antmicro/rdimm-ddr5-tester/data-center-rdimm-ddr5-tester.kicad_sch

## KiCad design data-center-rdimm-ddr5-tester.kicad_sch (2026-05-25)

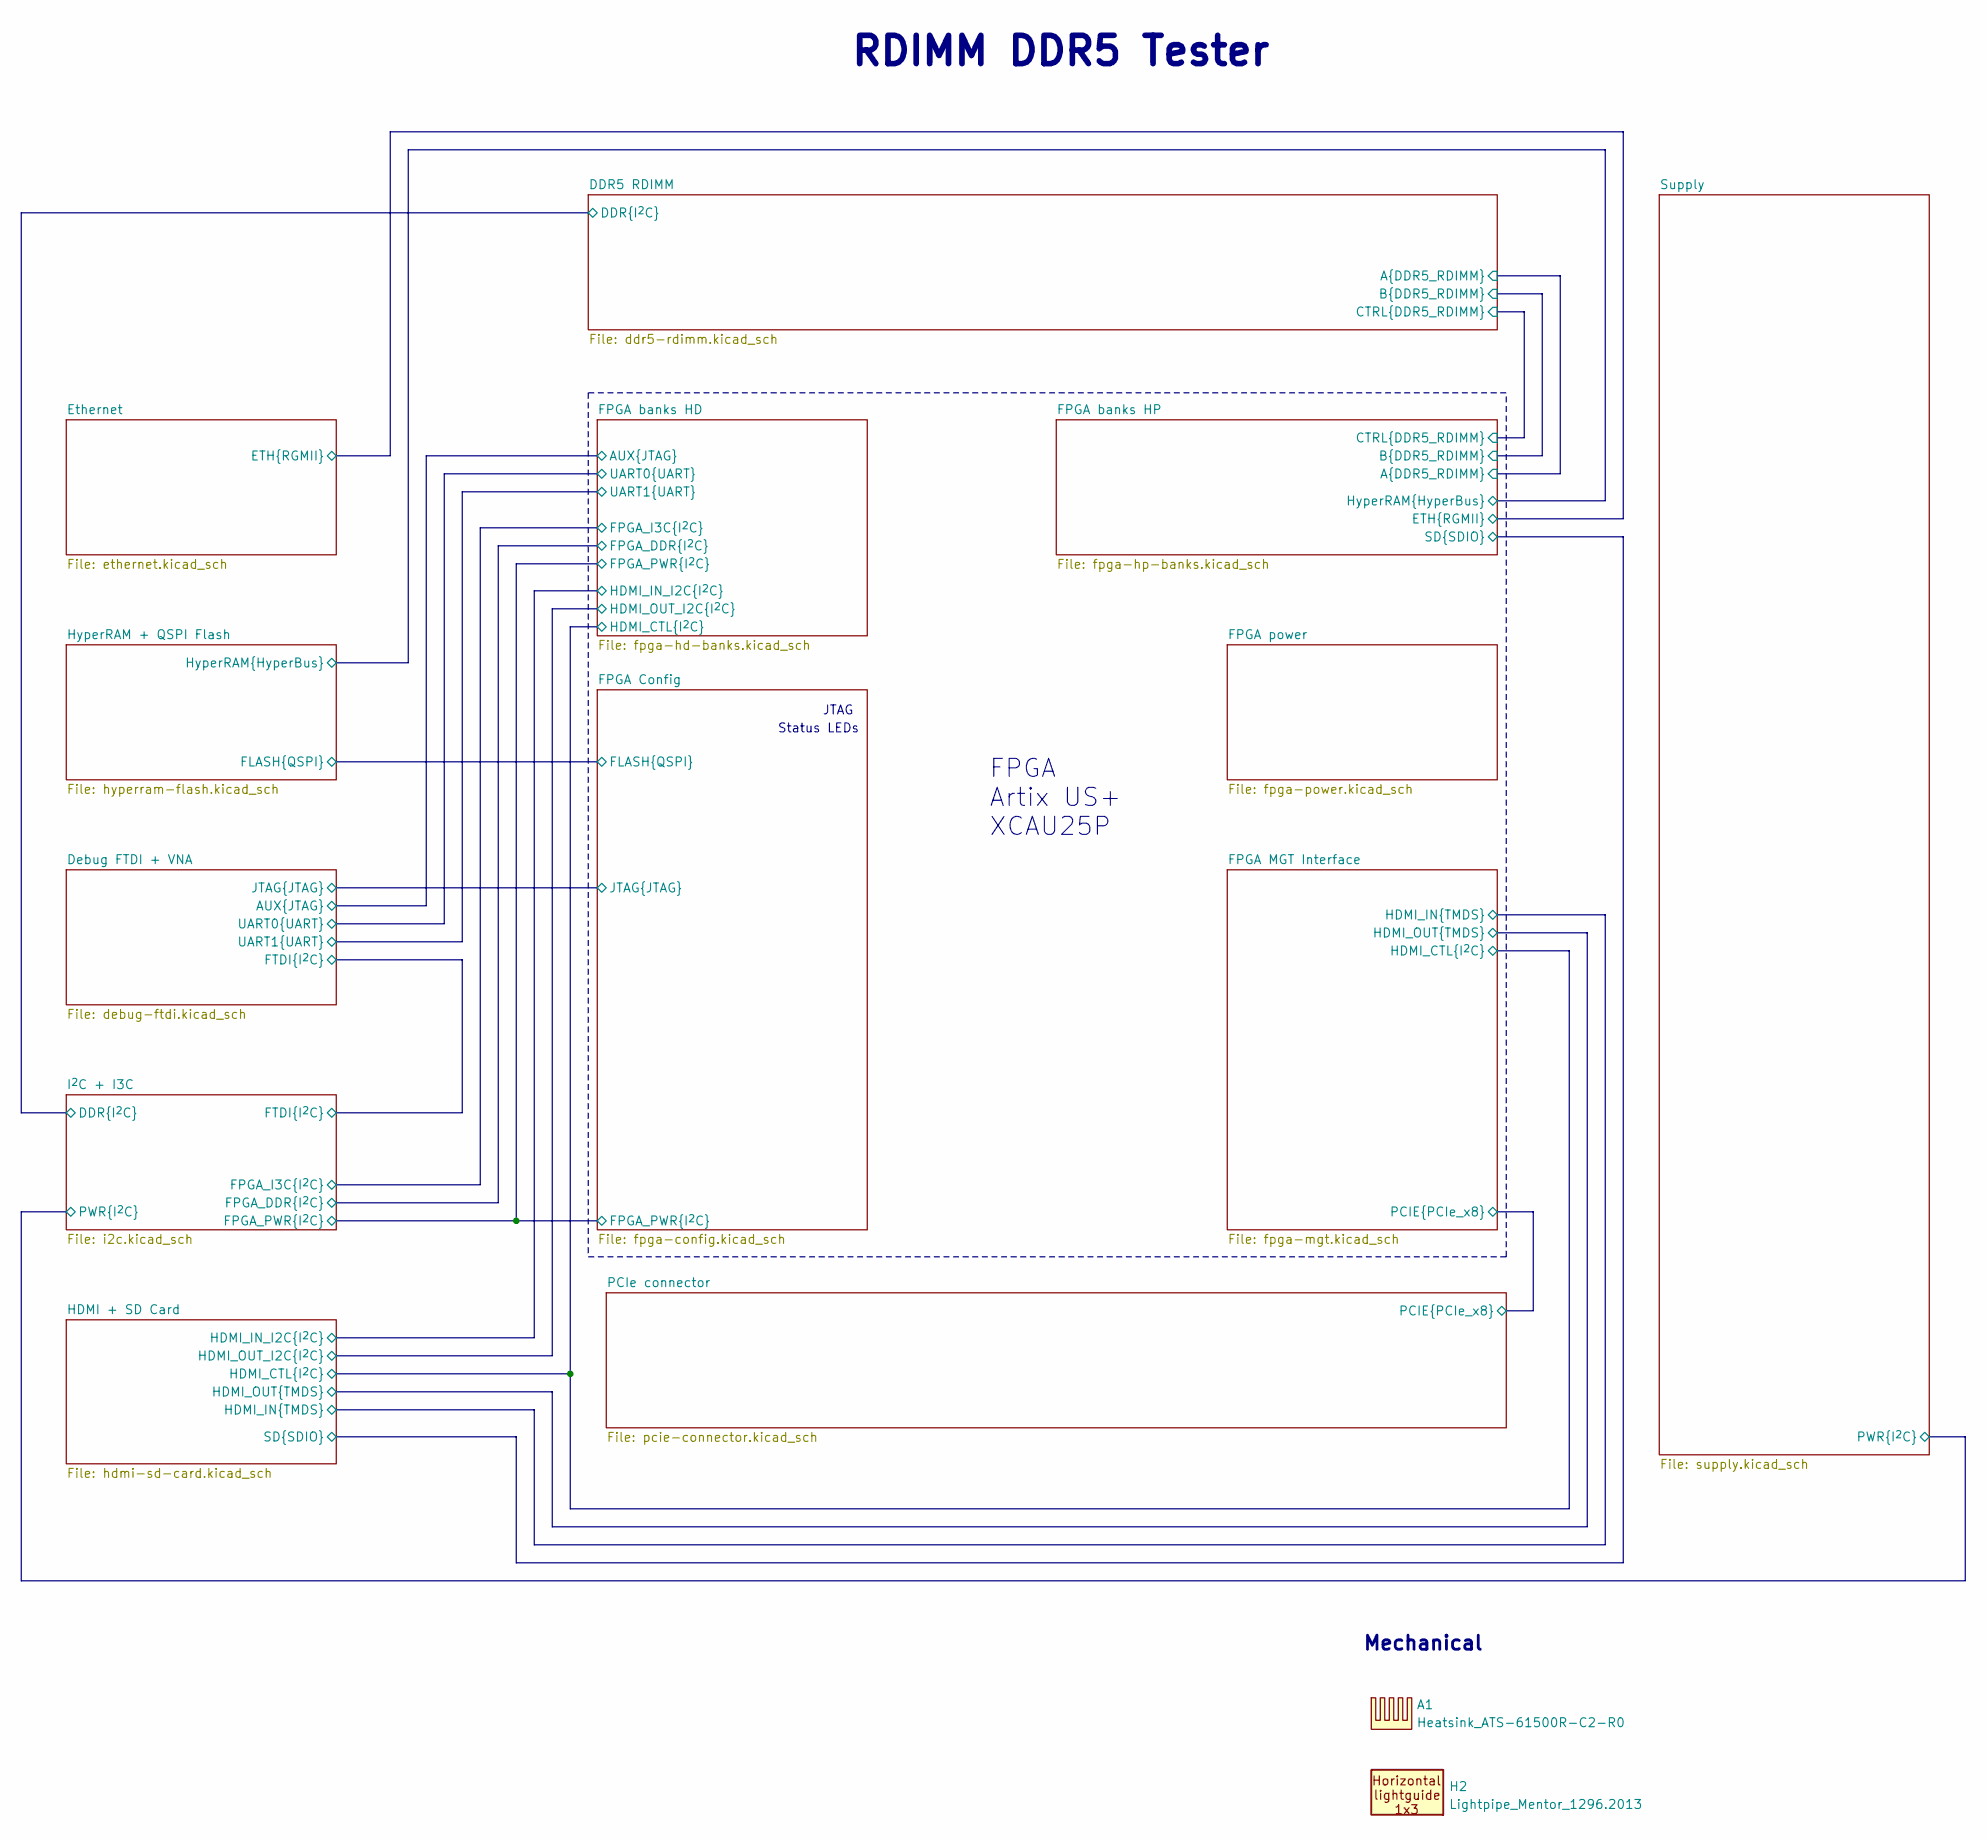
[picture p2: schematic data-center-rdimm-ddr5-tester.kicad_sch]

Parts:
A1: Heatsink_ATS-61500R-C2-R0; MPN ATS-61500R-C2-R0
H2: Lightpipe_Mentor_1296.2013; Mech_Lightpipe_Mentor_1296.2013; MPN 1296.2013

Notes on the sheet:
FPGA Artix US+ XCAU25P
JTAG
Mechanical
Status LEDs
RDIMM DDR5 Tester
