antmicro/rdimm-ddr5-tester/dc-dc-aux-mgt.kicad_sch

## KiCad design dc-dc-aux-mgt.kicad_sch (2026-05-25)

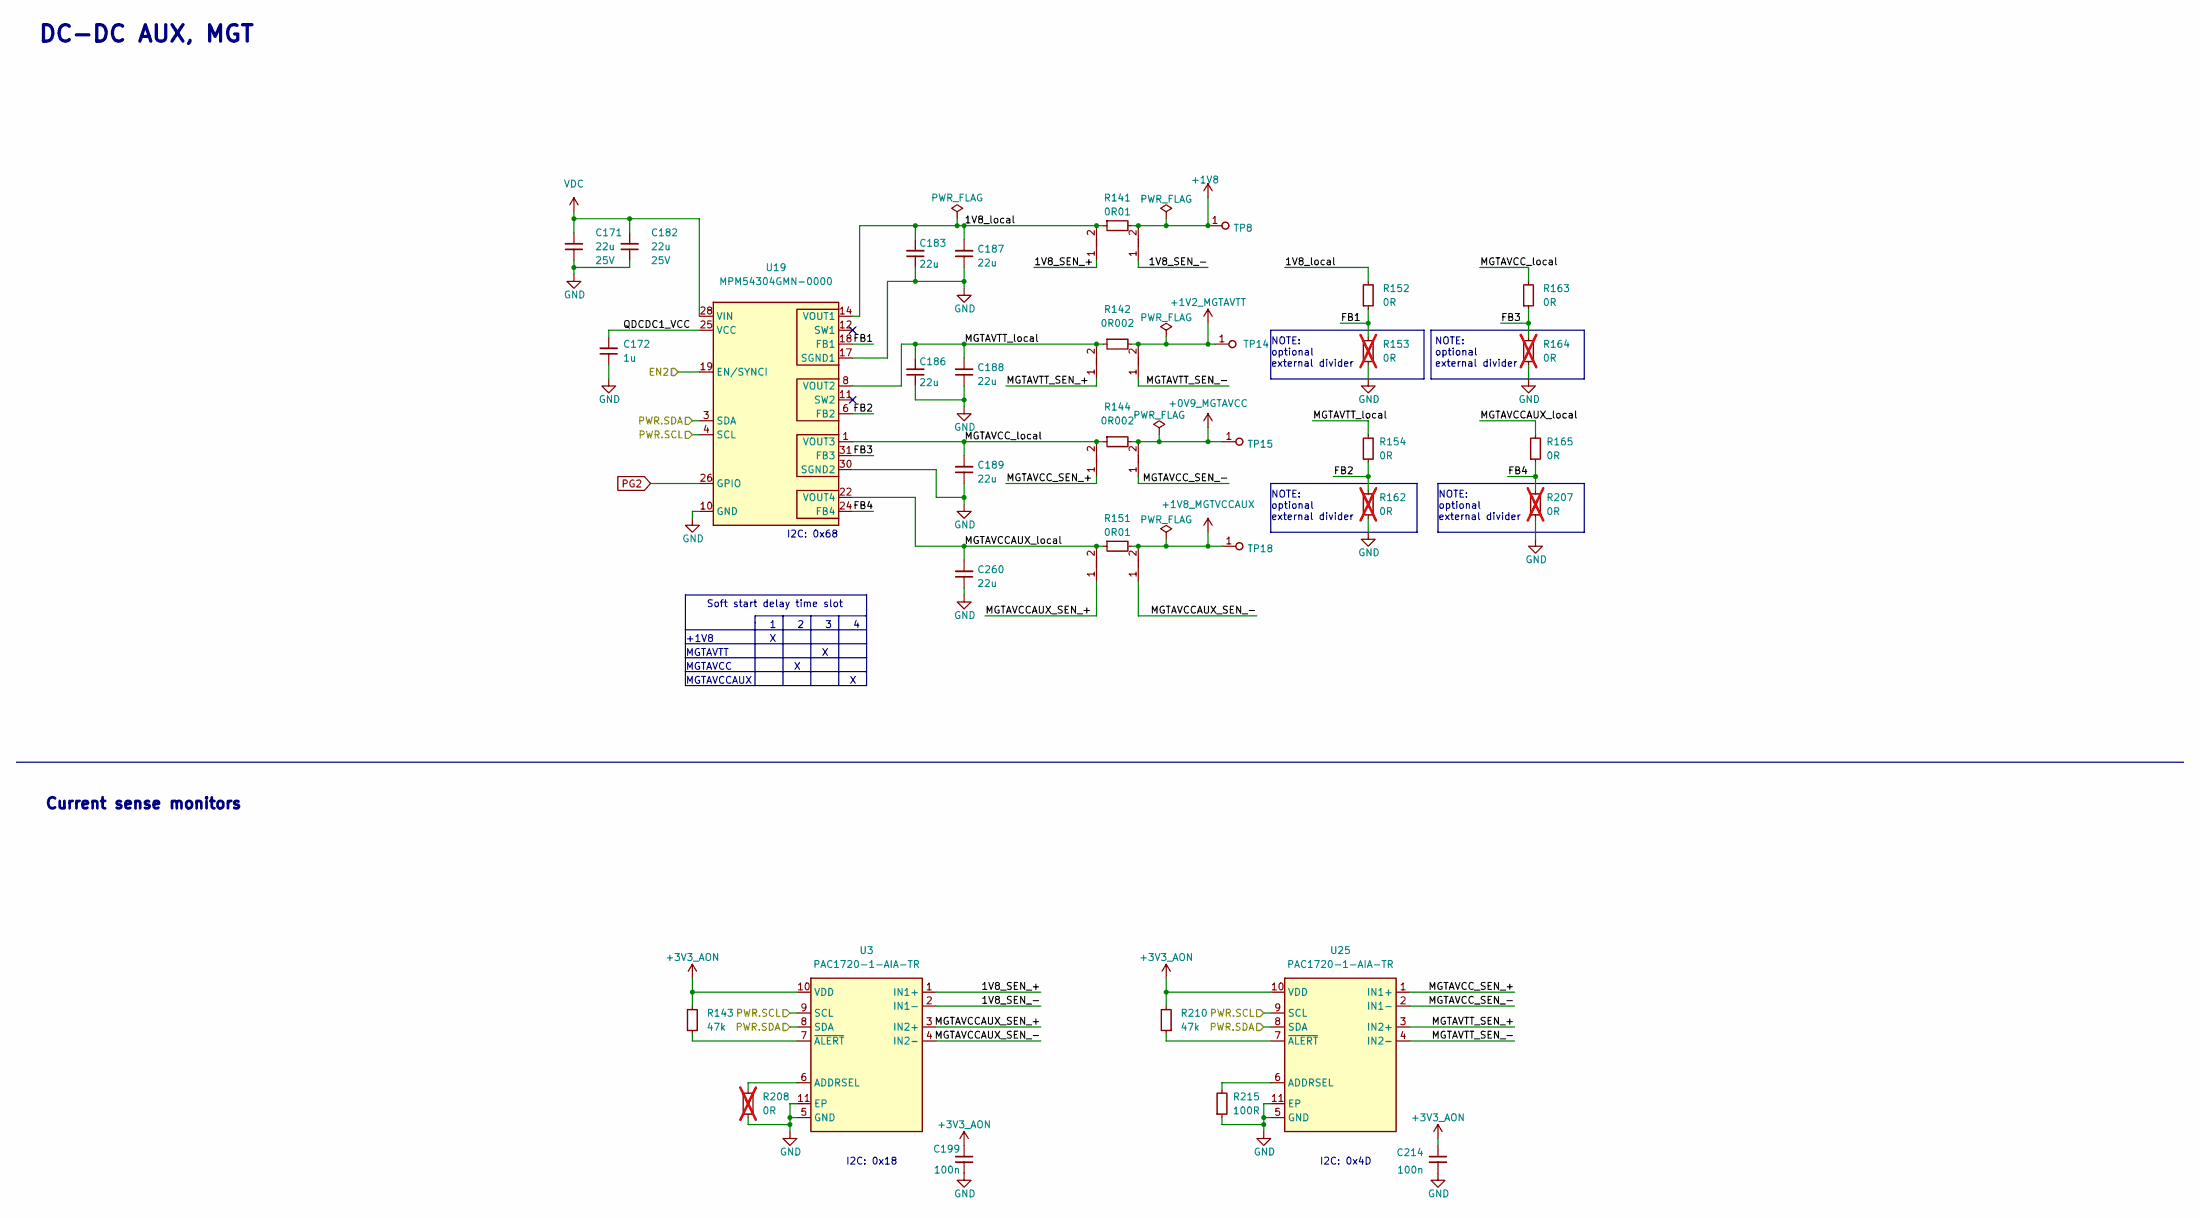
[picture p3: schematic dc-dc-aux-mgt.kicad_sch]

Parts:
C171, C182: C_22u_25V_0805; C_0805_2012Metric; Voltage 25V; MPN CL21A226MAYNNNE
C172: C_1u_0402; C_0402_1005Metric; MPN C1005X6S1A105K050BC
C183, C186, C187, C188, C189, C260: C_22u_0603; C_0603_1608Metric; MPN GRM188R60J226MEA0D
C199, C214: C_100n_0402; C_0402_1005Metric; Voltage 50V; MPN GRM155R61H104KE14D
NT1, NT2, NT3, NT4, NT9, NT10, NT11, NT12: Net-Tie_P0.127mm; NetTie-2_SMD_Pad0.127mm
R141, R151: R_0R01_1206; R_1206_3216Metric; Tolerance 1%; MPN RL1206FR-7W0R01L
R142, R144: R_0R002_0805; R_0805_2012Metric; Tolerance 1%; MPN PA0805FRE470R002L
R143, R210: R_47k_0402; R_0402_1005Metric; Tolerance 1%; MPN CR0402-FX-4702GLF
R152, R154, R163, R165: R_0R_0402; R_0402_1005Metric; MPN ERJ2GE0R00X
R153, R162, R164, R207, R208: R_0R_0402; R_0402_1005Metric; MPN ERJ2GE0R00X; not fitted
R215: R_100R_0402; R_0402_1005Metric; Tolerance 1%; MPN CR0402-FX-1000GLF
TP8, TP14, TP15, TP18: TP_1mm_SMD; TP_SMD_1mm
U3, U25: PAC1720-1; DFN-10-1EP_3x3mm; MPN PAC1720-1-AIA-TR
U19: MPM54304GMN; LGA-33_7x7mm_P0.65mm; MPN MPM54304GMN-0000

Connections:
1V8_SEN_+: NT1.1, U3.1 (IN1+)
1V8_SEN_-: NT9.1, U3.2 (IN1-)
1V8_local: C183.2, C187.2, NT1.2, R141.1, R152.2, U19.14 (VOUT1), U19.15 (VOUT1)
+0V9_MGTAVCC: NT11.2, R144.2, TP15.1
+1V2_MGTAVTT: NT10.2, R142.2, TP14.1
+1V8: NT9.2, R141.2, TP8.1
+1V8_MGTVCCAUX: NT12.2, R151.2, TP18.1
+3V3_AON: C199.1, C214.1, R143.2, R210.2, U3.10 (VDD), U25.10 (VDD)
EN2: U19.19 (EN/SYNCI)
FB1: R152.1, R153.2, U19.18 (FB1)
FB2: R154.1, R162.2, U19.6 (FB2)
FB3: R163.1, R164.2, U19.31 (FB3)
FB4: R165.1, R207.2, U19.24 (FB4)
GND: C171.1, C172.1, C182.1, C183.1, C186.1, C187.1, C188.1, C189.1, C199.2, C214.2, C260.1, R153.1, R162.1, R164.1, R207.1, R208.1, R215.1, U3.5 (GND), U3.11 (EP), U19.2 (GND), U19.5 (GND), U19.7 (GND), U19.10 (GND), U19.13 (GND), U19.16 (GND), U19.17 (SGND1), U19.20 (GND), U19.21 (GND), U19.27 (GND), U19.30 (SGND2), U19.33 (GND), U25.5 (GND), U25.11 (EP)
MGTAVCCAUX_SEN_+: NT4.1, U3.3 (IN2+)
MGTAVCCAUX_SEN_-: NT12.1, U3.4 (IN2-)
MGTAVCCAUX_local: C260.2, NT4.2, R151.1, R165.2, U19.22 (VOUT4), U19.23 (VOUT4)
MGTAVCC_SEN_+: NT3.1, U25.1 (IN1+)
MGTAVCC_SEN_-: NT11.1, U25.2 (IN1-)
MGTAVCC_local: C189.2, NT3.2, R144.1, R163.2, U19.1 (VOUT3), U19.32 (VOUT3)
MGTAVTT_SEN_+: NT2.1, U25.3 (IN2+)
MGTAVTT_SEN_-: NT10.1, U25.4 (IN2-)
MGTAVTT_local: C186.2, C188.2, NT2.2, R142.1, R154.2, U19.8 (VOUT2), U19.9 (VOUT2)
unnamed: R143.1, U3.7 (~ALERT)
unnamed: R208.2, U3.6 (ADDRSEL)
unnamed: R210.1, U25.7 (~ALERT)
unnamed: R215.2, U25.6 (ADDRSEL)
PG2: U19.26 (GPIO)
PWR.SCL: U3.9 (SCL), U19.4 (SCL), U25.9 (SCL)
PWR.SDA: U3.8 (SDA), U19.3 (SDA), U25.8 (SDA)
QDCDC1_VCC: C172.2, U19.25 (VCC)
VDC: C171.2, C182.2, U19.28 (VIN), U19.29 (VIN)

Notes on the sheet:
+1V8
NOTE: optional external divider
MGTAVTT
I2C: 0x4D
I2C: 0x18
Current sense monitors
DC-DC AUX, MGT
1 2 3 4
Soft start delay time slot
MGTAVCCAUX
I2C: 0x68
MGTAVCC
