antmicro/rdimm-ddr5-tester/dc-dc-io.kicad_sch

## KiCad design dc-dc-io.kicad_sch (2026-05-25)

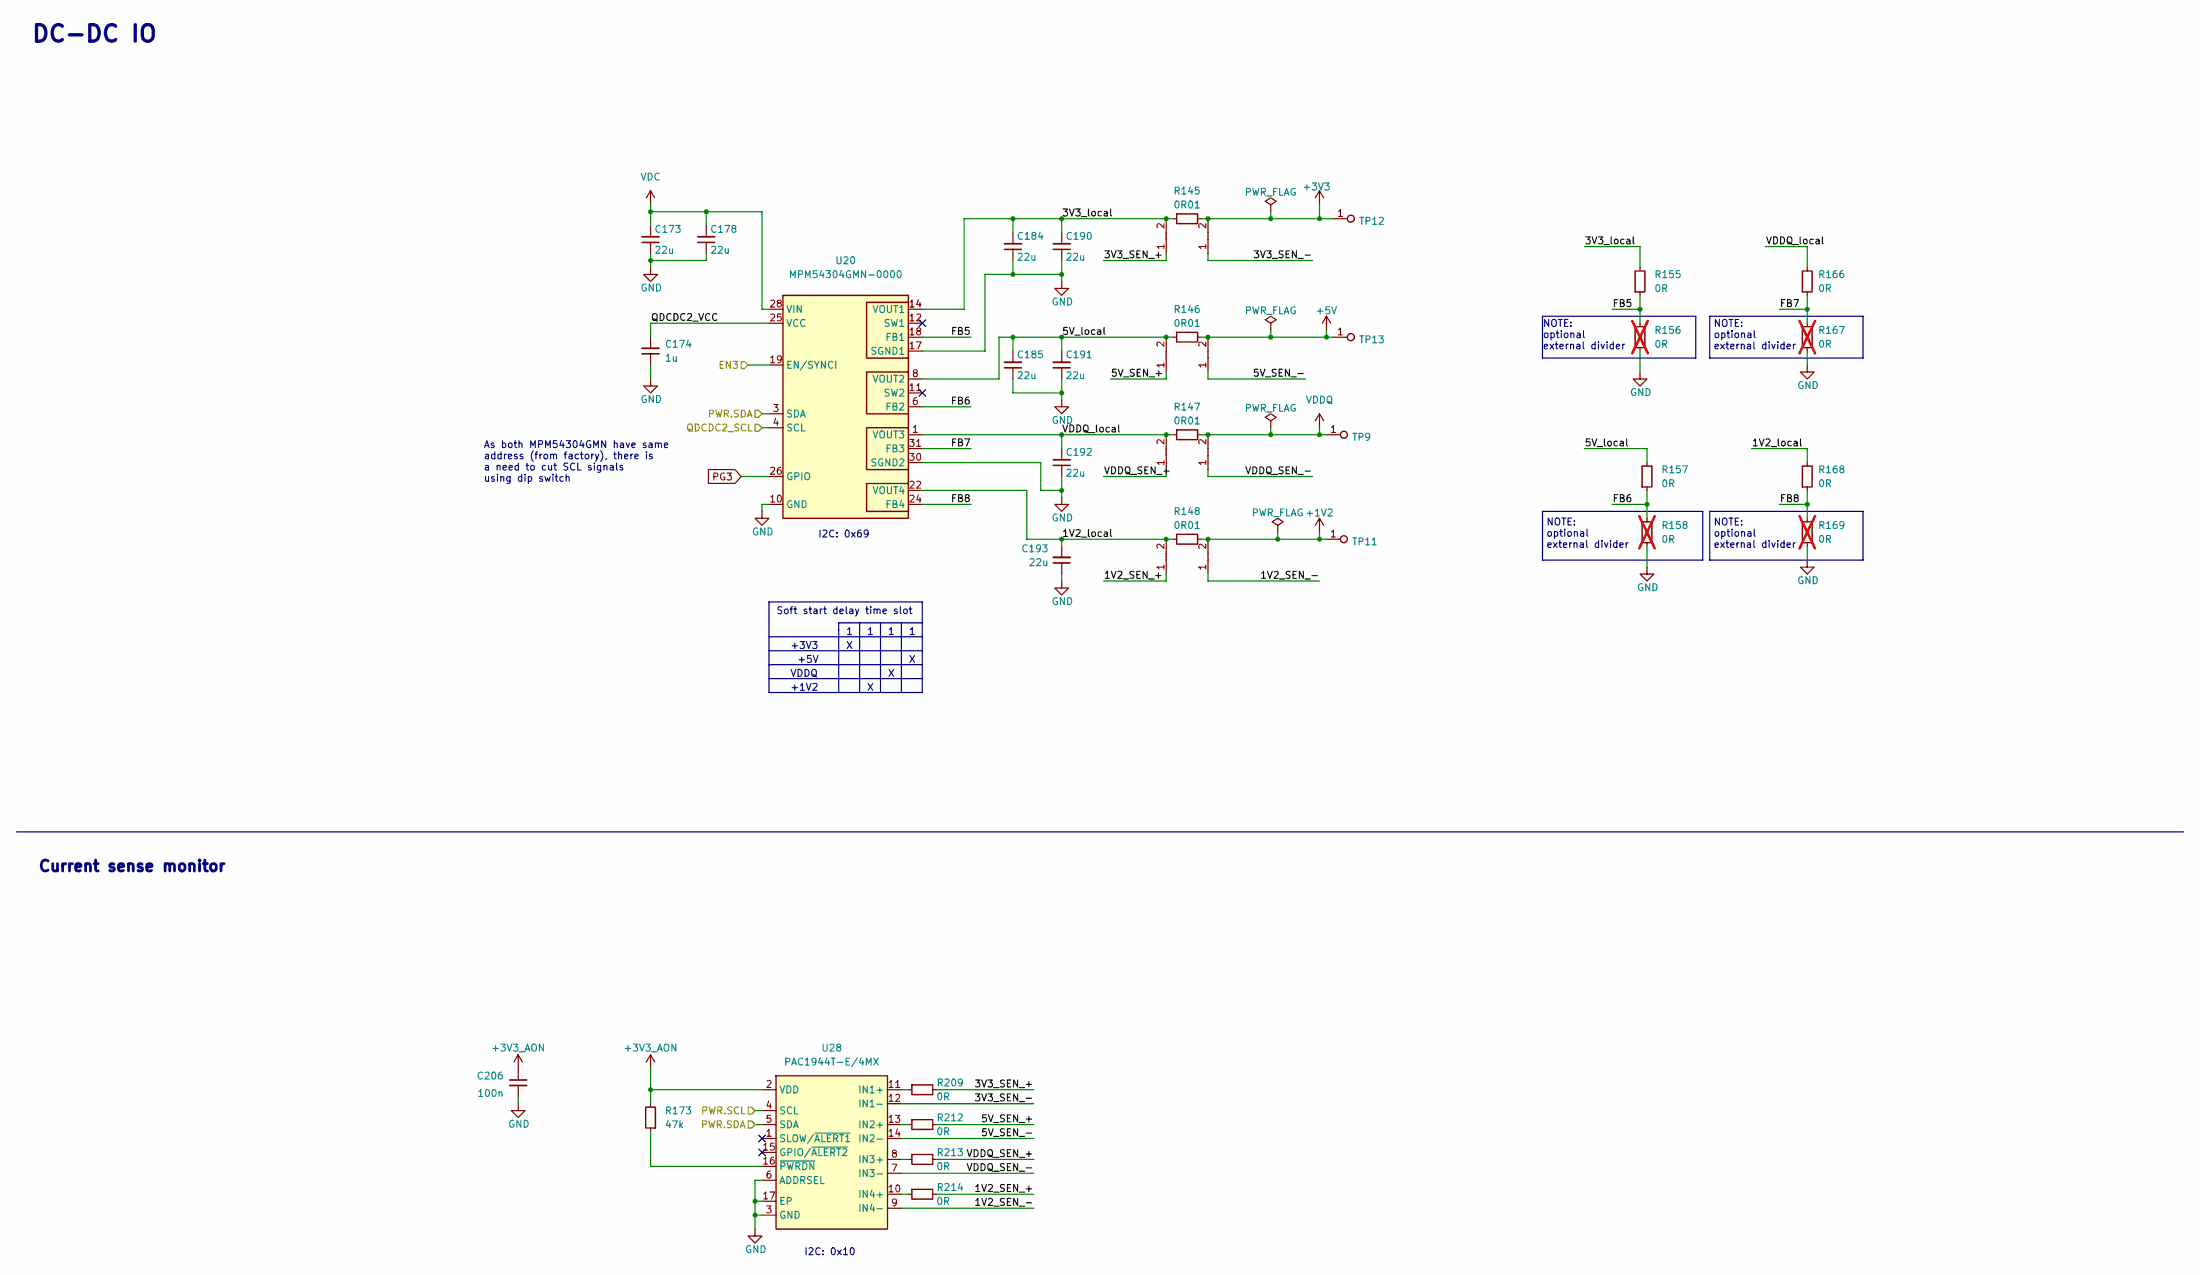
[picture p4: schematic dc-dc-io.kicad_sch]

Parts:
C173, C178: C_22u_25V_0805; C_0805_2012Metric; Voltage 25V; MPN CL21A226MAYNNNE
C174: C_1u_0402; C_0402_1005Metric; MPN C1005X6S1A105K050BC
C184, C185, C190, C191, C192, C193: C_22u_0603; C_0603_1608Metric; MPN GRM188R60J226MEA0D
C206: C_100n_0402; C_0402_1005Metric; Voltage 50V; MPN GRM155R61H104KE14D
NT5, NT6, NT7, NT8, NT13, NT14, NT15, NT16: Net-Tie_P0.127mm; NetTie-2_SMD_Pad0.127mm
R145, R146, R147, R148: R_0R01_1206; R_1206_3216Metric; Tolerance 1%; MPN RL1206FR-7W0R01L
R155, R157, R166, R168, R209, R212, R213, R214: R_0R_0402; R_0402_1005Metric; MPN ERJ2GE0R00X
R156, R158, R167, R169: R_0R_0402; R_0402_1005Metric; MPN ERJ2GE0R00X; not fitted
R173: R_47k_0402; R_0402_1005Metric; Tolerance 1%; MPN CR0402-FX-4702GLF
TP9, TP11, TP12, TP13: TP_1mm_SMD; TP_SMD_1mm
U20: MPM54304GMN; LGA-33_7x7mm_P0.65mm; MPN MPM54304GMN-0000
U28: PAC1944T-E; VQFN-16-1EP_3x3mm_P0.5mm_EP1.1x1.1mm; MPN PAC1944T-E/4MX

Connections:
1V2_SEN_+: NT8.1, R214.2
1V2_SEN_-: NT16.1, U28.9 (IN4-)
1V2_local: C193.2, NT8.2, R148.1, R168.2, U20.22 (VOUT4), U20.23 (VOUT4)
3V3_SEN_+: NT5.1, R209.2
3V3_SEN_-: NT13.1, U28.12 (IN1-)
3V3_local: C184.2, C190.2, NT5.2, R145.1, R155.2, U20.14 (VOUT1), U20.15 (VOUT1)
5V_SEN_+: NT6.1, R212.2
5V_SEN_-: NT14.1, U28.14 (IN2-)
5V_local: C185.2, C191.2, NT6.2, R146.1, R157.2, U20.8 (VOUT2), U20.9 (VOUT2)
+1V2: NT16.2, R148.2, TP11.1
+3V3: NT13.2, R145.2, TP12.1
+3V3_AON: C206.1, R173.2, U28.2 (VDD)
+5V: NT14.2, R146.2, TP13.1
EN3: U20.19 (EN/SYNCI)
FB5: R155.1, R156.2, U20.18 (FB1)
FB6: R157.1, R158.2, U20.6 (FB2)
FB7: R166.1, R167.2, U20.31 (FB3)
FB8: R168.1, R169.2, U20.24 (FB4)
GND: C173.1, C174.1, C178.1, C184.1, C185.1, C190.1, C191.1, C192.1, C193.1, C206.2, R156.1, R158.1, R167.1, R169.1, U20.2 (GND), U20.5 (GND), U20.7 (GND), U20.10 (GND), U20.13 (GND), U20.16 (GND), U20.17 (SGND1), U20.20 (GND), U20.21 (GND), U20.27 (GND), U20.30 (SGND2), U20.33 (GND), U28.3 (GND), U28.6 (ADDRSEL), U28.17 (EP)
unnamed: R173.1, U28.16 (~PWRDN)
unnamed: R209.1, U28.11 (IN1+)
unnamed: R212.1, U28.13 (IN2+)
unnamed: R213.1, U28.8 (IN3+)
unnamed: R214.1, U28.10 (IN4+)
PG3: U20.26 (GPIO)
PWR.SCL: U28.4 (SCL)
PWR.SDA: U20.3 (SDA), U28.5 (SDA)
QDCDC2_SCL: U20.4 (SCL)
QDCDC2_VCC: C174.2, U20.25 (VCC)
VDC: C173.2, C178.2, U20.28 (VIN), U20.29 (VIN)
VDDQ: NT15.2, R147.2, TP9.1
VDDQ_SEN_+: NT7.1, R213.2
VDDQ_SEN_-: NT15.1, U28.7 (IN3-)
VDDQ_local: C192.2, NT7.2, R147.1, R166.2, U20.1 (VOUT3), U20.32 (VOUT3)

Notes on the sheet:
+1V2
+3V3
Current sense monitor
DC-DC IO
VDDQ
As both MPM54304GMN have same address (from factory), there is a need to cut SCL signals using dip switch
NOTE: optional external divider
+5V
I2C: 0x10
I2C: 0x69
Soft start delay time slot
