antmicro/rdimm-ddr5-tester/dc-dc-vccint.kicad_sch

## KiCad design dc-dc-vccint.kicad_sch (2026-05-25)

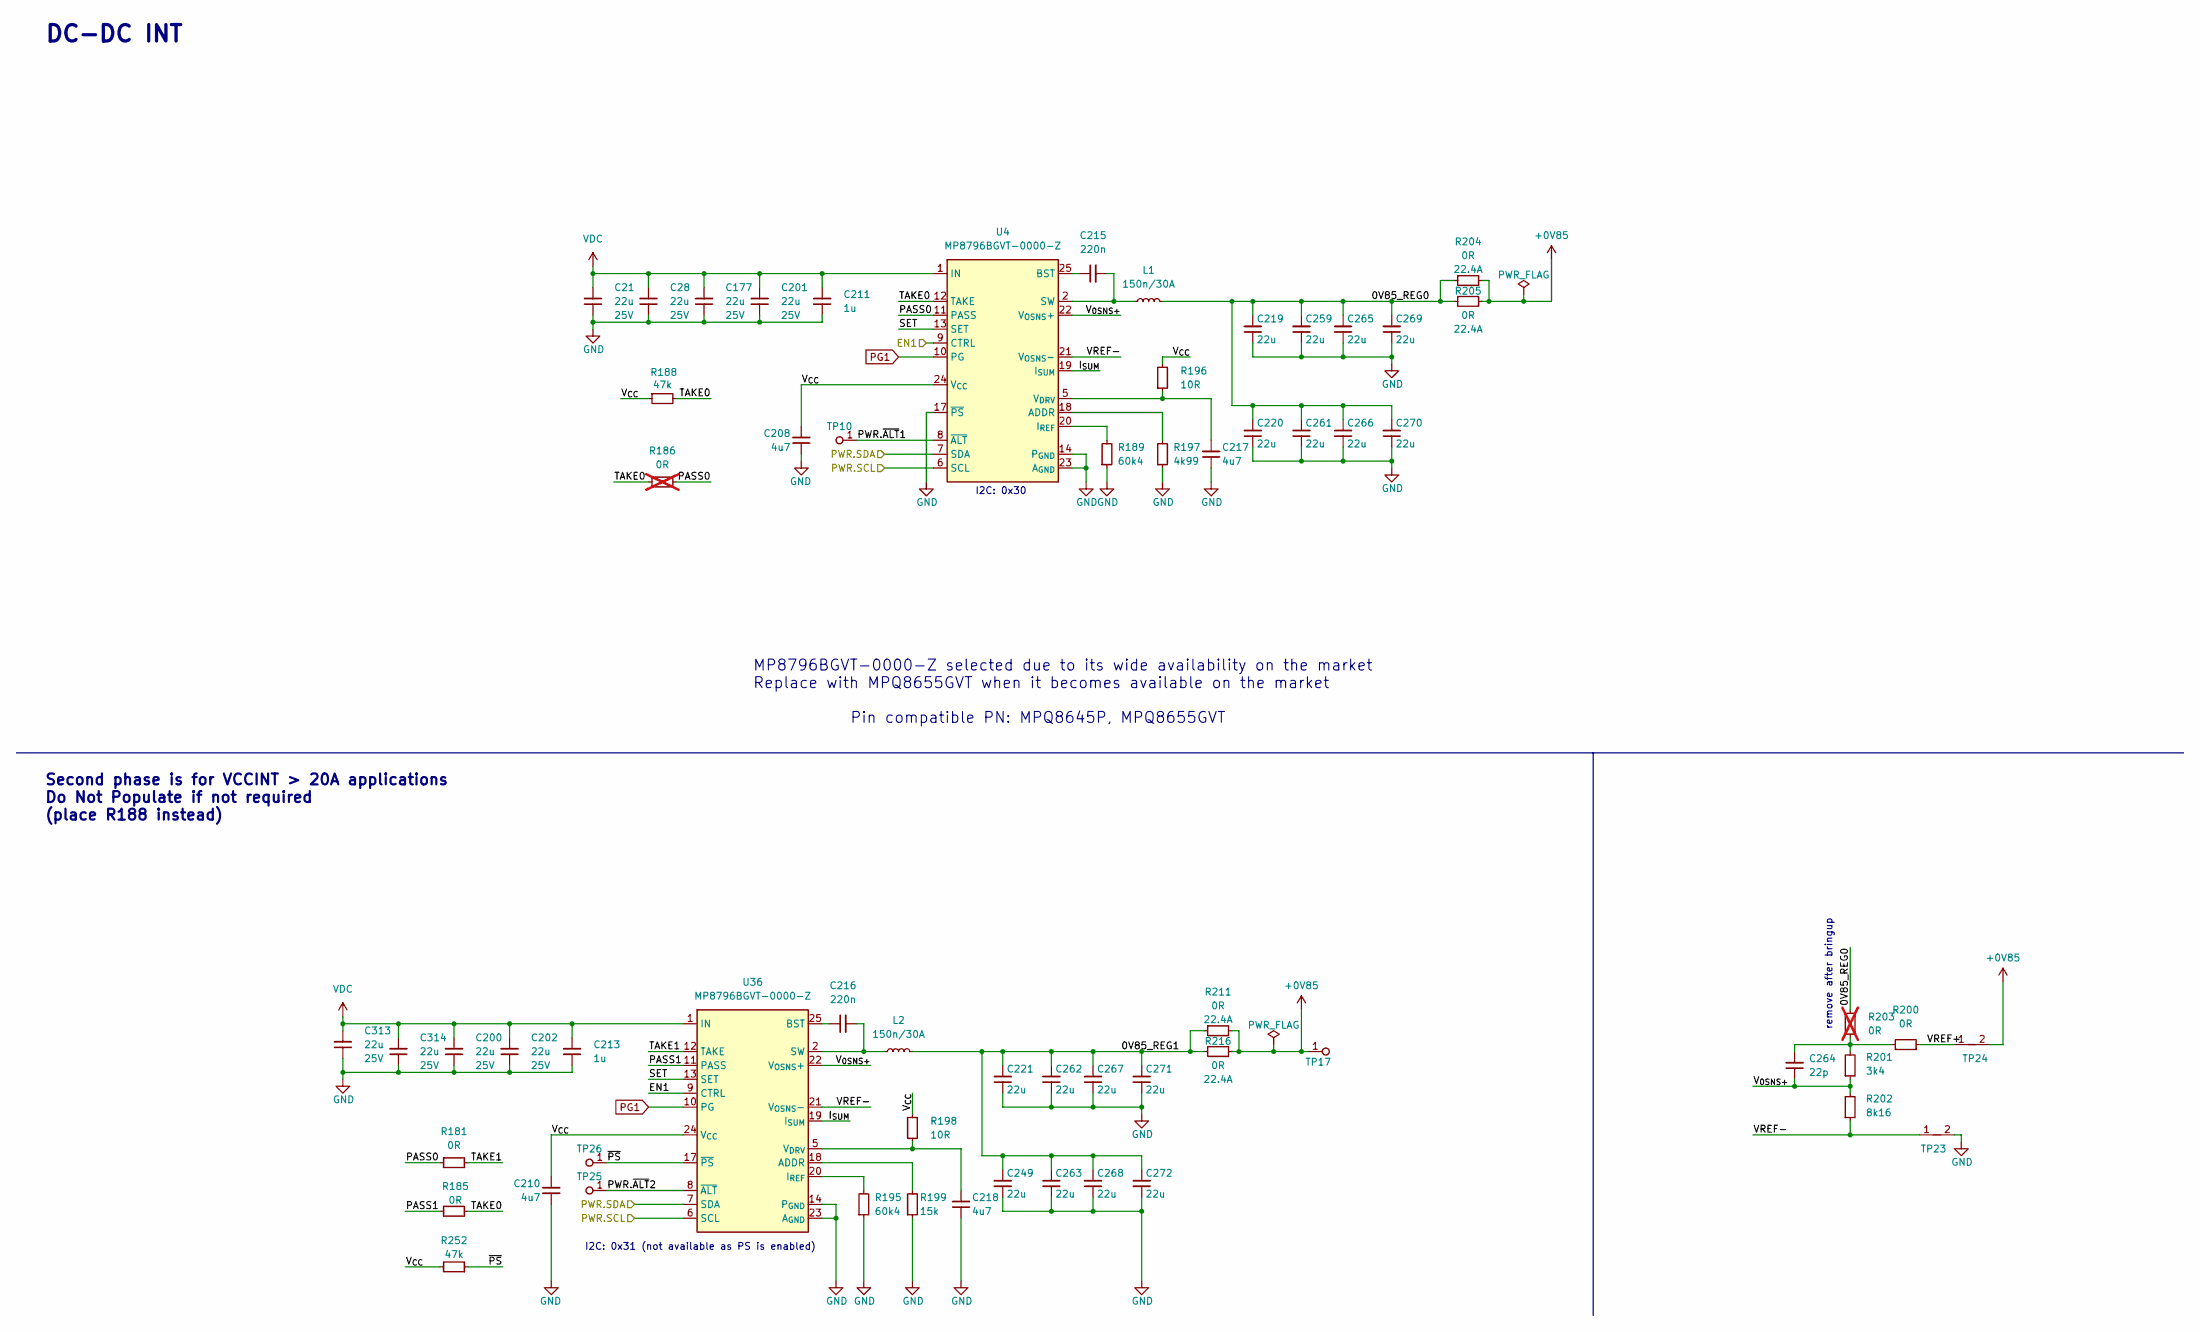
[picture p5: schematic dc-dc-vccint.kicad_sch]

Parts:
C21, C28, C177, C200, C201, C202, C313, C314: C_22u_25V_0805; C_0805_2012Metric; Voltage 25V; MPN CL21A226MAYNNNE
C208, C210, C217, C218: C_4u7_25V_0402; C_0402_1005Metric; Voltage 25V; MPN GRM155C61E475ME15J
C211, C213: C_1u_25V_0402; C_0402_1005Metric; Voltage 25V; MPN GRM155R61E105KE11J
C215, C216: C_220n_16V_0402; C_0402_1005Metric; Voltage 16V; MPN GRM155R71C224KA12D
C219, C220, C221, C249, C259, C261, C262, C263, C265, C266, C267, C268, C269, C270, C271, C272: C_22u_0603; C_0603_1608Metric; MPN GRM188R60J226MEA0D
C264: C_22p_0402; C_0402_1005Metric; MPN CC0402JRNPO9BN220
L1, L2: L_150n_30A_WE-HCM-7050; L_WE-HCM-7050; MPN 744302015
R181, R185, R200: R_0R_0402; R_0402_1005Metric; MPN ERJ2GE0R00X
R186, R203: R_0R_0402; R_0402_1005Metric; MPN ERJ2GE0R00X; not fitted
R188, R252: R_47k_0402; R_0402_1005Metric; Tolerance 1%; MPN CR0402-FX-4702GLF
R189, R195: R_60k4_0402; R_0402_1005Metric; Tolerance 1%; MPN CR0402-FX-6042GLF
R196, R198: R_10R_0402; R_0402_1005Metric; Tolerance 1%; MPN CR0402-FX-10R0GLF
R197: R_4k99_0402; R_0402_1005Metric; Tolerance 1%; MPN CR0402-FX-4991GLF
R199: R_15k_0402; R_0402_1005Metric; Tolerance 1%; MPN CR0402-FX-1502GLF
R201: R_3k4_0402; R_0402_1005Metric; Tolerance 0.1%; MPN RT0402BRD073K4L
R202: R_8k16_0402; R_0402_1005Metric; Tolerance 0.1%; MPN RT0402BRE078K16L
R204, R205, R211, R216: R_0R_22.4A_0603; R_0603_1608Metric; MPN PMR03EZPJ000
TP10, TP17, TP25, TP26: TP_1mm_SMD; TP_SMD_1mm
TP23, TP24: Net-Tie_P0.127mm; NetTie-2_SMD_Pad0.127mm
U4, U36: MP8796B; TQFN-25_4x5mm; MPN MP8796BGVT-0000-Z

Connections:
0V85_REG0: C219.2, C220.2, C259.2, C261.2, C265.2, C266.2, C269.2, C270.2, L1.2, R203.2, R204.1, R205.1
0V85_REG1: C221.2, C249.2, C262.2, C263.2, C267.2, C268.2, C271.2, C272.2, L2.2, R211.1, R216.1
+0V85: R204.2, R205.2, R211.2, R216.2, TP17.1, TP24.2
EN1: U4.9 (CTRL), U36.9 (CTRL)
GND: C21.1, C28.1, C177.1, C200.1, C201.1, C202.1, C208.1, C210.1, C211.1, C213.1, C217.1, C218.1, C219.1, C220.1, C221.1, C249.1, C259.1, C261.1, C262.1, C263.1, C265.1, C266.1, C267.1, C268.1, C269.1, C270.1, C271.1, C272.1, C313.1, C314.1, R189.1, R195.1, R197.1, R199.1, TP23.2, U4.4 (P_{GND}), U4.14 (P_{GND}), U4.15 (P_{GND}), U4.17 (~PS), U4.23 (A_{GND}), U36.4 (P_{GND}), U36.14 (P_{GND}), U36.15 (P_{GND}), U36.23 (A_{GND})
I_{SUM}: U4.19 (I_{SUM}), U36.19 (I_{SUM})
unnamed: C215.1, U4.25 (BST)
unnamed: C215.2, L1.1, U4.2 (SW), U4.3 (SW)
unnamed: C216.1, U36.25 (BST)
unnamed: C216.2, L2.1, U36.2 (SW), U36.3 (SW)
unnamed: C217.2, R196.1, U4.5 (V_{DRV})
unnamed: C218.2, R198.1, U36.5 (V_{DRV})
unnamed: C264.2, R200.2, R201.2, R203.1
unnamed: R189.2, U4.20 (I_{REF})
unnamed: R195.2, U36.20 (I_{REF})
unnamed: R197.2, U4.18 (ADDR)
unnamed: R199.2, U36.18 (ADDR)
PASS0: R181.1, R186.2, U4.11 (PASS)
PASS1: R185.1, U36.11 (PASS)
PG1: U4.10 (PG), U36.10 (PG)
PWR.SCL: U4.6 (SCL), U36.6 (SCL)
PWR.SDA: U4.7 (SDA), U36.7 (SDA)
PWR.~ALT1: TP10.1, U4.8 (~ALT)
PWR.~ALT2: TP25.1, U36.8 (~ALT)
SET: U4.13 (SET), U36.13 (SET)
TAKE0: R185.2, R186.1, R188.2, U4.12 (TAKE)
TAKE1: R181.2, U36.12 (TAKE)
VDC: C21.2, C28.2, C177.2, C200.2, C201.2, C202.2, C211.2, C213.2, C313.2, C314.2, U4.1 (IN), U4.16 (IN), U36.1 (IN), U36.16 (IN)
VREF+: R200.1, TP24.1
VREF-: R202.1, TP23.1, U4.21 (V_{OSNS}-), U36.21 (V_{OSNS}-)
V_{0SNS+}: C264.1, R201.1, R202.2, U4.22 (V_{OSNS}+), U36.22 (V_{OSNS}+)
V_{CC}: C208.2, C210.2, R188.1, R196.2, R198.2, R252.2, U4.24 (V_{CC}), U36.24 (V_{CC})
~PS: R252.1, TP26.1, U36.17 (~PS)

Notes on the sheet:
DC-DC INT
MP8796BGVT-0000-Z selected due to its wide availability on the market Replace with MPQ8655GVT when it becomes available on the market
I2C: 0x31 (not available as PS is enabled)
I2C: 0x30
remove after bringup
Second phase is for VCCINT > 20A applications Do Not Populate if not required (place R188 instead)
Pin compatible PN: MPQ8645P, MPQ8655GVT
