antmicro/rdimm-ddr5-tester/ddr5-rdimm.kicad_sch

## KiCad design ddr5-rdimm.kicad_sch (2026-05-21)

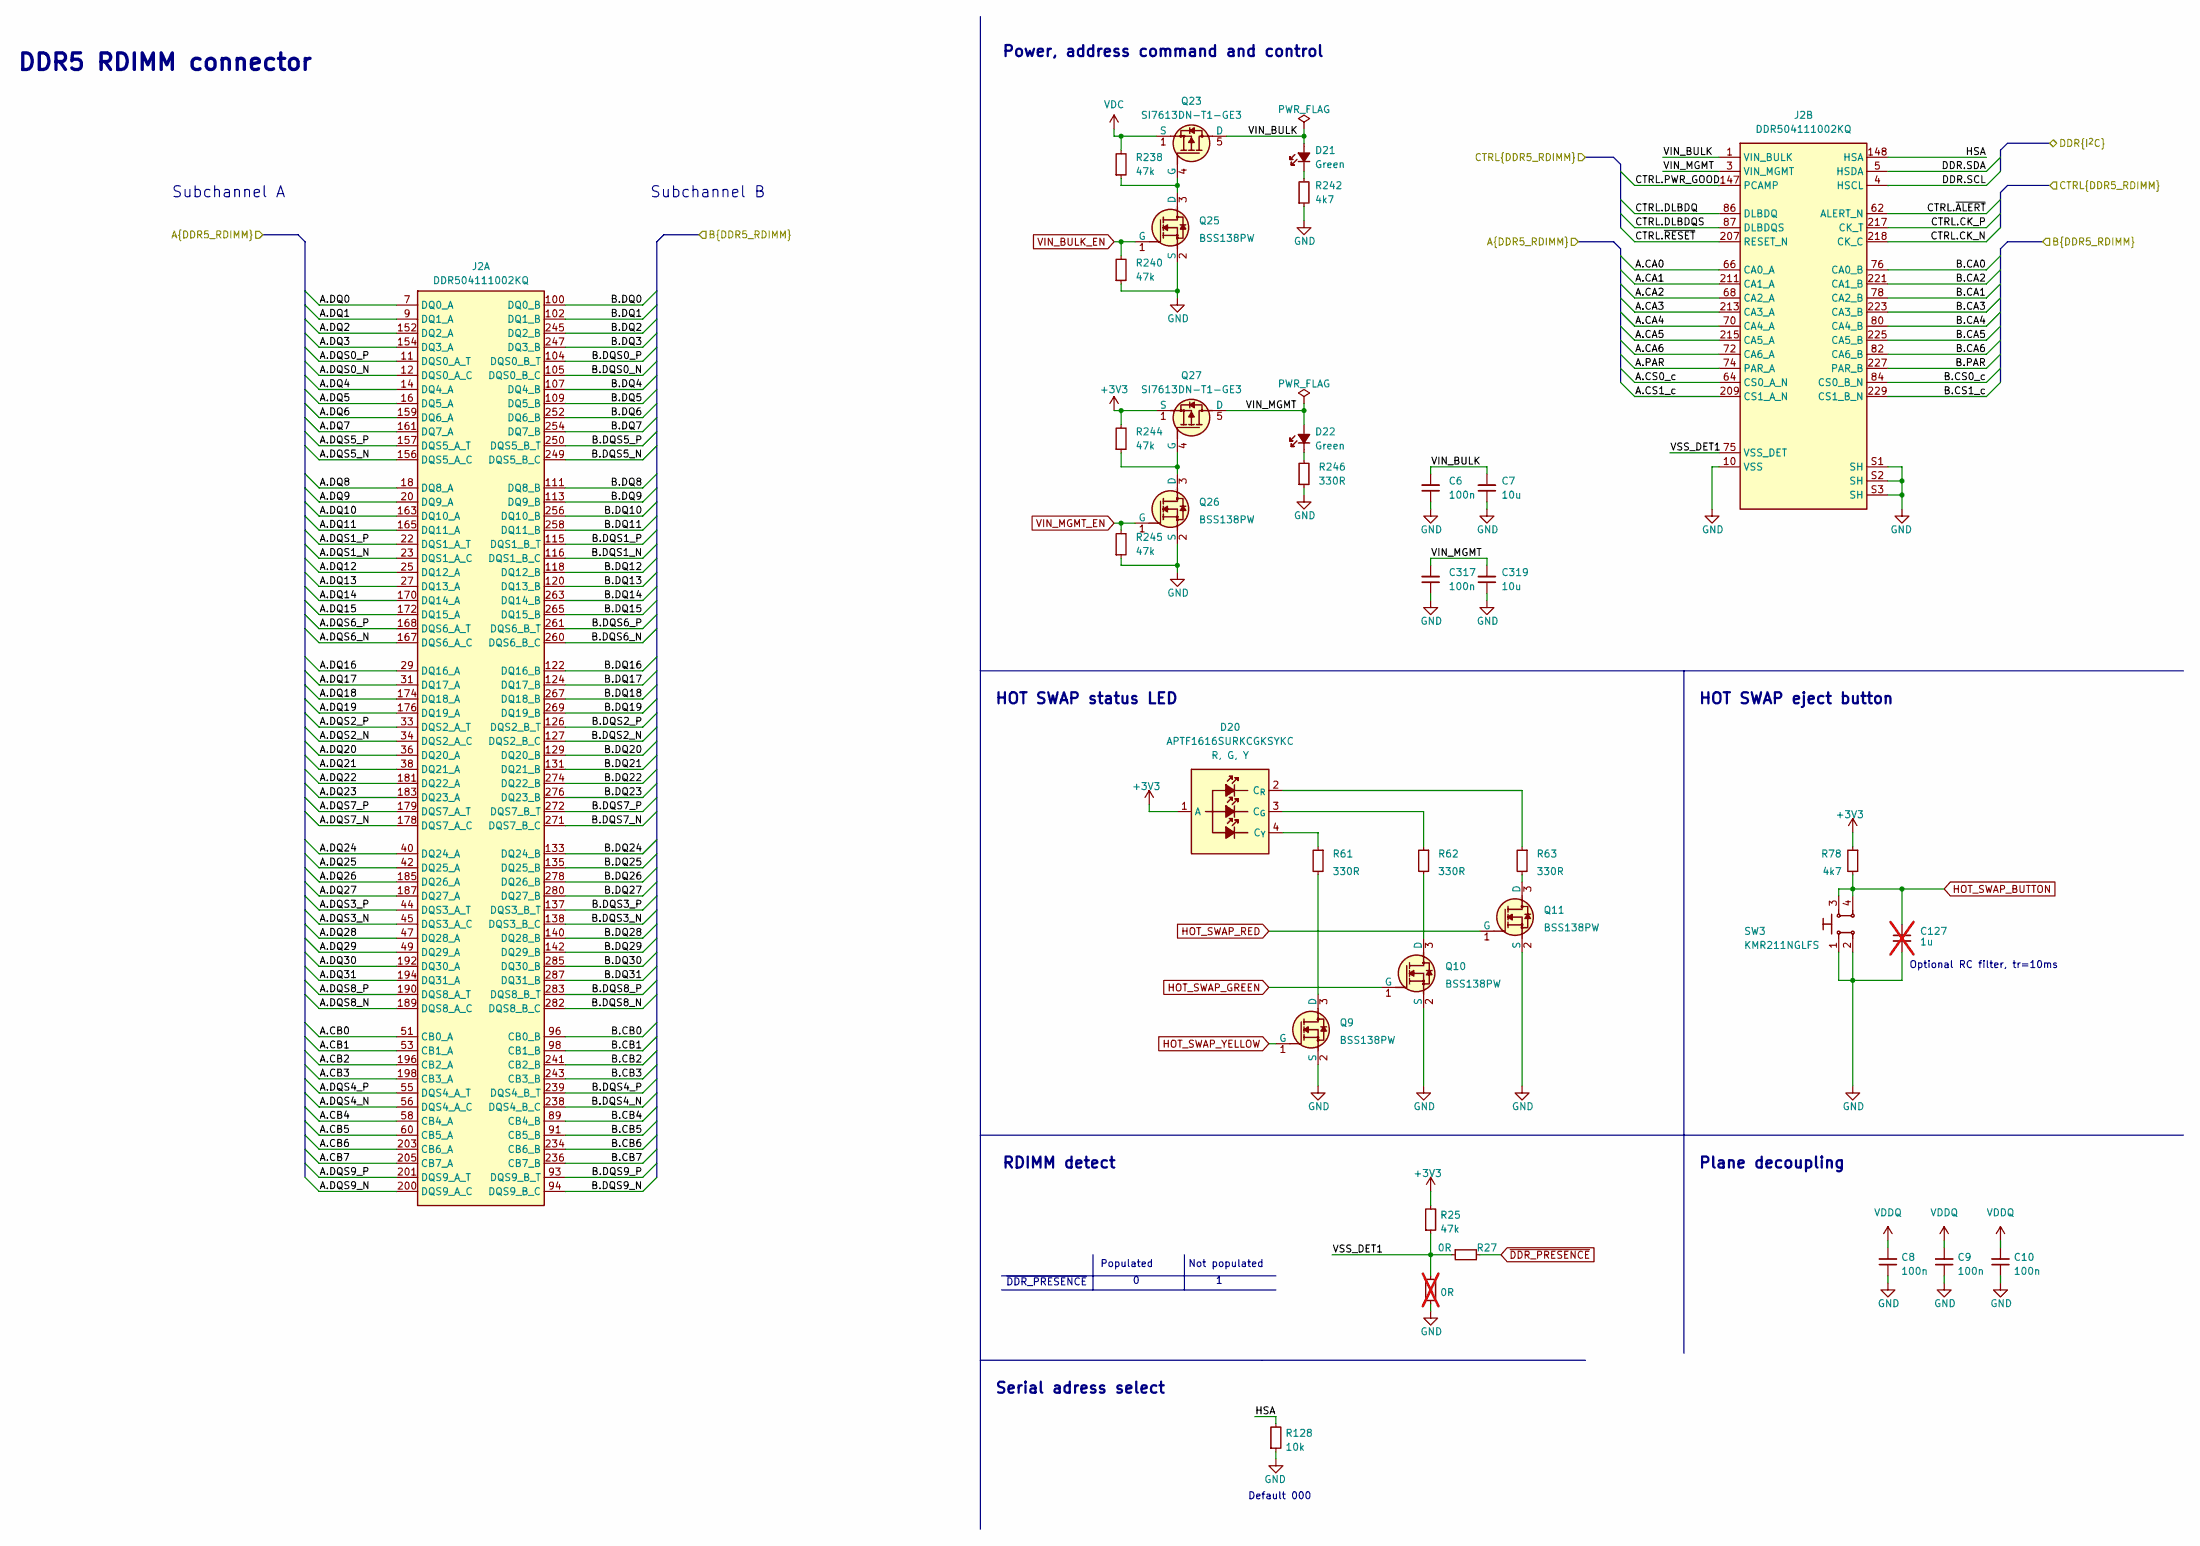
[picture p6: schematic ddr5-rdimm.kicad_sch]

Parts:
C6, C8, C9, C10, C317: C_100n_0402; C_0402_1005Metric; Voltage 50V; MPN GRM155R61H104KE14D
C7, C319: C_10u_25V_0603; C_0603_1608Metric; Voltage 25V; MPN C1608X5R1E106M080AC
C127: C_1u_0402; C_0402_1005Metric; MPN C1005X6S1A105K050BC; not fitted
D20: LED_RGY_0606_APTF1616SURKCGKSYKC; LED_RGY_1.6x1.6mm_APTF1616; MPN APTF1616SURKCGKSYKC
D21, D22: LED_G_0402_VLMTG1500-GS08; LED_0402_1005Metric_G; MPN VLMTG1500-GS08
J2: Bus_DDR5_DDR504111002KQ; Bus_DDR5_Socket_Amphenol_DDR504111002KQ; MPN DDR504111002KQ
Q9, Q10, Q11, Q25, Q26: BSS138PW; SC70-3; MPN BSS138PW
Q23, Q27: SI7613DN-T1-GE3; Vishay_PowerPAK_1212-8_Single; MPN SI7613DN-T1-GE3
R25, R238, R240, R244, R245: R_47k_0402; R_0402_1005Metric; Tolerance 1%; MPN CR0402-FX-4702GLF
R26: R_0R_0402; R_0402_1005Metric; MPN ERJ2GE0R00X; not fitted
R27: R_0R_0402; R_0402_1005Metric; MPN ERJ2GE0R00X
R61, R62, R63, R246: R_330R_0402; R_0402_1005Metric; Tolerance 1%; MPN CR0402-FX-3300GLF
R78, R242: R_4k7_0402; R_0402_1005Metric; Tolerance 1%; MPN CR0402-FX-4701GLF
R128: R_10k_0402; R_0402_1005Metric; Tolerance 1%; MPN CR0402-FX-1002GLF
SW3: SW_KMR211NGLFS_SMD; MPN KMR211NGLFS

Connections:
+3V3: D20.1 (A), Q27.1 (S), Q27.2 (S), Q27.3 (S), R25.2, R78.1, R244.2
A.CA0: J2.66 (CA0_A)
A.CA1: J2.211 (CA1_A)
A.CA2: J2.68 (CA2_A)
A.CA3: J2.213 (CA3_A)
A.CA4: J2.70 (CA4_A)
A.CA5: J2.215 (CA5_A)
A.CA6: J2.72 (CA6_A)
A.CB0: J2.51 (CB0_A)
A.CB1: J2.53 (CB1_A)
A.CB2: J2.196 (CB2_A)
A.CB3: J2.198 (CB3_A)
A.CB4: J2.58 (CB4_A)
A.CB5: J2.60 (CB5_A)
A.CB6: J2.203 (CB6_A)
A.CB7: J2.205 (CB7_A)
A.CS0_c: J2.64 (CS0_A_N)
A.CS1_c: J2.209 (CS1_A_N)
A.DQ0: J2.7 (DQ0_A)
A.DQ1: J2.9 (DQ1_A)
A.DQ2: J2.152 (DQ2_A)
A.DQ3: J2.154 (DQ3_A)
A.DQ4: J2.14 (DQ4_A)
A.DQ5: J2.16 (DQ5_A)
A.DQ6: J2.159 (DQ6_A)
A.DQ7: J2.161 (DQ7_A)
A.DQ8: J2.18 (DQ8_A)
A.DQ9: J2.20 (DQ9_A)
A.DQ10: J2.163 (DQ10_A)
A.DQ11: J2.165 (DQ11_A)
A.DQ12: J2.25 (DQ12_A)
A.DQ13: J2.27 (DQ13_A)
A.DQ14: J2.170 (DQ14_A)
A.DQ15: J2.172 (DQ15_A)
A.DQ16: J2.29 (DQ16_A)
A.DQ17: J2.31 (DQ17_A)
A.DQ18: J2.174 (DQ18_A)
A.DQ19: J2.176 (DQ19_A)
A.DQ20: J2.36 (DQ20_A)
A.DQ21: J2.38 (DQ21_A)
A.DQ22: J2.181 (DQ22_A)
A.DQ23: J2.183 (DQ23_A)
A.DQ24: J2.40 (DQ24_A)
A.DQ25: J2.42 (DQ25_A)
A.DQ26: J2.185 (DQ26_A)
A.DQ27: J2.187 (DQ27_A)
A.DQ28: J2.47 (DQ28_A)
A.DQ29: J2.49 (DQ29_A)
A.DQ30: J2.192 (DQ30_A)
A.DQ31: J2.194 (DQ31_A)
A.DQS0_N: J2.12 (DQS0_A_C)
A.DQS0_P: J2.11 (DQS0_A_T)
A.DQS1_N: J2.23 (DQS1_A_C)
A.DQS1_P: J2.22 (DQS1_A_T)
A.DQS2_N: J2.34 (DQS2_A_C)
A.DQS2_P: J2.33 (DQS2_A_T)
A.DQS3_N: J2.45 (DQS3_A_C)
A.DQS3_P: J2.44 (DQS3_A_T)
A.DQS4_N: J2.56 (DQS4_A_C)
A.DQS4_P: J2.55 (DQS4_A_T)
A.DQS5_N: J2.156 (DQS5_A_C)
A.DQS5_P: J2.157 (DQS5_A_T)
A.DQS6_N: J2.167 (DQS6_A_C)
A.DQS6_P: J2.168 (DQS6_A_T)
A.DQS7_N: J2.178 (DQS7_A_C)
A.DQS7_P: J2.179 (DQS7_A_T)
A.DQS8_N: J2.189 (DQS8_A_C)
A.DQS8_P: J2.190 (DQS8_A_T)
A.DQS9_N: J2.200 (DQS9_A_C)
A.DQS9_P: J2.201 (DQS9_A_T)
A.PAR: J2.74 (PAR_A)
B.CA0: J2.76 (CA0_B)
B.CA1: J2.78 (CA2_B)
B.CA2: J2.221 (CA1_B)
B.CA3: J2.223 (CA3_B)
B.CA4: J2.80 (CA4_B)
B.CA5: J2.225 (CA5_B)
B.CA6: J2.82 (CA6_B)
B.CB0: J2.96 (CB0_B)
B.CB1: J2.98 (CB1_B)
B.CB2: J2.241 (CB2_B)
B.CB3: J2.243 (CB3_B)
B.CB4: J2.89 (CB4_B)
B.CB5: J2.91 (CB5_B)
B.CB6: J2.234 (CB6_B)
B.CB7: J2.236 (CB7_B)
B.CS0_c: J2.84 (CS0_B_N)
B.CS1_c: J2.229 (CS1_B_N)
B.DQ0: J2.100 (DQ0_B)
B.DQ1: J2.102 (DQ1_B)
B.DQ2: J2.245 (DQ2_B)
B.DQ3: J2.247 (DQ3_B)
B.DQ4: J2.107 (DQ4_B)
B.DQ5: J2.109 (DQ5_B)
B.DQ6: J2.252 (DQ6_B)
B.DQ7: J2.254 (DQ7_B)
B.DQ8: J2.111 (DQ8_B)
B.DQ9: J2.113 (DQ9_B)
B.DQ10: J2.256 (DQ10_B)
B.DQ11: J2.258 (DQ11_B)
B.DQ12: J2.118 (DQ12_B)
B.DQ13: J2.120 (DQ13_B)
B.DQ14: J2.263 (DQ14_B)
B.DQ15: J2.265 (DQ15_B)
B.DQ16: J2.122 (DQ16_B)
B.DQ17: J2.124 (DQ17_B)
B.DQ18: J2.267 (DQ18_B)
B.DQ19: J2.269 (DQ19_B)
B.DQ20: J2.129 (DQ20_B)
B.DQ21: J2.131 (DQ21_B)
B.DQ22: J2.274 (DQ22_B)
B.DQ23: J2.276 (DQ23_B)
B.DQ24: J2.133 (DQ24_B)
B.DQ25: J2.135 (DQ25_B)
B.DQ26: J2.278 (DQ26_B)
B.DQ27: J2.280 (DQ27_B)
B.DQ28: J2.140 (DQ28_B)
B.DQ29: J2.142 (DQ29_B)
B.DQ30: J2.285 (DQ30_B)
B.DQ31: J2.287 (DQ31_B)
B.DQS0_N: J2.105 (DQS0_B_C)
B.DQS0_P: J2.104 (DQS0_B_T)
B.DQS1_N: J2.116 (DQS1_B_C)
B.DQS1_P: J2.115 (DQS1_B_T)
B.DQS2_N: J2.127 (DQS2_B_C)
B.DQS2_P: J2.126 (DQS2_B_T)
B.DQS3_N: J2.138 (DQS3_B_C)
B.DQS3_P: J2.137 (DQS3_B_T)
B.DQS4_N: J2.238 (DQS4_B_C)
B.DQS4_P: J2.239 (DQS4_B_T)
B.DQS5_N: J2.249 (DQS5_B_C)
B.DQS5_P: J2.250 (DQS5_B_T)
B.DQS6_N: J2.260 (DQS6_B_C)
B.DQS6_P: J2.261 (DQS6_B_T)
B.DQS7_N: J2.271 (DQS7_B_C)
B.DQS7_P: J2.272 (DQS7_B_T)
B.DQS8_N: J2.282 (DQS8_B_C)
B.DQS8_P: J2.283 (DQS8_B_T)
B.DQS9_N: J2.94 (DQS9_B_C)
B.DQS9_P: J2.93 (DQS9_B_T)
B.PAR: J2.227 (PAR_B)
CTRL.CK_N: J2.218 (CK_C)
CTRL.CK_P: J2.217 (CK_T)
CTRL.DLBDQ: J2.86 (DLBDQ)
CTRL.DLBDQS: J2.87 (DLBDQS)
CTRL.PWR_GOOD: J2.147 (PCAMP)
CTRL.~ALERT: J2.62 (ALERT_N)
CTRL.~RESET: J2.207 (RESET_N)
DDR.SCL: J2.4 (HSCL)
DDR.SDA: J2.5 (HSDA)
GND: C6.1, C7.1, C8.1, C9.1, C10.1, C127.2, C317.1, C319.1, J2.6 (VSS), J2.8 (VSS), J2.10 (VSS), J2.13 (VSS), J2.15 (VSS), J2.17 (VSS), J2.19 (VSS), J2.21 (VSS), J2.24 (VSS), J2.26 (VSS), J2.28 (VSS), J2.30 (VSS), J2.32 (VSS), J2.35 (VSS), J2.37 (VSS), J2.39 (VSS), J2.41 (VSS), J2.43 (VSS), J2.46 (VSS), J2.48 (VSS), J2.50 (VSS), J2.52 (VSS), J2.54 (VSS), J2.57 (VSS), J2.59 (VSS), J2.61 (VSS), J2.63 (VSS), J2.65 (VSS), J2.67 (VSS), J2.69 (VSS), J2.71 (VSS), J2.73 (VSS), J2.77 (VSS), J2.79 (VSS), J2.81 (VSS), J2.83 (VSS), J2.85 (VSS), J2.88 (VSS), J2.90 (VSS), J2.92 (VSS), J2.95 (VSS), J2.97 (VSS), J2.99 (VSS), J2.101 (VSS), J2.103 (VSS), J2.106 (VSS), J2.108 (VSS), J2.110 (VSS), J2.112 (VSS), J2.114 (VSS), J2.117 (VSS), J2.119 (VSS), J2.121 (VSS), J2.123 (VSS), J2.125 (VSS), J2.128 (VSS), J2.130 (VSS), J2.132 (VSS), J2.134 (VSS), J2.136 (VSS), J2.139 (VSS), J2.141 (VSS), J2.143 (VSS), J2.151 (VSS), J2.153 (VSS), J2.155 (VSS), J2.158 (VSS), J2.160 (VSS), J2.162 (VSS), J2.164 (VSS), J2.166 (VSS), J2.169 (VSS), J2.171 (VSS), J2.173 (VSS), J2.175 (VSS), J2.177 (VSS), J2.180 (VSS), J2.182 (VSS), J2.184 (VSS), J2.186 (VSS), J2.188 (VSS), J2.191 (VSS), J2.193 (VSS), J2.195 (VSS), J2.197 (VSS), J2.199 (VSS), J2.202 (VSS), J2.204 (VSS), J2.206 (VSS), J2.208 (VSS), J2.210 (VSS), J2.212 (VSS), J2.214 (VSS), J2.216 (VSS), J2.219 (VSS), J2.222 (VSS), J2.224 (VSS), J2.226 (VSS), J2.228 (VSS), J2.230 (VSS), J2.233 (VSS), J2.235 (VSS), J2.237 (VSS), J2.240 (VSS), J2.242 (VSS), J2.244 (VSS), J2.246 (VSS), J2.248 (VSS), J2.251 (VSS), J2.253 (VSS), J2.255 (VSS), J2.257 (VSS), J2.259 (VSS), J2.262 (VSS), J2.264 (VSS), J2.266 (VSS), J2.268 (VSS), J2.270 (VSS), J2.273 (VSS), J2.275 (VSS), J2.277 (VSS), J2.279 (VSS), J2.281 (VSS), J2.284 (VSS), J2.286 (VSS), J2.288 (VSS), J2.S1 (SH), J2.S2 (SH), J2.S3 (SH), Q9.2 (S), Q10.2 (S), Q11.2 (S), Q25.2 (S), Q26.2 (S), R26.1, R128.1, R240.1, R242.1, R245.1, R246.1, SW3.1, SW3.2
HOT_SWAP_BUTTON: C127.1, R78.2, SW3.3, SW3.4
HOT_SWAP_GREEN: Q10.1 (G)
HOT_SWAP_RED: Q11.1 (G)
HOT_SWAP_YELLOW: Q9.1 (G)
HSA: J2.148 (HSA), R128.2
unnamed: D20.2 (C_{R}), R63.1
unnamed: D20.3 (C_{G}), R62.1
unnamed: D20.4 (C_{Y}), R61.1
unnamed: D21.1 (C), R242.2
unnamed: D22.1 (C), R246.2
unnamed: Q9.3 (D), R61.2
unnamed: Q10.3 (D), R62.2
unnamed: Q11.3 (D), R63.2
unnamed: Q23.4 (G), Q25.3 (D), R238.1
unnamed: Q26.3 (D), Q27.4 (G), R244.1
VDC: Q23.1 (S), Q23.2 (S), Q23.3 (S), R238.2
VDDQ: C8.2, C9.2, C10.2
VIN_BULK: C6.2, C7.2, D21.2 (A), J2.1 (VIN_BULK), J2.145 (VIN_BULK), J2.146 (VIN_BULK), Q23.5 (D)
VIN_BULK_EN: Q25.1 (G), R240.2
VIN_MGMT: C317.2, C319.2, D22.2 (A), J2.3 (VIN_MGMT), Q27.5 (D)
VIN_MGMT_EN: Q26.1 (G), R245.2
VSS_DET1: J2.75 (VSS_DET), R25.1, R26.2, R27.1
~DDR_PRESENCE: R27.2

Notes on the sheet:
Not populated
Subchannel B
DDR5 RDIMM connector
Power, address command and control
HOT SWAP status LED
HOT SWAP eject button
Default 000
Plane decoupling
~{DDR_PRESENCE}
Serial adress select
Optional RC filter, tr=10ms
Subchannel A
Populated
RDIMM detect
