antmicro/rdimm-ddr5-tester/debug-ftdi.kicad_sch

## KiCad design debug-ftdi.kicad_sch (2026-05-25)

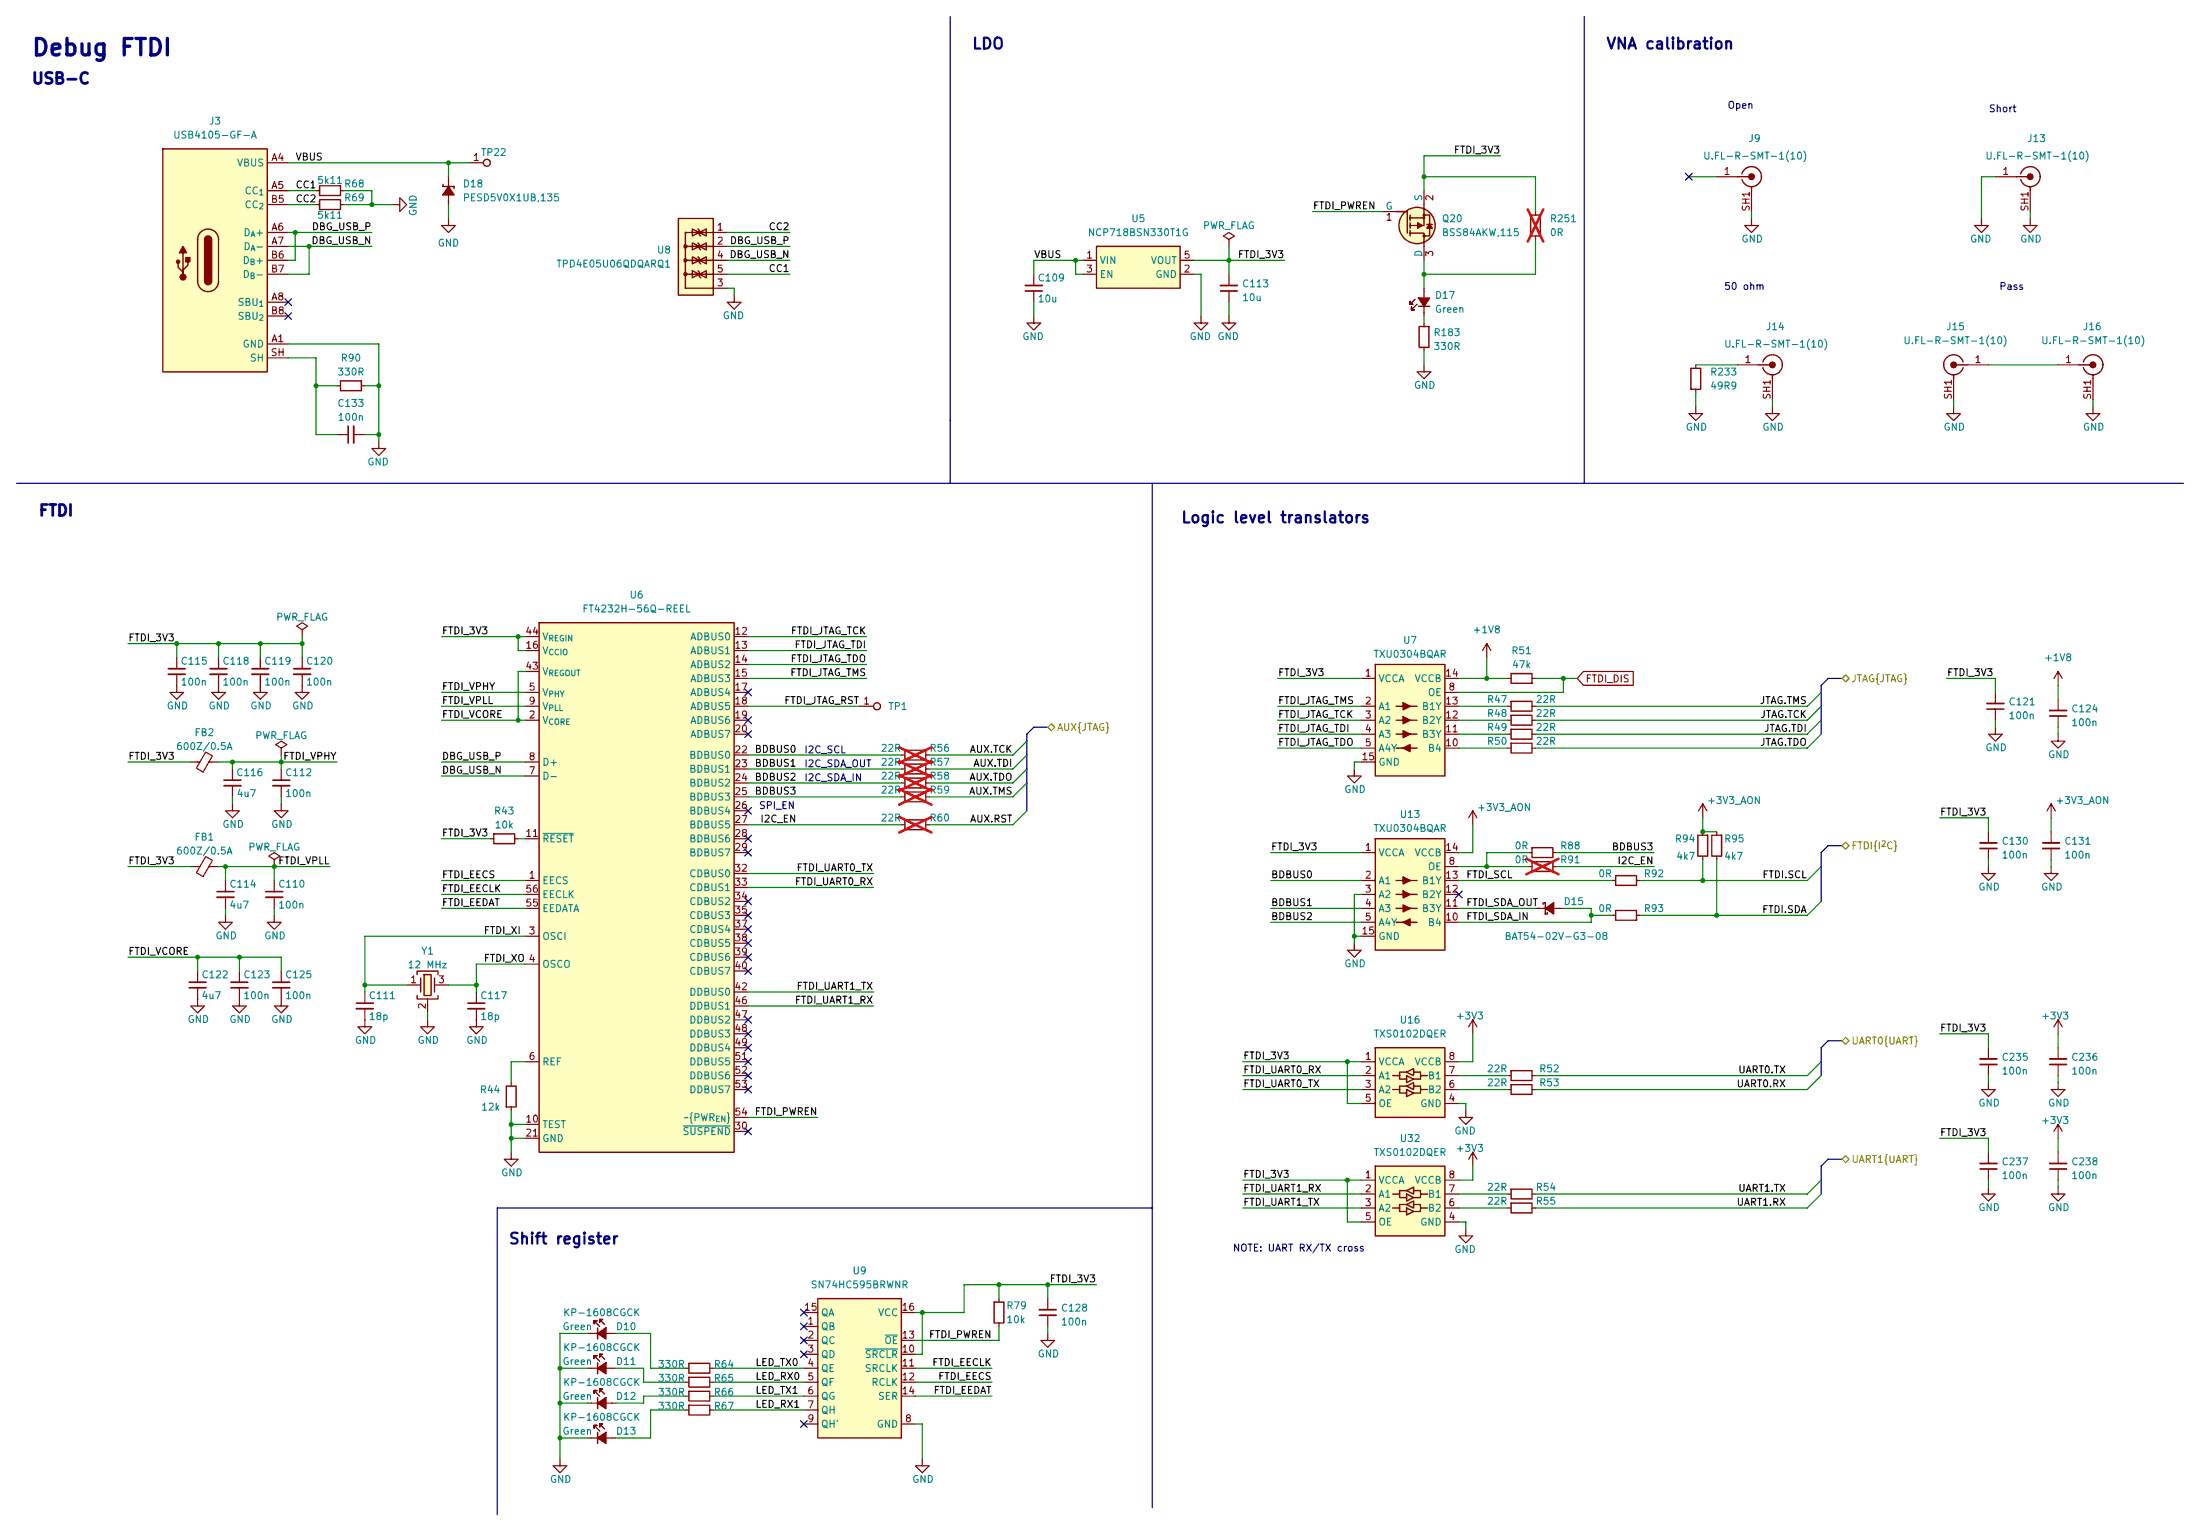
[picture p7: schematic debug-ftdi.kicad_sch]

Parts:
C109: C_10u_25V_0603; C_0603_1608Metric; Voltage 25V; MPN C1608X5R1E106M080AC
C110, C112, C115, C118, C119, C120, C121, C123, C124, C125, C128, C130, C131, C133, C235, C236, C237, C238: C_100n_0402; C_0402_1005Metric; Voltage 50V; MPN GRM155R61H104KE14D
C111, C117: C_18p_0402; C_0402_1005Metric; MPN CL05C180JB51PNC
C113: C_10u_6.3V_0402; C_0402_1005Metric; Voltage 6.3V; MPN GRM155R60J106ME15D
C114, C116, C122: C_4u7_0402; C_0402_1005Metric; MPN GRM155R61A475MEAAD
D10, D11, D12, D13: LED_G_0603_KP-1608CGCK; LED_0603_1608Metric_G; MPN KP-1608CGCK
D15: BAT54-02V-G3-08; SOD-523; MPN BAT54-02V-G3-08
D17: LED_G_0402_VLMTG1500-GS08; LED_0402_1005Metric_G; MPN VLMTG1500-GS08
D18: PESD5V0X1UB; SOD-523; MPN PESD5V0X1UB,135
FB1, FB2: FB_600Z_0.5A_Murata-BLM18AG_0603; FB_0603_1608Metric; MPN BLM18AG601SN1D
J3: USB-C_GCT_USB4105-GF-A; USB-C_Receptacle_GCT_USB4105-GF-A; MPN USB4105-GF-A
J9, J13, J14, J15, J16: U_FL-R-SMT-1; Coax_Conn_U.FL; MPN U.FL-R-SMT-1(10)
Q20: BSS84AKW; SOT-323; MPN BSS84AKW,115
R43, R79: R_10k_0402; R_0402_1005Metric; Tolerance 1%; MPN CR0402-FX-1002GLF
R44: R_12k_0402; R_0402_1005Metric; Tolerance 1%; MPN CR0402-FX-1202GLF
R47, R48, R49, R50, R52, R53, R54, R55: R_22R_0402; R_0402_1005Metric; Tolerance 1%; MPN CR0402-FX-22R0GLF
R51: R_47k_0402; R_0402_1005Metric; Tolerance 1%; MPN CR0402-FX-4702GLF
R56, R57, R58, R59, R60: R_22R_0402; R_0402_1005Metric; Tolerance 1%; MPN CR0402-FX-22R0GLF; not fitted
R64, R65, R66, R67, R90, R183: R_330R_0402; R_0402_1005Metric; Tolerance 1%; MPN CR0402-FX-3300GLF
R68, R69: R_5k11_0402; R_0402_1005Metric; Tolerance 1%; MPN CR0402-FX-5111GLF
R88, R92, R93: R_0R_0402; R_0402_1005Metric; MPN ERJ2GE0R00X
R91, R251: R_0R_0402; R_0402_1005Metric; MPN ERJ2GE0R00X; not fitted
R94, R95: R_4k7_0402; R_0402_1005Metric; Tolerance 1%; MPN CR0402-FX-4701GLF
R233: R_49R9_0402; R_0402_1005Metric; Tolerance 1%; MPN CR0402-FX-49R9GLF
TP1, TP22: TP_1mm_SMD; TP_SMD_1mm
U5: NCP718BSN330T1G; SOT-23-5; MPN NCP718BSN330T1G
U6: FT4232H_VQFN; QFN-56-1EP_8x8mm_P0.5mm; MPN FT4232H-56Q-REEL
U7, U13: TXU0304BQAR; DHVQFN-14-1EP_2.5x3mm; MPN TXU0304BQAR
U8: TPD4E05U06QDQARQ1; USON-10_2.5x1mm_P0.5mm; MPN TPD4E05U06QDQARQ1
U9: SN74HC595B; X1QFN-16-1EP_2.5x2.5mm; MPN SN74HC595BRWNR
U16, U32: TXS0102DQER; X2SON8_1.4x1x0.32mm_P0.35mm; MPN TXS0102DQER
Y1: Resonator_12MHz_ABM8G; Resonator_SMD_Abracon_ABM8G_3.2x2.5mm; MPN ABM8G-12.000MHZ-18-D2Y-T

Connections:
+1V8: C124.2, R51.2, U7.14 (VCCB)
+3V3: C236.2, C238.2, U16.8 (VCCB), U32.8 (VCCB)
+3V3_AON: C131.2, R94.1, R95.1, U13.14 (VCCB)
AUX.RST: R60.2
AUX.TCK: R56.2
AUX.TDI: R57.2
AUX.TDO: R58.2
AUX.TMS: R59.2
BDBUS0: R56.1, U6.22 (BDBUS0), U13.2 (A1)
BDBUS1: R57.1, U6.23 (BDBUS1), U13.4 (A3)
BDBUS2: R58.1, U6.24 (BDBUS2), U13.5 (A4Y)
BDBUS3: R59.1, R88.2, U6.25 (BDBUS3)
CC1: J3.A5 (CC_{1}), R68.2, U8.5, U8.6
CC2: J3.B5 (CC_{2}), R69.1, U8.1, U8.10
DBG_USB_N: J3.A7 (D_{A}-), J3.B7 (D_{B}-), U6.7 (D-), U8.4, U8.7
DBG_USB_P: J3.A6 (D_{A}+), J3.B6 (D_{B}+), U6.8 (D+), U8.2, U8.9
FTDI.SCL: R92.2, R94.2
FTDI.SDA: R93.1, R95.2
FTDI_3V3: C113.2, C115.1, C118.1, C119.1, C120.1, C121.2, C128.2, C130.2, C235.2, C237.2, FB1.1, FB2.1, Q20.2 (S), R43.1, R79.1, R251.2, U5.5 (VOUT), U6.16 (V_{CCIO}), U6.36 (V_{CCIO}), U6.44 (V_{REGIN}), U6.50 (V_{CCIO}), U7.1 (VCCA), U9.10 (~SRCLR), U9.16 (VCC), U13.1 (VCCA), U16.1 (VCCA), U16.5 (OE), U32.1 (VCCA), U32.5 (OE)
FTDI_DIS: R51.1, U7.8 (OE)
FTDI_EECLK: U6.56 (EECLK), U9.11 (SRCLK)
FTDI_EECS: U6.1 (EECS), U9.12 (RCLK)
FTDI_EEDAT: U6.55 (EEDATA), U9.14 (SER)
FTDI_JTAG_RST: TP1.1, U6.18 (ADBUS5)
FTDI_JTAG_TCK: U6.12 (ADBUS0), U7.3 (A2)
FTDI_JTAG_TDI: U6.13 (ADBUS1), U7.4 (A3)
FTDI_JTAG_TDO: U6.14 (ADBUS2), U7.5 (A4Y)
FTDI_JTAG_TMS: U6.15 (ADBUS3), U7.2 (A1)
FTDI_PWREN: Q20.1 (G), R79.2, U6.54 (~PWR_{EN}), U9.13 (~OE)
FTDI_SCL: R92.1, U13.13 (B1Y)
FTDI_SDA_IN: D15.2 (A), R93.2, U13.10 (B4)
FTDI_SDA_OUT: D15.1 (C), U13.11 (B3Y)
FTDI_UART0_RX: U6.33 (CDBUS1), U16.2 (A1)
FTDI_UART0_TX: U6.32 (CDBUS0), U16.3 (A2)
FTDI_UART1_RX: U6.46 (DDBUS1), U32.2 (A1)
FTDI_UART1_TX: U6.42 (DDBUS0), U32.3 (A2)
FTDI_VCORE: C122.1, C123.1, C125.1, U6.2 (V_{CORE}), U6.31 (V_{CORE}), U6.43 (V_{REGOUT})
FTDI_VPHY: C112.1, C116.1, FB2.2, U6.5 (V_{PHY})
FTDI_VPLL: C110.1, C114.1, FB1.2, U6.9 (V_{PLL})
FTDI_XI: C111.1, U6.3 (OSCI), Y1.1
FTDI_XO: C117.1, U6.4 (OSCO), Y1.3
GND: C109.1, C110.2, C111.2, C112.2, C113.1, C114.2, C115.2, C116.2, C117.2, C118.2, C119.2, C120.2, C121.1, C122.2, C123.2, C124.1, C125.2, C128.1, C130.1, C131.1, C133.2, C235.1, C236.1, C237.1, C238.1, D10.1 (C), D11.1 (C), D12.1 (C), D13.1 (C), D18.2 (A), J3.A1 (GND), J3.A12 (GND), J3.B1 (GND), J3.B12 (GND), J9.SH1, J9.SH2, J13.1, J13.SH1, J13.SH2, J14.SH1, J14.SH2, J15.SH1, J15.SH2, J16.SH1, J16.SH2, R44.1, R68.1, R69.2, R90.1, R183.2, R233.1, U5.2 (GND), U6.10 (TEST), U6.21 (GND), U6.41 (GND), U6.45 (GND), U6.57 (GND), U7.7 (GND), U7.15 (GND), U8.3, U8.8, U9.8 (GND), U13.3 (A2), U13.7 (GND), U13.15 (GND), U16.4 (GND), U32.4 (GND), Y1.2 (SH), Y1.4 (SH)
I2C_EN: R60.1, R91.1, U6.27 (BDBUS5)
JTAG.TCK: R48.2
JTAG.TDI: R49.2
JTAG.TDO: R50.2
JTAG.TMS: R47.2
LED_RX0: R65.2, U9.5 (QF)
LED_RX1: R67.2, U9.7 (QH)
LED_TX0: R64.2, U9.4 (QE)
LED_TX1: R66.2, U9.6 (QG)
unnamed: C133.1, J3.SH, R90.2
unnamed: D10.2 (A), R64.1
unnamed: D11.2 (A), R65.1
unnamed: D12.2 (A), R66.1
unnamed: D13.2 (A), R67.1
unnamed: D17.1 (C), R183.1
unnamed: D17.2 (A), Q20.3 (D), R251.1
unnamed: J14.1, R233.2
unnamed: J15.1, J16.1
unnamed: R43.2, U6.11 (~RESET)
unnamed: R44.2, U6.6 (REF)
unnamed: R47.1, U7.13 (B1Y)
unnamed: R48.1, U7.12 (B2Y)
unnamed: R49.1, U7.11 (B3Y)
unnamed: R50.1, U7.10 (B4)
unnamed: R52.1, U16.7 (B1)
unnamed: R53.1, U16.6 (B2)
unnamed: R54.1, U32.7 (B1)
unnamed: R55.1, U32.6 (B2)
unnamed: R88.1, R91.2, U13.8 (OE)
UART0.RX: R53.2
UART0.TX: R52.2
UART1.RX: R55.2
UART1.TX: R54.2
VBUS: C109.2, D18.1 (C), J3.A4 (VBUS), J3.A9 (VBUS), J3.B4 (VBUS), J3.B9 (VBUS), TP22.1, U5.1 (VIN), U5.3 (EN)

Notes on the sheet:
NOTE: UART RX/TX cross
I2C_SCL
Debug FTDI
FTDI
50 ohm
Pass
Open
Short
I2C_SDA_IN
Shift register
VNA calibration
LDO
USB-C
Logic level translators
SPI_EN
I2C_SDA_OUT
