antmicro/rdimm-ddr5-tester/ethernet.kicad_sch

## KiCad design ethernet.kicad_sch (2026-05-21)

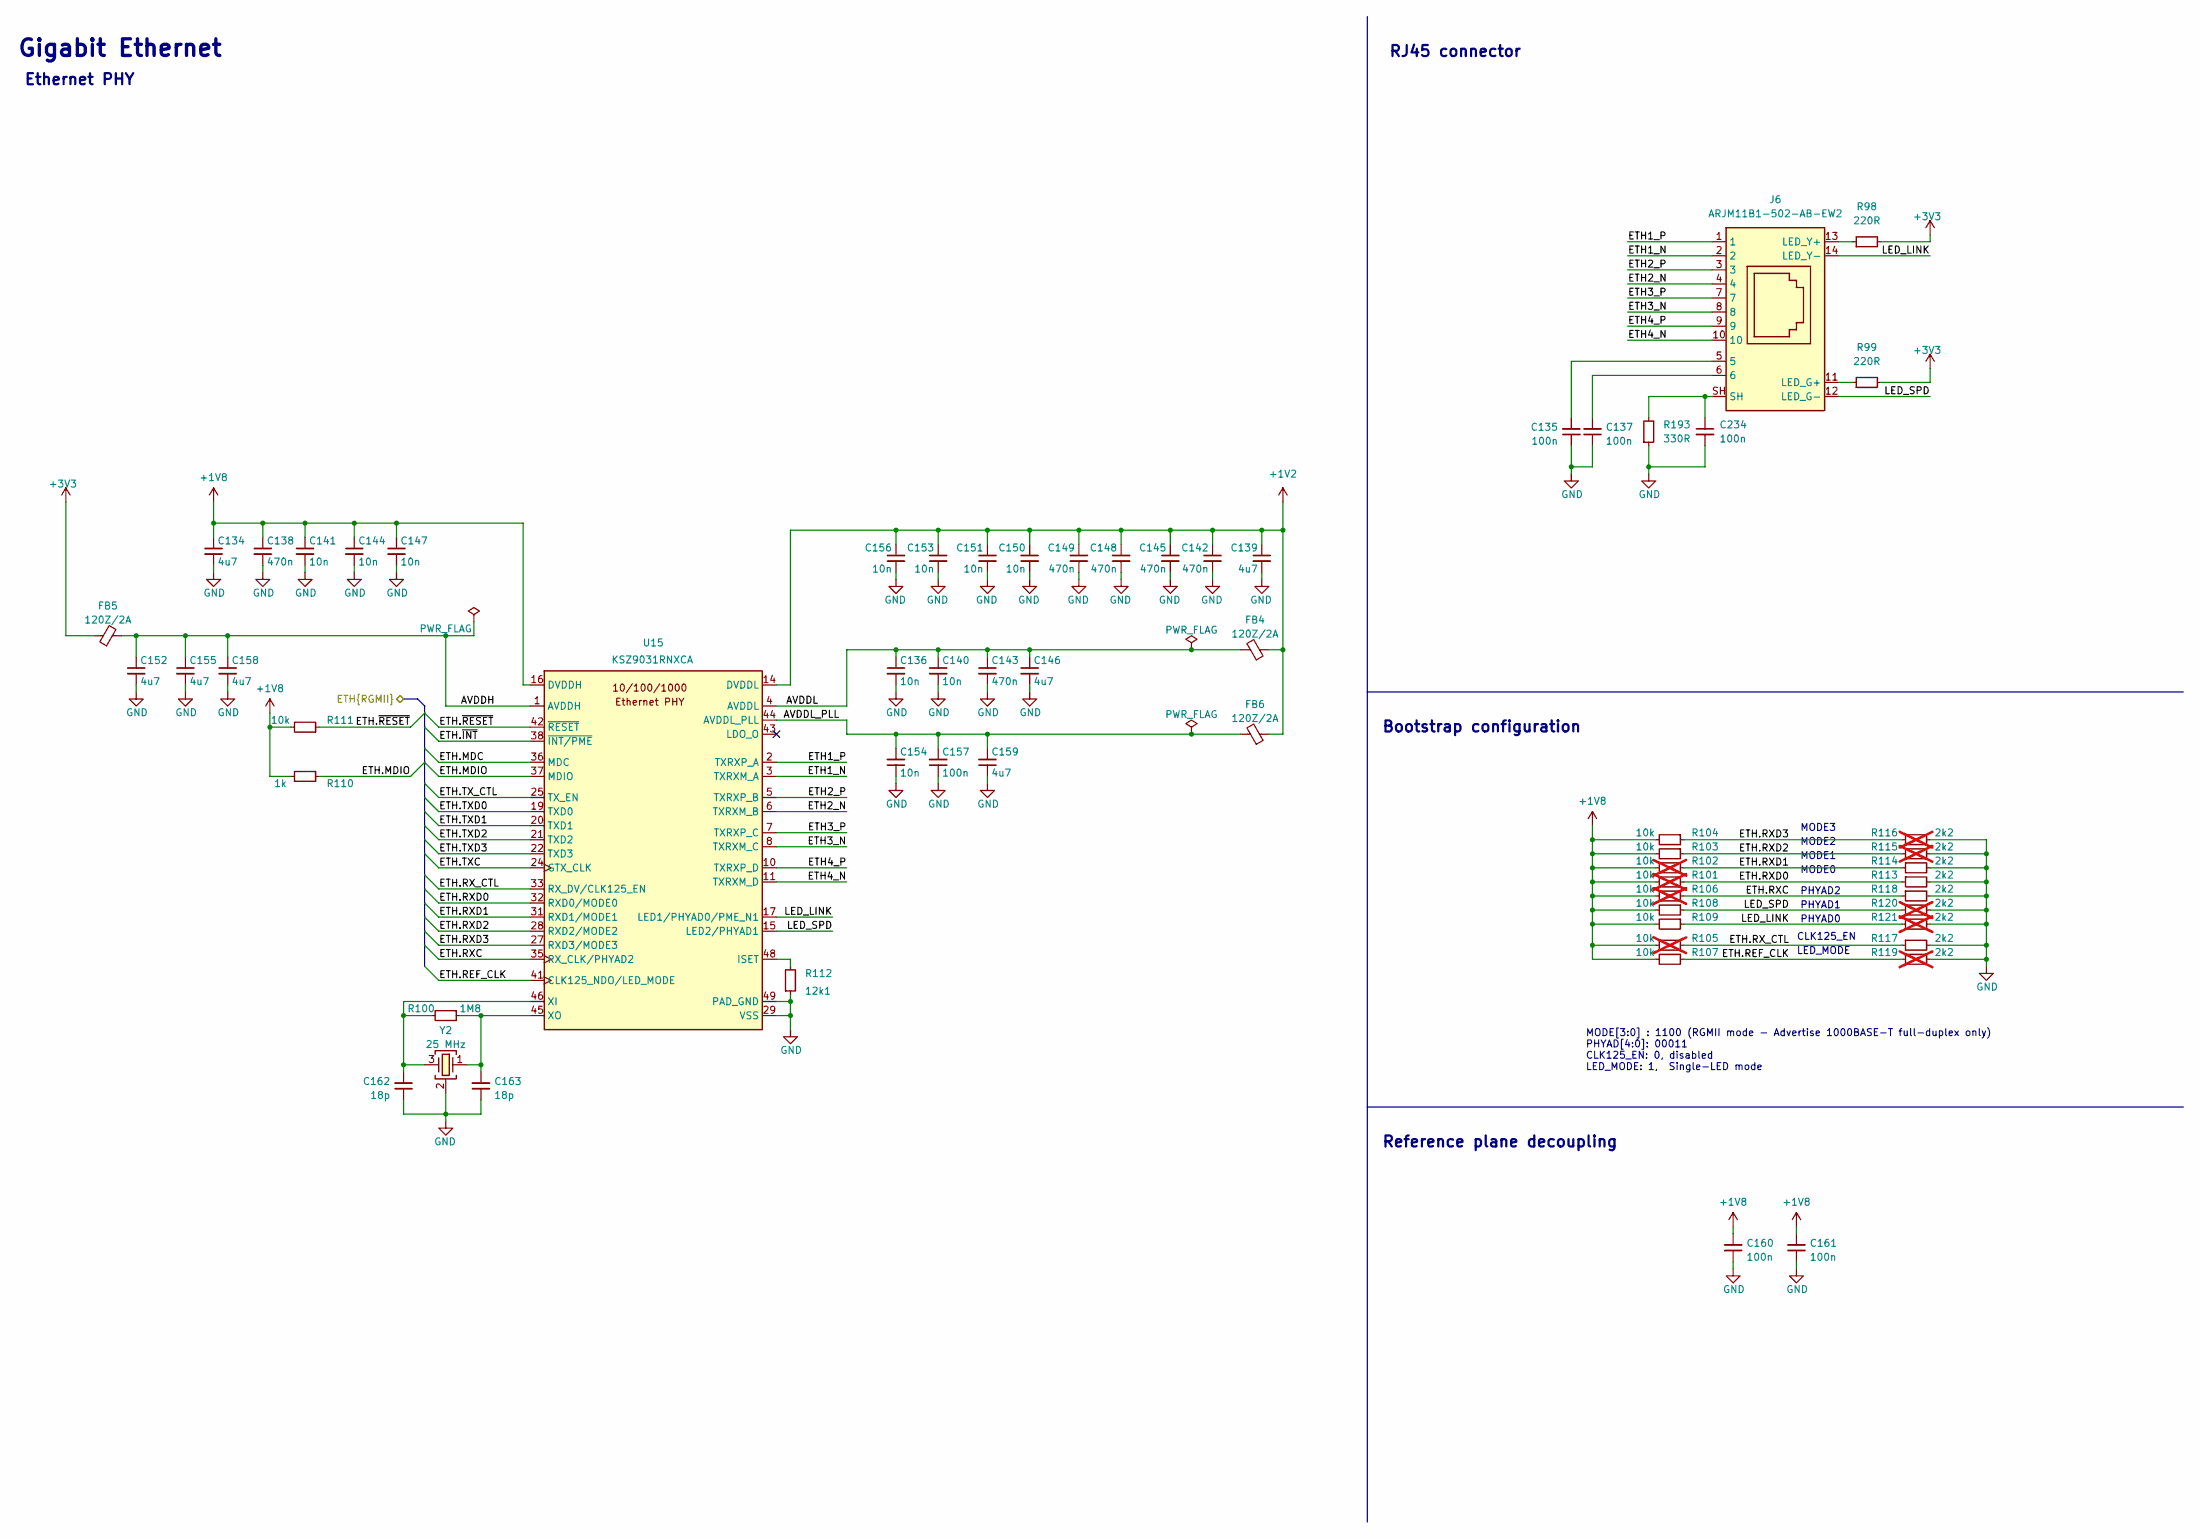
[picture p8: schematic ethernet.kicad_sch]

Parts:
C134, C139, C146, C152, C155, C158, C159: C_4u7_0402; C_0402_1005Metric; MPN GRM155R61A475MEAAD
C135, C137, C157, C160, C161, C234: C_100n_0402; C_0402_1005Metric; Voltage 50V; MPN GRM155R61H104KE14D
C136, C140, C141, C144, C147, C150, C151, C153, C154, C156: C_10n_0402; C_0402_1005Metric; Voltage 50V; MPN GRM155R71H103KA88D
C138, C142, C143, C145, C148, C149: C_470n_0402; C_0402_1005Metric; MPN C1005X5R1E474M050BB
C162, C163: C_18p_0402; C_0402_1005Metric; MPN CL05C180JB51PNC
FB4, FB5, FB6: FB_120Z_2A_Murata-BLM18PG_0603; FB_0603_1608Metric; MPN BLM18PG121SN1D
J6: RJ45_Abracon_ARJM11B1-502-AB-EW2; RJ45_ARJM11B1-502-AB-EW2_Horizontal; MPN ARJM11B1-502-AB-EW2
R98, R99: R_220R_0402; R_0402_1005Metric; Tolerance 1%; MPN CR0402-FX-2200GLF
R100: R_1M8_0402; R_0402_1005Metric; Tolerance 1%; MPN CR0402-FX-1804GLF
R101, R102, R105, R106: R_10k_0402; R_0402_1005Metric; Tolerance 1%; MPN CR0402-FX-1002GLF; not fitted
R103, R104, R107, R108, R109, R111: R_10k_0402; R_0402_1005Metric; Tolerance 1%; MPN CR0402-FX-1002GLF
R110: R_1k_0402; R_0402_1005Metric; Tolerance 1%; MPN CR0402-FX-1001GLF
R112: R_12k1_0402; R_0402_1005Metric; Tolerance 1%; MPN CR0402-FX-1212GLF
R113, R114, R117, R118: R_2k2_0402; R_0402_1005Metric; Tolerance 1%; MPN CR0402-FX-2201GLF
R115, R116, R119, R120, R121: R_2k2_0402; R_0402_1005Metric; Tolerance 1%; MPN CR0402-FX-2201GLF; not fitted
R193: R_330R_0402; R_0402_1005Metric; Tolerance 1%; MPN CR0402-FX-3300GLF
U15: KSZ9031RNXCA; QFN-48-1EP_7x7x0.9mm_P0.5mm_EP3.5x3.5mm; MPN KSZ9031RNXCA
Y2: Resonator_25MHz_ABM8G; Resonator_SMD_Abracon_ABM8G_3.2x2.5mm; MPN ABM8G-25.000MHZ-18-D2Y-T3

Connections:
+1V2: C139.1, C142.1, C145.1, C148.1, C149.1, C150.1, C151.1, C153.1, C156.1, FB4.1, FB6.1, U15.14 (DVDDL), U15.18 (DVDDL), U15.23 (DVDDL), U15.26 (DVDDL), U15.30 (DVDDL), U15.39 (DVDDL)
+1V8: C134.1, C138.1, C141.1, C144.1, C147.1, C160.2, C161.2, R101.2, R102.2, R103.2, R104.2, R105.2, R106.2, R107.2, R108.2, R109.2, R110.2, R111.2, U15.16 (DVDDH), U15.34 (DVDDH), U15.40 (DVDDH)
+3V3: FB5.1, R98.2, R99.2
AVDDH: C152.1, C155.1, C158.1, FB5.2, U15.1 (AVDDH), U15.12 (AVDDH)
AVDDL: C136.1, C140.1, C143.1, C146.1, FB4.2, U15.4 (AVDDL), U15.9 (AVDDL)
AVDDL_PLL: C154.2, C157.2, C159.2, FB6.2, U15.44 (AVDDL_PLL)
ETH1_N: J6.2, U15.3 (TXRXM_A)
ETH1_P: J6.1, U15.2 (TXRXP_A)
ETH2_N: J6.4, U15.6 (TXRXM_B)
ETH2_P: J6.3, U15.5 (TXRXP_B)
ETH3_N: J6.8, U15.8 (TXRXM_C)
ETH3_P: J6.7, U15.7 (TXRXP_C)
ETH4_N: J6.10, U15.11 (TXRXM_D)
ETH4_P: J6.9, U15.10 (TXRXP_D)
ETH.MDC: U15.36 (MDC)
ETH.MDIO: R110.1, U15.37 (MDIO)
ETH.REF_CLK: R107.1, R119.1, U15.41 (CLK125_NDO/LED_MODE)
ETH.RXC: R106.1, R118.1, U15.35 (RX_CLK/PHYAD2)
ETH.RXD0: R101.1, R113.1, U15.32 (RXD0/MODE0)
ETH.RXD1: R102.1, R114.1, U15.31 (RXD1/MODE1)
ETH.RXD2: R103.1, R115.1, U15.28 (RXD2/MODE2)
ETH.RXD3: R104.1, R116.1, U15.27 (RXD3/MODE3)
ETH.RX_CTL: R105.1, R117.1, U15.33 (RX_DV/CLK125_EN)
ETH.TXC: U15.24 (GTX_CLK)
ETH.TXD0: U15.19 (TXD0)
ETH.TXD1: U15.20 (TXD1)
ETH.TXD2: U15.21 (TXD2)
ETH.TXD3: U15.22 (TXD3)
ETH.TX_CTL: U15.25 (TX_EN)
ETH.~INT: U15.38 (~INT/PME)
ETH.~RESET: R111.1, U15.42 (~RESET)
GND: C134.2, C135.1, C136.2, C137.1, C138.2, C139.2, C140.2, C141.2, C142.2, C143.2, C144.2, C145.2, C146.2, C147.2, C148.2, C149.2, C150.2, C151.2, C152.2, C153.2, C154.1, C155.2, C156.2, C157.1, C158.2, C159.1, C160.1, C161.1, C162.1, C163.1, C234.2, R112.1, R113.2, R114.2, R115.2, R116.2, R117.2, R118.2, R119.2, R120.2, R121.2, R193.1, U15.29 (VSS), U15.49 (PAD_GND), Y2.2 (SH), Y2.4 (SH)
LED_LINK: J6.14 (LED_Y-), R109.1, R121.1, U15.17 (LED1/PHYAD0/PME_N1)
LED_SPD: J6.12 (LED_G-), R108.1, R120.1, U15.15 (LED2/PHYAD1)
unnamed: C135.2, J6.5
unnamed: C137.2, J6.6
unnamed: C162.2, R100.2, U15.46 (XI), Y2.3
unnamed: C163.2, R100.1, U15.45 (XO), Y2.1
unnamed: C234.1, J6.SH, R193.2
unnamed: J6.11 (LED_G+), R99.1
unnamed: J6.13 (LED_Y+), R98.1
unnamed: R112.2, U15.48 (ISET)

Notes on the sheet:
Bootstrap configuration
PHYAD2
CLK125_EN
MODE2
Ethernet PHY
Reference plane decoupling
PHYAD1
MODE[3:0] : 1100 (RGMII mode - Advertise 1000BASE-T full-duplex only) PHYAD[4:0]: 00011 CLK125_EN: 0, disabled LED_MODE: 1, Single-LED mode
RJ45 connector
Gigabit Ethernet
MODE3
MODE1
MODE0
LED_MODE
PHYAD0
