antmicro/rdimm-ddr5-tester/fpga-config.kicad_sch

## KiCad design fpga-config.kicad_sch (2026-05-21)

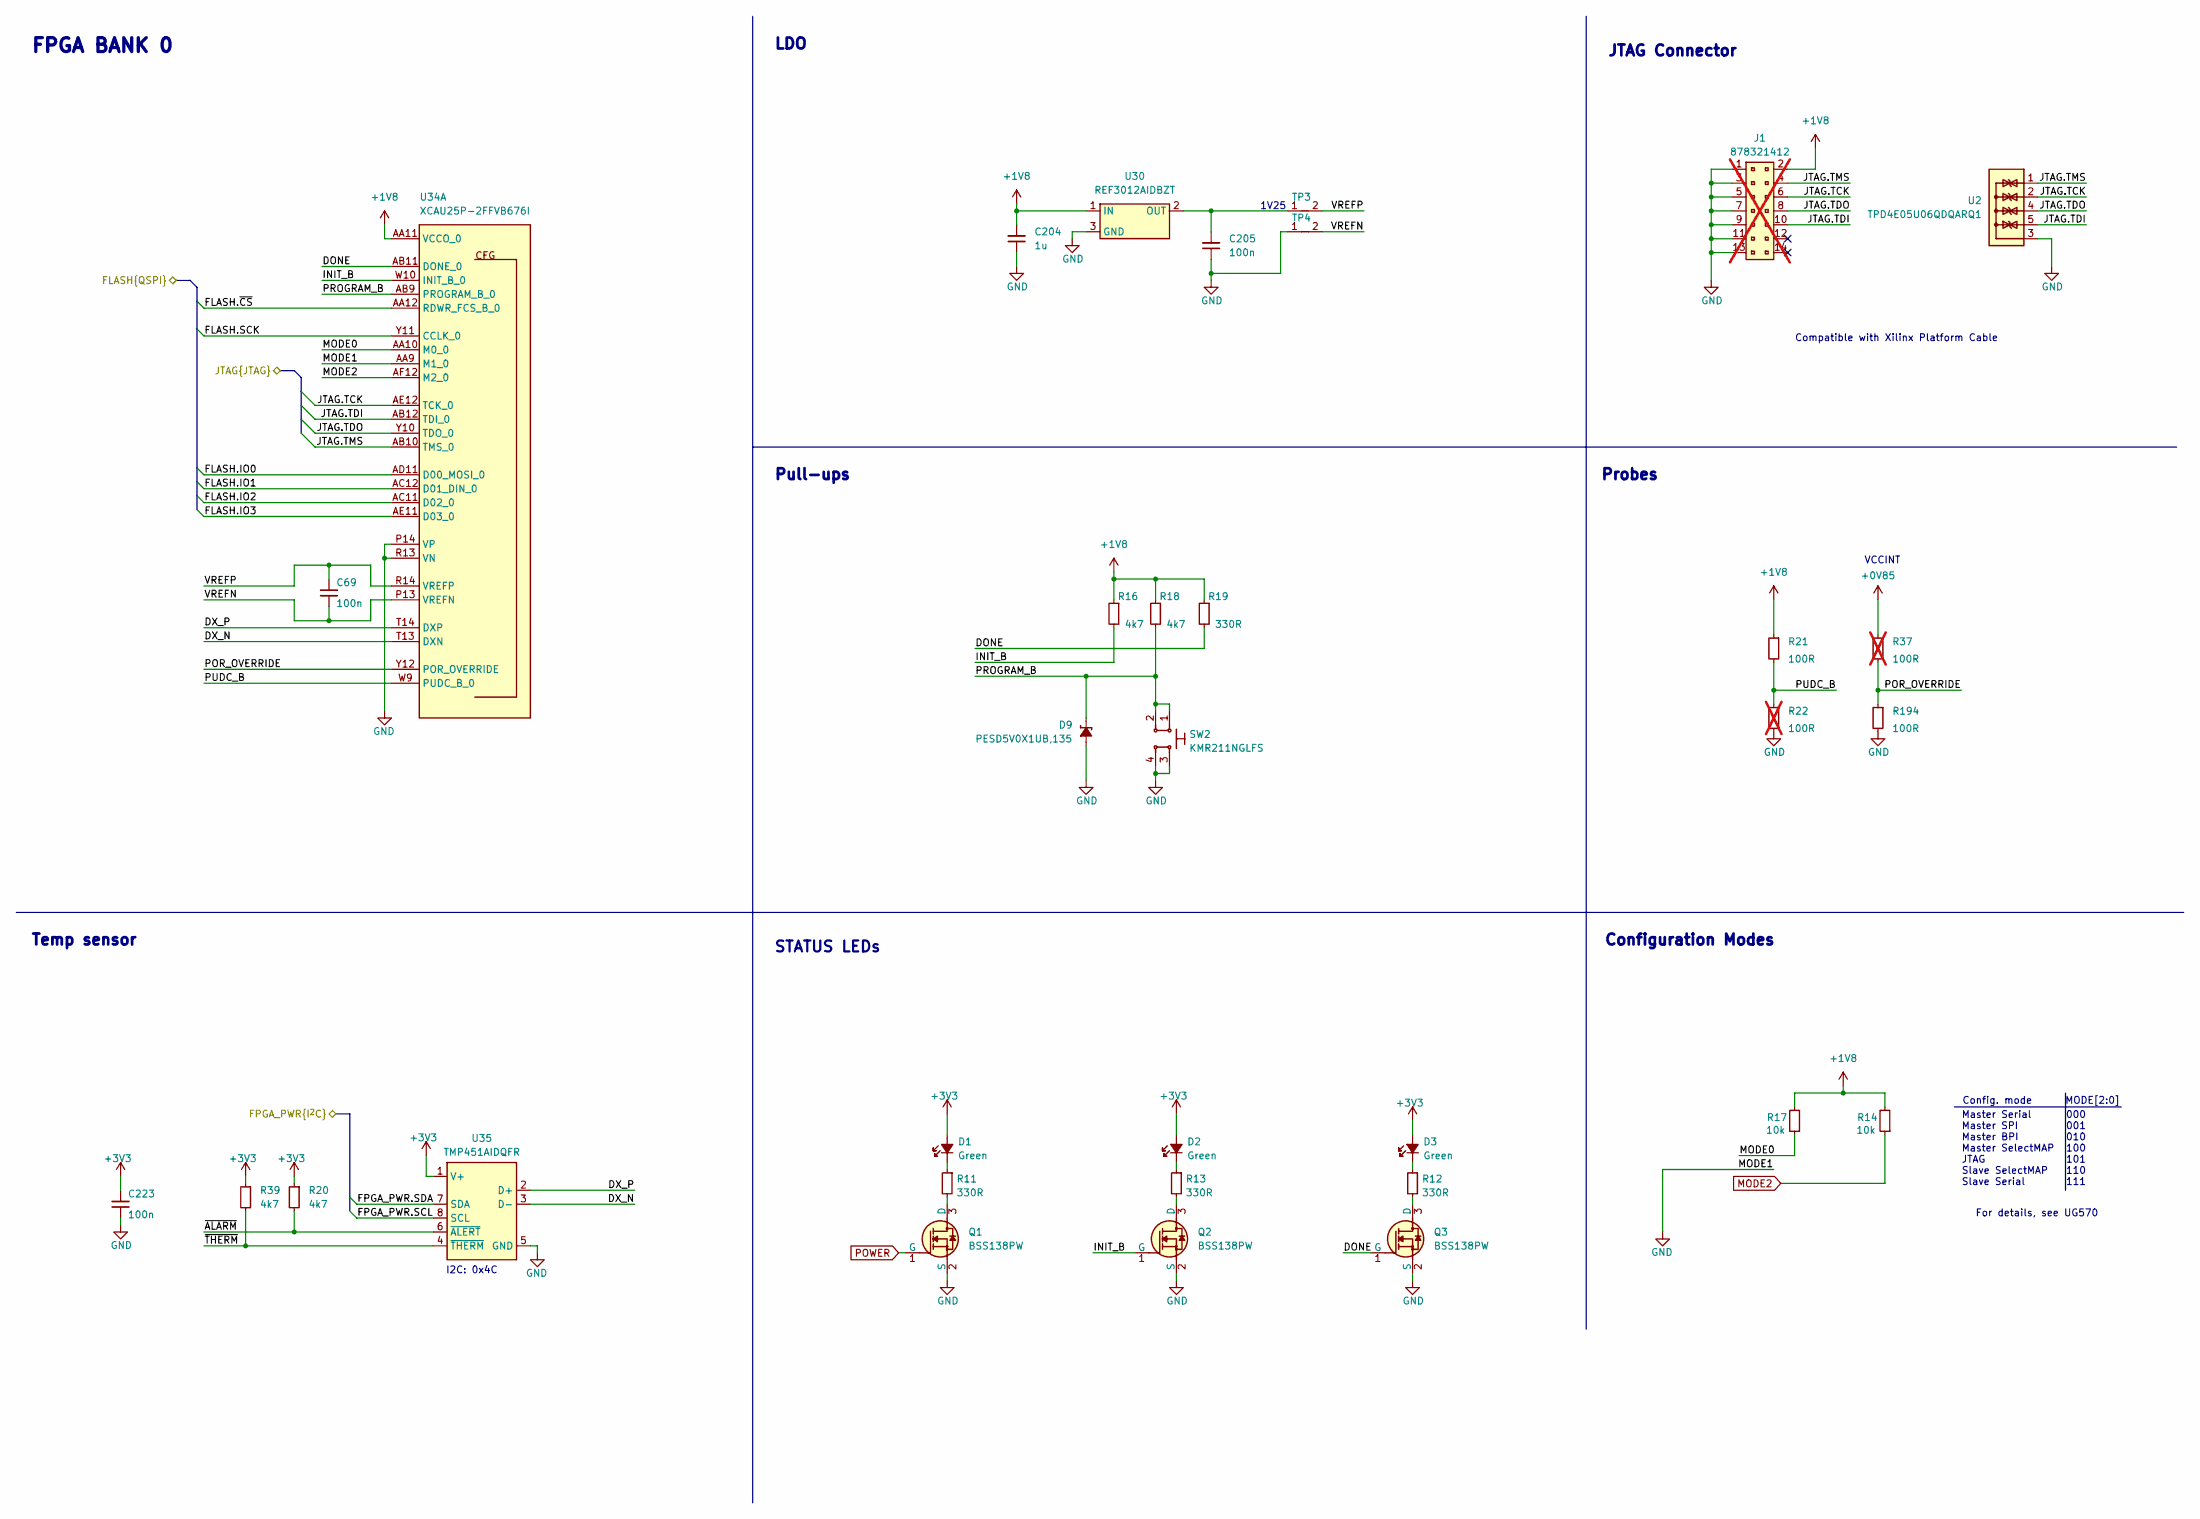
[picture p9: schematic fpga-config.kicad_sch]

Parts:
C69: C_100n_0402; C_0402_1005Metric_EIA; Voltage 50V; MPN GRM155R61H104KE14D
C204: C_1u_0402; C_0402_1005Metric; MPN C1005X6S1A105K050BC
C205, C223: C_100n_0402; C_0402_1005Metric; Voltage 50V; MPN GRM155R61H104KE14D
D1, D2, D3: LED_G_0402_VLMTG1500-GS08; LED_0402_1005Metric_G; MPN VLMTG1500-GS08
D9: PESD5V0X1UB; SOD-523; MPN PESD5V0X1UB,135
J1: PinHeader_2x7_P2mm_SMD_Shrouded_no-locator; MPN 878321412; not fitted
Q1, Q2, Q3: BSS138PW; SC70-3; MPN BSS138PW
R11, R12, R13, R19: R_330R_0402; R_0402_1005Metric; Tolerance 1%; MPN CR0402-FX-3300GLF
R14, R17: R_10k_0402; R_0402_1005Metric_EIA; Tolerance 1%; MPN CR0402-FX-1002GLF
R16, R20, R39: R_4k7_0402; R_0402_1005Metric; Tolerance 1%; MPN CR0402-FX-4701GLF
R18: R_4k7_0402; R_0402_1005Metric_EIA; Tolerance 1%; MPN CR0402-FX-4701GLF
R21, R194: R_100R_0402; R_0402_1005Metric_EIA; Tolerance 1%; MPN CR0402-FX-1000GLF
R22, R37: R_100R_0402; R_0402_1005Metric_EIA; Tolerance 1%; MPN CR0402-FX-1000GLF; not fitted
SW2: SW_KMR211NGLFS_SMD; MPN KMR211NGLFS
TP3, TP4: Net-Tie_P0.127mm; NetTie-2_SMD_Pad0.127mm
U2: TPD4E05U06QDQARQ1; USON-10_2.5x1mm_P0.5mm; MPN TPD4E05U06QDQARQ1
U30: REF3012AIDBZT; SOT-23-3; MPN REF3012AIDBZT
U34: XCAU25P-2FFVB676I; BGA-676_27x27mm_Layout26x26_P1x1mm_FFVB676; MPN XCAU25P-2FFVB676I
U35: TMP451AIDQFR; WSON-8_2x2mm; MPN TMP451AIDQFR

Connections:
+0V85: R37.1
+1V8: C204.2, J1.2, R14.2, R16.1, R17.2, R18.1, R19.1, R21.1, U30.1 (IN), U34.AA11 (VCCO_0), U34.AD12 (VCCO_0)
+3V3: C223.2, D1.2 (A), D2.2 (A), D3.2 (A), R20.1, R39.1, U35.1 (V+)
DONE: Q3.1 (G), R19.2, U34.AB11 (DONE_0)
DX_N: U34.T13 (DXN), U35.3 (D-)
DX_P: U34.T14 (DXP), U35.2 (D+)
FLASH.IO0: U34.AD11 (D00_MOSI_0)
FLASH.IO1: U34.AC12 (D01_DIN_0)
FLASH.IO2: U34.AC11 (D02_0)
FLASH.IO3: U34.AE11 (D03_0)
FLASH.SCK: U34.Y11 (CCLK_0)
FLASH.~CS: U34.AA12 (RDWR_FCS_B_0)
FPGA_PWR.SCL: U35.8 (SCL)
FPGA_PWR.SDA: U35.7 (SDA)
GND: C204.1, C205.1, C223.1, D9.2 (A), J1.1, J1.3, J1.5, J1.7, J1.9, J1.11, J1.13, Q1.2 (S), Q2.2 (S), Q3.2 (S), R22.2, R194.2, SW2.3, SW2.4, TP4.1, U2.3, U2.8, U30.3 (GND), U34.AA9 (M1_0), U34.P14 (VP), U34.R13 (VN), U35.5 (GND)
INIT_B: Q2.1 (G), R16.2, U34.W10 (INIT_B_0)
JTAG.TCK: J1.6, U2.2, U2.9, U34.AE12 (TCK_0)
JTAG.TDI: J1.10, U2.5, U2.6, U34.AB12 (TDI_0)
JTAG.TDO: J1.8, U2.4, U2.7, U34.Y10 (TDO_0)
JTAG.TMS: J1.4, U2.1, U2.10, U34.AB10 (TMS_0)
MODE0: R17.1, U34.AA10 (M0_0)
MODE2: R14.1, U34.AF12 (M2_0)
unnamed: C205.2, TP3.1, U30.2 (OUT)
unnamed: D1.1 (C), R11.1
unnamed: D2.1 (C), R13.1
unnamed: D3.1 (C), R12.1
unnamed: Q1.3 (D), R11.2
unnamed: Q2.3 (D), R13.2
unnamed: Q3.3 (D), R12.2
POR_OVERRIDE: R37.2, R194.1, U34.Y12 (POR_OVERRIDE)
POWER: Q1.1 (G)
PROGRAM_B: D9.1 (C), R18.2, SW2.1, SW2.2, U34.AB9 (PROGRAM_B_0)
PUDC_B: R21.2, R22.1, U34.W9 (PUDC_B_0)
VREFN: C69.1, TP4.2, U34.P13 (VREFN)
VREFP: C69.2, TP3.2, U34.R14 (VREFP)
~ALARM: R20.2, U35.6 (~ALERT)
~THERM: R39.2, U35.4 (~THERM)

Notes on the sheet:
Configuration Modes
LDO
1V25
Pull-ups
JTAG Connector
000 001 010 100 101 110 111
Probes
FPGA BANK 0
MODE[2:0]
I2C: 0x4C
Temp sensor
Config. mode
Compatible with Xilinx Platform Cable
Master Serial Master SPI Master BPI Master SelectMAP JTAG Slave SelectMAP Slave Serial
For details, see UG570
VCCINT
STATUS LEDs
