antmicro/rdimm-ddr5-tester/fpga-hd-banks.kicad_sch

## KiCad design fpga-hd-banks.kicad_sch (2026-05-21)

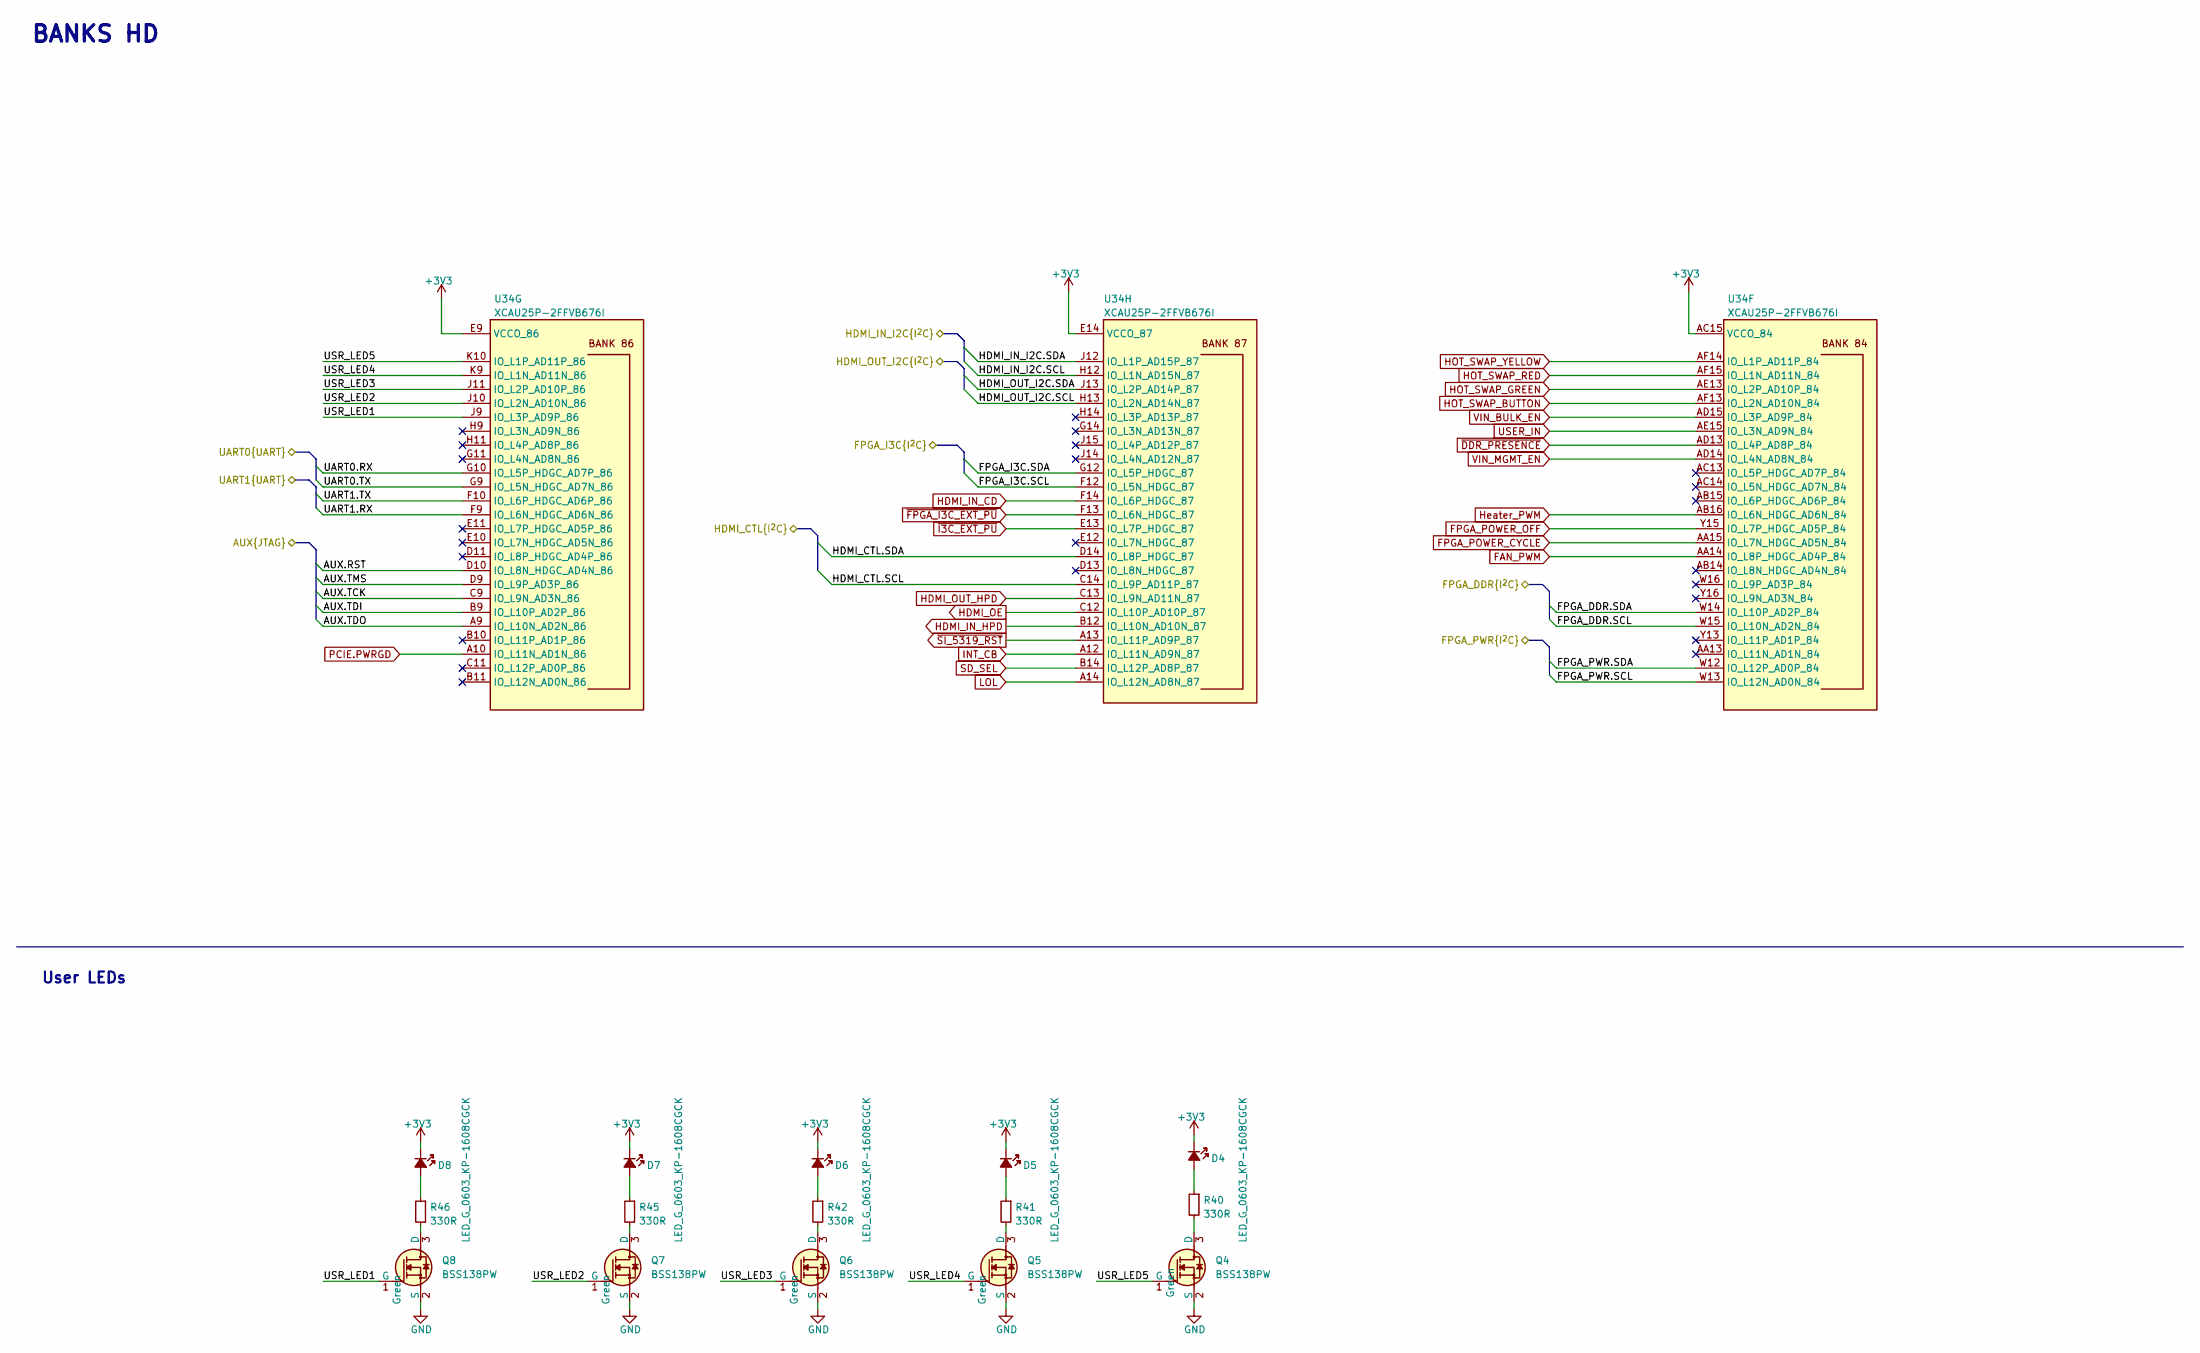
[picture p10: schematic fpga-hd-banks.kicad_sch]

Parts:
D4, D5, D6, D7, D8: LED_G_0603_KP-1608CGCK; LED_0603_1608Metric_G; MPN KP-1608CGCK
Q4, Q5, Q6, Q7, Q8: BSS138PW; SC70-3; MPN BSS138PW
R40, R41, R42, R45, R46: R_330R_0402; R_0402_1005Metric; Tolerance 1%; MPN CR0402-FX-3300GLF
U34: XCAU25P-2FFVB676I; BGA-676_27x27mm_Layout26x26_P1x1mm_FFVB676; MPN XCAU25P-2FFVB676I

Connections:
+3V3: D4.1 (C), D5.1 (C), D6.1 (C), D7.1 (C), D8.1 (C), U34.AC15 (VCCO_84), U34.E9 (VCCO_86), U34.E14 (VCCO_87), U34.H10 (VCCO_86), U34.H15 (VCCO_87), U34.Y14 (VCCO_84)
AUX.RST: U34.D10 (IO_L8N_HDGC_AD4N_86)
AUX.TCK: U34.C9 (IO_L9N_AD3N_86)
AUX.TDI: U34.B9 (IO_L10P_AD2P_86)
AUX.TDO: U34.A9 (IO_L10N_AD2N_86)
AUX.TMS: U34.D9 (IO_L9P_AD3P_86)
FAN_PWM: U34.AA14 (IO_L8P_HDGC_AD4P_84)
FPGA_DDR.SCL: U34.W15 (IO_L10N_AD2N_84)
FPGA_DDR.SDA: U34.W14 (IO_L10P_AD2P_84)
FPGA_I3C.SCL: U34.F12 (IO_L5N_HDGC_87)
FPGA_I3C.SDA: U34.G12 (IO_L5P_HDGC_87)
FPGA_POWER_CYCLE: U34.AA15 (IO_L7N_HDGC_AD5N_84)
FPGA_POWER_OFF: U34.Y15 (IO_L7P_HDGC_AD5P_84)
FPGA_PWR.SCL: U34.W13 (IO_L12N_AD0N_84)
FPGA_PWR.SDA: U34.W12 (IO_L12P_AD0P_84)
GND: Q4.2 (S), Q5.2 (S), Q6.2 (S), Q7.2 (S), Q8.2 (S)
HDMI_CTL.SCL: U34.C14 (IO_L9P_AD11P_87)
HDMI_CTL.SDA: U34.D14 (IO_L8P_HDGC_87)
HDMI_IN_CD: U34.F14 (IO_L6P_HDGC_87)
HDMI_IN_HPD: U34.B12 (IO_L10N_AD10N_87)
HDMI_IN_I2C.SCL: U34.H12 (IO_L1N_AD15N_87)
HDMI_IN_I2C.SDA: U34.J12 (IO_L1P_AD15P_87)
HDMI_OE: U34.C12 (IO_L10P_AD10P_87)
HDMI_OUT_HPD: U34.C13 (IO_L9N_AD11N_87)
HDMI_OUT_I2C.SCL: U34.H13 (IO_L2N_AD14N_87)
HDMI_OUT_I2C.SDA: U34.J13 (IO_L2P_AD14P_87)
HOT_SWAP_BUTTON: U34.AF13 (IO_L2N_AD10N_84)
HOT_SWAP_GREEN: U34.AE13 (IO_L2P_AD10P_84)
HOT_SWAP_RED: U34.AF15 (IO_L1N_AD11N_84)
HOT_SWAP_YELLOW: U34.AF14 (IO_L1P_AD11P_84)
Heater_PWM: U34.AB16 (IO_L6N_HDGC_AD6N_84)
INT_CB: U34.A12 (IO_L11N_AD9N_87)
LOL: U34.A14 (IO_L12N_AD8N_87)
unnamed: D4.2 (A), R40.1
unnamed: D5.2 (A), R41.1
unnamed: D6.2 (A), R42.1
unnamed: D7.2 (A), R45.1
unnamed: D8.2 (A), R46.1
unnamed: Q4.3 (D), R40.2
unnamed: Q5.3 (D), R41.2
unnamed: Q6.3 (D), R42.2
unnamed: Q7.3 (D), R45.2
unnamed: Q8.3 (D), R46.2
PCIE.PWRGD: U34.A10 (IO_L11N_AD1N_86)
SD_SEL: U34.B14 (IO_L12P_AD8P_87)
UART0.RX: U34.G10 (IO_L5P_HDGC_AD7P_86)
UART0.TX: U34.G9 (IO_L5N_HDGC_AD7N_86)
UART1.RX: U34.F9 (IO_L6N_HDGC_AD6N_86)
UART1.TX: U34.F10 (IO_L6P_HDGC_AD6P_86)
USER_IN: U34.AE15 (IO_L3N_AD9N_84)
USR_LED1: Q8.1 (G), U34.J9 (IO_L3P_AD9P_86)
USR_LED2: Q7.1 (G), U34.J10 (IO_L2N_AD10N_86)
USR_LED3: Q6.1 (G), U34.J11 (IO_L2P_AD10P_86)
USR_LED4: Q5.1 (G), U34.K9 (IO_L1N_AD11N_86)
USR_LED5: Q4.1 (G), U34.K10 (IO_L1P_AD11P_86)
VIN_BULK_EN: U34.AD15 (IO_L3P_AD9P_84)
VIN_MGMT_EN: U34.AD14 (IO_L4N_AD8N_84)
~DDR_PRESENCE: U34.AD13 (IO_L4P_AD8P_84)
~FPGA_I3C_EXT_PU: U34.F13 (IO_L6N_HDGC_87)
~I3C_EXT_PU: U34.E13 (IO_L7P_HDGC_87)
~SI_5319_RST: U34.A13 (IO_L11P_AD9P_87)

Notes on the sheet:
User LEDs
BANKS HD
