antmicro/rdimm-ddr5-tester/fpga-hp-banks.kicad_sch

## KiCad design fpga-hp-banks.kicad_sch (2026-05-25)

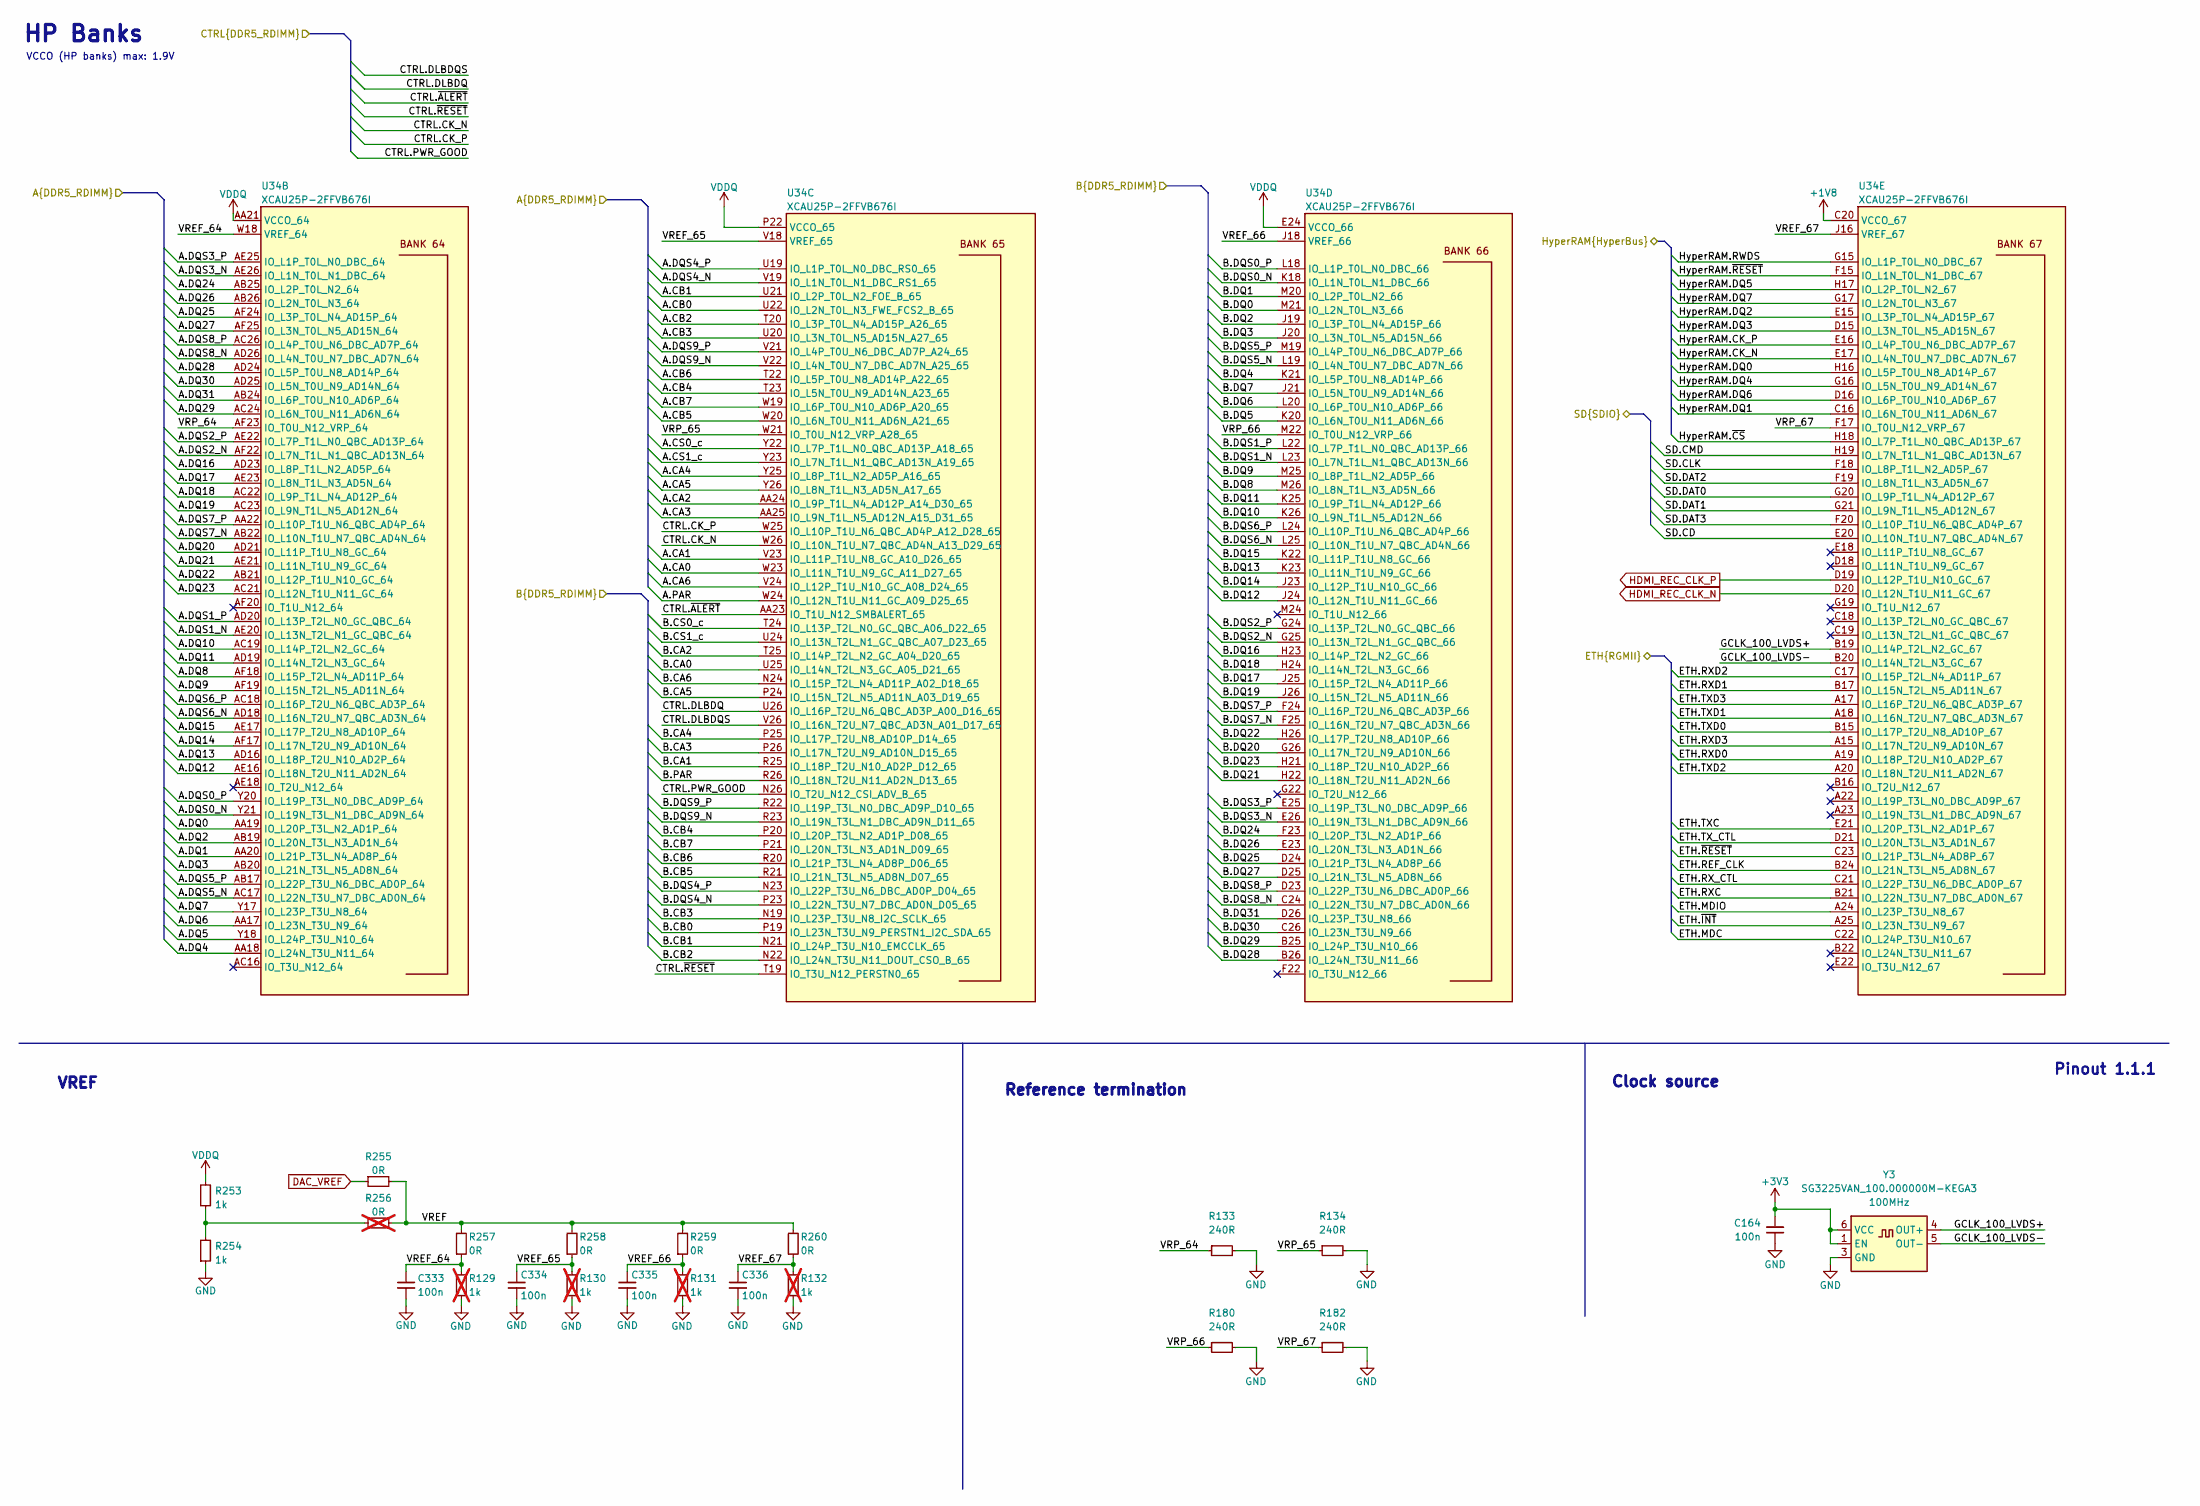
[picture p11: schematic fpga-hp-banks.kicad_sch]

Parts:
C164, C333, C334, C335, C336: C_100n_0402; C_0402_1005Metric; Voltage 50V; MPN GRM155R61H104KE14D
R129, R130, R131, R132: R_1k_0402; R_0402_1005Metric_EIA; Tolerance 1%; MPN CR0402-FX-1001GLF; not fitted
R133, R134, R180, R182: R_240R_0402; R_0402_1005Metric_EIA; Tolerance 1%; MPN CR0402-FX-2400GLF
R253, R254: R_1k_0402; R_0402_1005Metric; Tolerance 1%; MPN CR0402-FX-1001GLF
R255, R257, R258, R259, R260: R_0R_0402; R_0402_1005Metric; MPN ERJ2GE0R00X
R256: R_0R_0402; R_0402_1005Metric; MPN ERJ2GE0R00X; not fitted
U34: XCAU25P-2FFVB676I; BGA-676_27x27mm_Layout26x26_P1x1mm_FFVB676; MPN XCAU25P-2FFVB676I
Y3: Oscillator_100MHz_SG3225VAN; Oscillator_SMD_Epson_SG3225EEN_3.2x2.5x1.2mm; MPN SG3225VAN_100.000000M-KEGA3

Connections:
+1V8: U34.C20 (VCCO_67), U34.D17 (VCCO_67), U34.G18 (VCCO_67)
+3V3: C164.2, Y3.1 (EN), Y3.6 (VCC)
A.CA0: U34.W23 (IO_L11N_T1U_N9_GC_A11_D27_65)
A.CA1: U34.V23 (IO_L11P_T1U_N8_GC_A10_D26_65)
A.CA2: U34.AA24 (IO_L9P_T1L_N4_AD12P_A14_D30_65)
A.CA3: U34.AA25 (IO_L9N_T1L_N5_AD12N_A15_D31_65)
A.CA4: U34.Y25 (IO_L8P_T1L_N2_AD5P_A16_65)
A.CA5: U34.Y26 (IO_L8N_T1L_N3_AD5N_A17_65)
A.CA6: U34.V24 (IO_L12P_T1U_N10_GC_A08_D24_65)
A.CB0: U34.U22 (IO_L2N_T0L_N3_FWE_FCS2_B_65)
A.CB1: U34.U21 (IO_L2P_T0L_N2_FOE_B_65)
A.CB2: U34.T20 (IO_L3P_T0L_N4_AD15P_A26_65)
A.CB3: U34.U20 (IO_L3N_T0L_N5_AD15N_A27_65)
A.CB4: U34.T23 (IO_L5N_T0U_N9_AD14N_A23_65)
A.CB5: U34.W20 (IO_L6N_T0U_N11_AD6N_A21_65)
A.CB6: U34.T22 (IO_L5P_T0U_N8_AD14P_A22_65)
A.CB7: U34.W19 (IO_L6P_T0U_N10_AD6P_A20_65)
A.CS0_c: U34.Y22 (IO_L7P_T1L_N0_QBC_AD13P_A18_65)
A.CS1_c: U34.Y23 (IO_L7N_T1L_N1_QBC_AD13N_A19_65)
A.DQ0: U34.AA19 (IO_L20P_T3L_N2_AD1P_64)
A.DQ1: U34.AA20 (IO_L21P_T3L_N4_AD8P_64)
A.DQ2: U34.AB19 (IO_L20N_T3L_N3_AD1N_64)
A.DQ3: U34.AB20 (IO_L21N_T3L_N5_AD8N_64)
A.DQ4: U34.AA18 (IO_L24N_T3U_N11_64)
A.DQ5: U34.Y18 (IO_L24P_T3U_N10_64)
A.DQ6: U34.AA17 (IO_L23N_T3U_N9_64)
A.DQ7: U34.Y17 (IO_L23P_T3U_N8_64)
A.DQ8: U34.AF18 (IO_L15P_T2L_N4_AD11P_64)
A.DQ9: U34.AF19 (IO_L15N_T2L_N5_AD11N_64)
A.DQ10: U34.AC19 (IO_L14P_T2L_N2_GC_64)
A.DQ11: U34.AD19 (IO_L14N_T2L_N3_GC_64)
A.DQ12: U34.AE16 (IO_L18N_T2U_N11_AD2N_64)
A.DQ13: U34.AD16 (IO_L18P_T2U_N10_AD2P_64)
A.DQ14: U34.AF17 (IO_L17N_T2U_N9_AD10N_64)
A.DQ15: U34.AE17 (IO_L17P_T2U_N8_AD10P_64)
A.DQ16: U34.AD23 (IO_L8P_T1L_N2_AD5P_64)
A.DQ17: U34.AE23 (IO_L8N_T1L_N3_AD5N_64)
A.DQ18: U34.AC22 (IO_L9P_T1L_N4_AD12P_64)
A.DQ19: U34.AC23 (IO_L9N_T1L_N5_AD12N_64)
A.DQ20: U34.AD21 (IO_L11P_T1U_N8_GC_64)
A.DQ21: U34.AE21 (IO_L11N_T1U_N9_GC_64)
A.DQ22: U34.AB21 (IO_L12P_T1U_N10_GC_64)
A.DQ23: U34.AC21 (IO_L12N_T1U_N11_GC_64)
A.DQ24: U34.AB25 (IO_L2P_T0L_N2_64)
A.DQ25: U34.AF24 (IO_L3P_T0L_N4_AD15P_64)
A.DQ26: U34.AB26 (IO_L2N_T0L_N3_64)
A.DQ27: U34.AF25 (IO_L3N_T0L_N5_AD15N_64)
A.DQ28: U34.AD24 (IO_L5P_T0U_N8_AD14P_64)
A.DQ29: U34.AC24 (IO_L6N_T0U_N11_AD6N_64)
A.DQ30: U34.AD25 (IO_L5N_T0U_N9_AD14N_64)
A.DQ31: U34.AB24 (IO_L6P_T0U_N10_AD6P_64)
A.DQS0_N: U34.Y21 (IO_L19N_T3L_N1_DBC_AD9N_64)
A.DQS0_P: U34.Y20 (IO_L19P_T3L_N0_DBC_AD9P_64)
A.DQS1_N: U34.AE20 (IO_L13N_T2L_N1_GC_QBC_64)
A.DQS1_P: U34.AD20 (IO_L13P_T2L_N0_GC_QBC_64)
A.DQS2_N: U34.AF22 (IO_L7N_T1L_N1_QBC_AD13N_64)
A.DQS2_P: U34.AE22 (IO_L7P_T1L_N0_QBC_AD13P_64)
A.DQS3_N: U34.AE26 (IO_L1N_T0L_N1_DBC_64)
A.DQS3_P: U34.AE25 (IO_L1P_T0L_N0_DBC_64)
A.DQS4_N: U34.V19 (IO_L1N_T0L_N1_DBC_RS1_65)
A.DQS4_P: U34.U19 (IO_L1P_T0L_N0_DBC_RS0_65)
A.DQS5_N: U34.AC17 (IO_L22N_T3U_N7_DBC_AD0N_64)
A.DQS5_P: U34.AB17 (IO_L22P_T3U_N6_DBC_AD0P_64)
A.DQS6_N: U34.AD18 (IO_L16N_T2U_N7_QBC_AD3N_64)
A.DQS6_P: U34.AC18 (IO_L16P_T2U_N6_QBC_AD3P_64)
A.DQS7_N: U34.AB22 (IO_L10N_T1U_N7_QBC_AD4N_64)
A.DQS7_P: U34.AA22 (IO_L10P_T1U_N6_QBC_AD4P_64)
A.DQS8_N: U34.AD26 (IO_L4N_T0U_N7_DBC_AD7N_64)
A.DQS8_P: U34.AC26 (IO_L4P_T0U_N6_DBC_AD7P_64)
A.DQS9_N: U34.V22 (IO_L4N_T0U_N7_DBC_AD7N_A25_65)
A.DQS9_P: U34.V21 (IO_L4P_T0U_N6_DBC_AD7P_A24_65)
A.PAR: U34.W24 (IO_L12N_T1U_N11_GC_A09_D25_65)
B.CA0: U34.U25 (IO_L14N_T2L_N3_GC_A05_D21_65)
B.CA1: U34.R25 (IO_L18P_T2U_N10_AD2P_D12_65)
B.CA2: U34.T25 (IO_L14P_T2L_N2_GC_A04_D20_65)
B.CA3: U34.P26 (IO_L17N_T2U_N9_AD10N_D15_65)
B.CA4: U34.P25 (IO_L17P_T2U_N8_AD10P_D14_65)
B.CA5: U34.P24 (IO_L15N_T2L_N5_AD11N_A03_D19_65)
B.CA6: U34.N24 (IO_L15P_T2L_N4_AD11P_A02_D18_65)
B.CB0: U34.P19 (IO_L23N_T3U_N9_PERSTN1_I2C_SDA_65)
B.CB1: U34.N21 (IO_L24P_T3U_N10_EMCCLK_65)
B.CB2: U34.N22 (IO_L24N_T3U_N11_DOUT_CSO_B_65)
B.CB3: U34.N19 (IO_L23P_T3U_N8_I2C_SCLK_65)
B.CB4: U34.P20 (IO_L20P_T3L_N2_AD1P_D08_65)
B.CB5: U34.R21 (IO_L21N_T3L_N5_AD8N_D07_65)
B.CB6: U34.R20 (IO_L21P_T3L_N4_AD8P_D06_65)
B.CB7: U34.P21 (IO_L20N_T3L_N3_AD1N_D09_65)
B.CS0_c: U34.T24 (IO_L13P_T2L_N0_GC_QBC_A06_D22_65)
B.CS1_c: U34.U24 (IO_L13N_T2L_N1_GC_QBC_A07_D23_65)
B.DQ0: U34.M21 (IO_L2N_T0L_N3_66)
B.DQ1: U34.M20 (IO_L2P_T0L_N2_66)
B.DQ2: U34.J19 (IO_L3P_T0L_N4_AD15P_66)
B.DQ3: U34.J20 (IO_L3N_T0L_N5_AD15N_66)
B.DQ4: U34.K21 (IO_L5P_T0U_N8_AD14P_66)
B.DQ5: U34.K20 (IO_L6N_T0U_N11_AD6N_66)
B.DQ6: U34.L20 (IO_L6P_T0U_N10_AD6P_66)
B.DQ7: U34.J21 (IO_L5N_T0U_N9_AD14N_66)
B.DQ8: U34.M26 (IO_L8N_T1L_N3_AD5N_66)
B.DQ9: U34.M25 (IO_L8P_T1L_N2_AD5P_66)
B.DQ10: U34.K26 (IO_L9N_T1L_N5_AD12N_66)
B.DQ11: U34.K25 (IO_L9P_T1L_N4_AD12P_66)
B.DQ12: U34.J24 (IO_L12N_T1U_N11_GC_66)
B.DQ13: U34.K23 (IO_L11N_T1U_N9_GC_66)
B.DQ14: U34.J23 (IO_L12P_T1U_N10_GC_66)
B.DQ15: U34.K22 (IO_L11P_T1U_N8_GC_66)
B.DQ16: U34.H23 (IO_L14P_T2L_N2_GC_66)
B.DQ17: U34.J25 (IO_L15P_T2L_N4_AD11P_66)
B.DQ18: U34.H24 (IO_L14N_T2L_N3_GC_66)
B.DQ19: U34.J26 (IO_L15N_T2L_N5_AD11N_66)
B.DQ20: U34.G26 (IO_L17N_T2U_N9_AD10N_66)
B.DQ21: U34.H22 (IO_L18N_T2U_N11_AD2N_66)
B.DQ22: U34.H26 (IO_L17P_T2U_N8_AD10P_66)
B.DQ23: U34.H21 (IO_L18P_T2U_N10_AD2P_66)
B.DQ24: U34.F23 (IO_L20P_T3L_N2_AD1P_66)
B.DQ25: U34.D24 (IO_L21P_T3L_N4_AD8P_66)
B.DQ26: U34.E23 (IO_L20N_T3L_N3_AD1N_66)
B.DQ27: U34.D25 (IO_L21N_T3L_N5_AD8N_66)
B.DQ28: U34.B26 (IO_L24N_T3U_N11_66)
B.DQ29: U34.B25 (IO_L24P_T3U_N10_66)
B.DQ30: U34.C26 (IO_L23N_T3U_N9_66)
B.DQ31: U34.D26 (IO_L23P_T3U_N8_66)
B.DQS0_N: U34.K18 (IO_L1N_T0L_N1_DBC_66)
B.DQS0_P: U34.L18 (IO_L1P_T0L_N0_DBC_66)
B.DQS1_N: U34.L23 (IO_L7N_T1L_N1_QBC_AD13N_66)
B.DQS1_P: U34.L22 (IO_L7P_T1L_N0_QBC_AD13P_66)
B.DQS2_N: U34.G25 (IO_L13N_T2L_N1_GC_QBC_66)
B.DQS2_P: U34.G24 (IO_L13P_T2L_N0_GC_QBC_66)
B.DQS3_N: U34.E26 (IO_L19N_T3L_N1_DBC_AD9N_66)
B.DQS3_P: U34.E25 (IO_L19P_T3L_N0_DBC_AD9P_66)
B.DQS4_N: U34.P23 (IO_L22N_T3U_N7_DBC_AD0N_D05_65)
B.DQS4_P: U34.N23 (IO_L22P_T3U_N6_DBC_AD0P_D04_65)
B.DQS5_N: U34.L19 (IO_L4N_T0U_N7_DBC_AD7N_66)
B.DQS5_P: U34.M19 (IO_L4P_T0U_N6_DBC_AD7P_66)
B.DQS6_N: U34.L25 (IO_L10N_T1U_N7_QBC_AD4N_66)
B.DQS6_P: U34.L24 (IO_L10P_T1U_N6_QBC_AD4P_66)
B.DQS7_N: U34.F25 (IO_L16N_T2U_N7_QBC_AD3N_66)
B.DQS7_P: U34.F24 (IO_L16P_T2U_N6_QBC_AD3P_66)
B.DQS8_N: U34.C24 (IO_L22N_T3U_N7_DBC_AD0N_66)
B.DQS8_P: U34.D23 (IO_L22P_T3U_N6_DBC_AD0P_66)
B.DQS9_N: U34.R23 (IO_L19N_T3L_N1_DBC_AD9N_D11_65)
B.DQS9_P: U34.R22 (IO_L19P_T3L_N0_DBC_AD9P_D10_65)
B.PAR: U34.R26 (IO_L18N_T2U_N11_AD2N_D13_65)
CTRL.CK_N: U34.W26 (IO_L10N_T1U_N7_QBC_AD4N_A13_D29_65)
CTRL.CK_P: U34.W25 (IO_L10P_T1U_N6_QBC_AD4P_A12_D28_65)
CTRL.DLBDQ: U34.U26 (IO_L16P_T2U_N6_QBC_AD3P_A00_D16_65)
CTRL.DLBDQS: U34.V26 (IO_L16N_T2U_N7_QBC_AD3N_A01_D17_65)
CTRL.PWR_GOOD: U34.N26 (IO_T2U_N12_CSI_ADV_B_65)
CTRL.~ALERT: U34.AA23 (IO_T1U_N12_SMBALERT_65)
CTRL.~RESET: U34.T19 (IO_T3U_N12_PERSTN0_65)
DAC_VREF: R255.1
ETH.MDC: U34.C22 (IO_L24P_T3U_N10_67)
ETH.MDIO: U34.A24 (IO_L23P_T3U_N8_67)
ETH.REF_CLK: U34.B24 (IO_L21N_T3L_N5_AD8N_67)
ETH.RXC: U34.B21 (IO_L22N_T3U_N7_DBC_AD0N_67)
ETH.RXD0: U34.A19 (IO_L18P_T2U_N10_AD2P_67)
ETH.RXD1: U34.B17 (IO_L15N_T2L_N5_AD11N_67)
ETH.RXD2: U34.C17 (IO_L15P_T2L_N4_AD11P_67)
ETH.RXD3: U34.A15 (IO_L17N_T2U_N9_AD10N_67)
ETH.RX_CTL: U34.C21 (IO_L22P_T3U_N6_DBC_AD0P_67)
ETH.TXC: U34.E21 (IO_L20P_T3L_N2_AD1P_67)
ETH.TXD0: U34.B15 (IO_L17P_T2U_N8_AD10P_67)
ETH.TXD1: U34.A18 (IO_L16N_T2U_N7_QBC_AD3N_67)
ETH.TXD2: U34.A20 (IO_L18N_T2U_N11_AD2N_67)
ETH.TXD3: U34.A17 (IO_L16P_T2U_N6_QBC_AD3P_67)
ETH.TX_CTL: U34.D21 (IO_L20N_T3L_N3_AD1N_67)
ETH.~INT: U34.A25 (IO_L23N_T3U_N9_67)
ETH.~RESET: U34.C23 (IO_L21P_T3L_N4_AD8P_67)
GCLK_100_LVDS+: U34.B19 (IO_L14P_T2L_N2_GC_67), Y3.4 (OUT+)
GCLK_100_LVDS-: U34.B20 (IO_L14N_T2L_N3_GC_67), Y3.5 (OUT-)
GND: C164.1, C333.2, C334.2, C335.2, C336.2, R129.1, R130.1, R131.1, R132.1, R133.2, R134.2, R180.2, R182.2, R254.1, Y3.3 (GND)
HDMI_REC_CLK_N: U34.D20 (IO_L12N_T1U_N11_GC_67)
HDMI_REC_CLK_P: U34.D19 (IO_L12P_T1U_N10_GC_67)
HyperRAM.CK_N: U34.E17 (IO_L4N_T0U_N7_DBC_AD7N_67)
HyperRAM.CK_P: U34.E16 (IO_L4P_T0U_N6_DBC_AD7P_67)
HyperRAM.DQ0: U34.H16 (IO_L5P_T0U_N8_AD14P_67)
HyperRAM.DQ1: U34.C16 (IO_L6N_T0U_N11_AD6N_67)
HyperRAM.DQ2: U34.E15 (IO_L3P_T0L_N4_AD15P_67)
HyperRAM.DQ3: U34.D15 (IO_L3N_T0L_N5_AD15N_67)
HyperRAM.DQ4: U34.G16 (IO_L5N_T0U_N9_AD14N_67)
HyperRAM.DQ5: U34.H17 (IO_L2P_T0L_N2_67)
HyperRAM.DQ6: U34.D16 (IO_L6P_T0U_N10_AD6P_67)
HyperRAM.DQ7: U34.G17 (IO_L2N_T0L_N3_67)
HyperRAM.RWDS: U34.G15 (IO_L1P_T0L_N0_DBC_67)
HyperRAM.~CS: U34.H18 (IO_L7P_T1L_N0_QBC_AD13P_67)
HyperRAM.~RESET: U34.F15 (IO_L1N_T0L_N1_DBC_67)
unnamed: R253.1, R254.2, R256.1
SD.CD: U34.E20 (IO_L10N_T1U_N7_QBC_AD4N_67)
SD.CLK: U34.F18 (IO_L8P_T1L_N2_AD5P_67)
SD.CMD: U34.H19 (IO_L7N_T1L_N1_QBC_AD13N_67)
SD.DAT0: U34.G20 (IO_L9P_T1L_N4_AD12P_67)
SD.DAT1: U34.G21 (IO_L9N_T1L_N5_AD12N_67)
SD.DAT2: U34.F19 (IO_L8N_T1L_N3_AD5N_67)
SD.DAT3: U34.F20 (IO_L10P_T1U_N6_QBC_AD4P_67)
VDDQ: R253.2, U34.AA21 (VCCO_64), U34.AB18 (VCCO_64), U34.AD22 (VCCO_64), U34.E24 (VCCO_66), U34.H25 (VCCO_66), U34.J22 (VCCO_66), U34.P22 (VCCO_65), U34.U23 (VCCO_65), U34.Y24 (VCCO_65)
VREF: R255.2, R256.2, R257.2, R258.2, R259.2, R260.2
VREF_64: C333.1, R129.2, R257.1, U34.W18 (VREF_64)
VREF_65: C334.1, R130.2, R258.1, U34.V18 (VREF_65)
VREF_66: C335.1, R131.2, R259.1, U34.J18 (VREF_66)
VREF_67: C336.1, R132.2, R260.1, U34.J16 (VREF_67)
VRP_64: R133.1, U34.AF23 (IO_T0U_N12_VRP_64)
VRP_65: R134.1, U34.W21 (IO_T0U_N12_VRP_A28_65)
VRP_66: R180.1, U34.M22 (IO_T0U_N12_VRP_66)
VRP_67: R182.1, U34.F17 (IO_T0U_N12_VRP_67)

Notes on the sheet:
Clock source
VCCO (HP banks) max: 1.9V
Reference termination
HP Banks
Pinout 1.1.1
VREF
