antmicro/rdimm-ddr5-tester/fpga-mgt.kicad_sch

## KiCad design fpga-mgt.kicad_sch (2026-05-21)

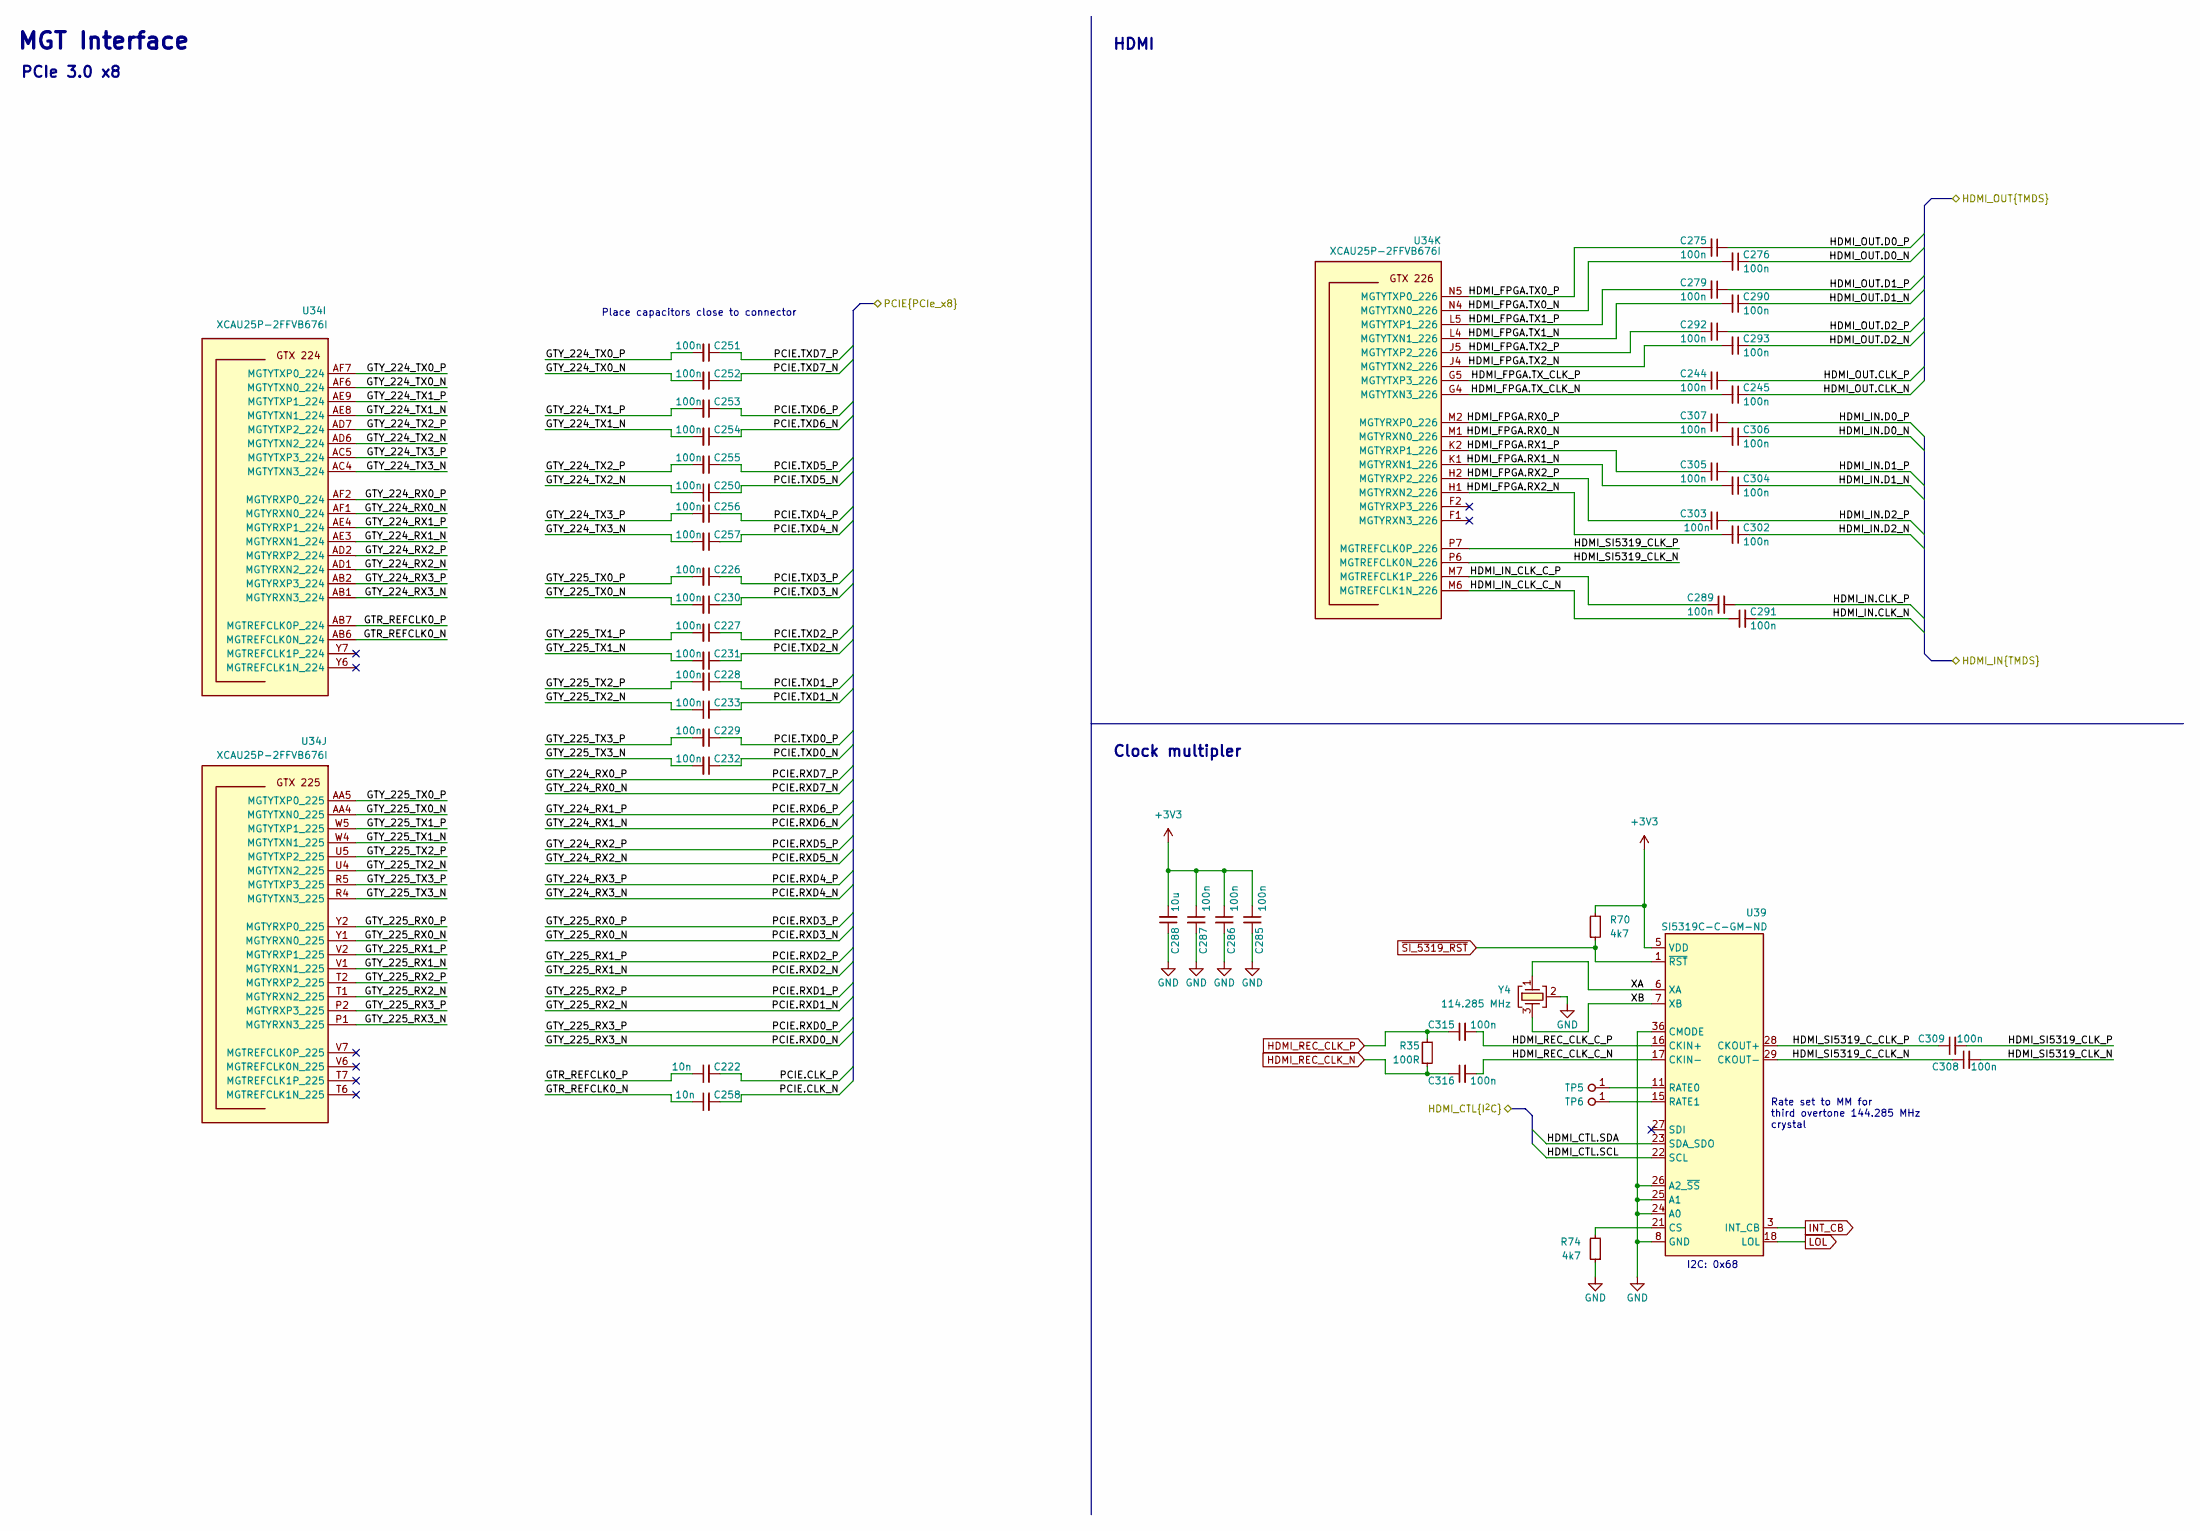
[picture p12: schematic fpga-mgt.kicad_sch]

Parts:
C222, C258: C_10n_0402; C_0402_1005Metric; Voltage 50V; MPN GRM155R71H103KA88D
C226, C227, C228, C229, C230, C231, C232, C233, C244, C245, C250, C251, C252, C253, C254, C255, C256, C257, C275, C276, C279, C285, C286, C287, C289, C290, C291, C292, C293, C302, C303, C304, C305, C306, C307, C308, C309, C315, C316: C_100n_0402; C_0402_1005Metric; Voltage 50V; MPN GRM155R61H104KE14D
C288: C_10u_10V_0402; C_0402_1005Metric; Voltage 10V; MPN GRM155R61A106ME11D
R35: R_100R_0402; R_0402_1005Metric_EIA; Tolerance 1%; MPN CR0402-FX-1000GLF
R70, R74: R_4k7_0402; R_0402_1005Metric; Tolerance 1%; MPN CR0402-FX-4701GLF
TP5, TP6: TP_0.75mm_SMD; TP_SMD_0.75mm
U34: XCAU25P-2FFVB676I; BGA-676_27x27mm_Layout26x26_P1x1mm_FFVB676; MPN XCAU25P-2FFVB676I
U39: SI5319C-C-GM-ND; QFN-36-1EP_6x6mm_P0.5mm_EP3.7x3.7mm; MPN SI5319C-C-GM-ND
Y4: Resonator_114.285MHZ_ABM8; Resonator_SMD_Abracon_ABM8G_3.2x2.5mm; MPN ABM8-166-114.285MHZ-T2

Connections:
+3V3: C285.1, C286.1, C287.1, C288.2, R70.2, U39.5 (VDD), U39.10 (VDD), U39.32 (VDD)
GND: C285.2, C286.2, C287.2, C288.1, R74.1, U39.8 (GND), U39.19 (GND), U39.20 (GND), U39.24 (A0), U39.25 (A1), U39.26 (A2_~SS), U39.31 (GND), U39.36 (CMODE), U39.37 (GND), Y4.2 (SH), Y4.4 (SH)
GTR_REFCLK0_N: C222.1, U34.AB6 (MGTREFCLK0N_224)
GTR_REFCLK0_P: C258.1, U34.AB7 (MGTREFCLK0P_224)
GTY_224_RX0_N: U34.AF1 (MGTYRXN0_224)
GTY_224_RX0_P: U34.AF2 (MGTYRXP0_224)
GTY_224_RX1_N: U34.AE3 (MGTYRXN1_224)
GTY_224_RX1_P: U34.AE4 (MGTYRXP1_224)
GTY_224_RX2_N: U34.AD1 (MGTYRXN2_224)
GTY_224_RX2_P: U34.AD2 (MGTYRXP2_224)
GTY_224_RX3_N: U34.AB1 (MGTYRXN3_224)
GTY_224_RX3_P: U34.AB2 (MGTYRXP3_224)
GTY_224_TX0_N: C252.2, U34.AF6 (MGTYTXN0_224)
GTY_224_TX0_P: C251.2, U34.AF7 (MGTYTXP0_224)
GTY_224_TX1_N: C254.2, U34.AE8 (MGTYTXN1_224)
GTY_224_TX1_P: C253.2, U34.AE9 (MGTYTXP1_224)
GTY_224_TX2_N: C250.1, U34.AD6 (MGTYTXN2_224)
GTY_224_TX2_P: C255.2, U34.AD7 (MGTYTXP2_224)
GTY_224_TX3_N: C257.2, U34.AC4 (MGTYTXN3_224)
GTY_224_TX3_P: C256.2, U34.AC5 (MGTYTXP3_224)
GTY_225_RX0_N: U34.Y1 (MGTYRXN0_225)
GTY_225_RX0_P: U34.Y2 (MGTYRXP0_225)
GTY_225_RX1_N: U34.V1 (MGTYRXN1_225)
GTY_225_RX1_P: U34.V2 (MGTYRXP1_225)
GTY_225_RX2_N: U34.T1 (MGTYRXN2_225)
GTY_225_RX2_P: U34.T2 (MGTYRXP2_225)
GTY_225_RX3_N: U34.P1 (MGTYRXN3_225)
GTY_225_RX3_P: U34.P2 (MGTYRXP3_225)
GTY_225_TX0_N: C230.2, U34.AA4 (MGTYTXN0_225)
GTY_225_TX0_P: C226.2, U34.AA5 (MGTYTXP0_225)
GTY_225_TX1_N: C231.2, U34.W4 (MGTYTXN1_225)
GTY_225_TX1_P: C227.2, U34.W5 (MGTYTXP1_225)
GTY_225_TX2_N: C233.1, U34.U4 (MGTYTXN2_225)
GTY_225_TX2_P: C228.2, U34.U5 (MGTYTXP2_225)
GTY_225_TX3_N: C232.2, U34.R4 (MGTYTXN3_225)
GTY_225_TX3_P: C229.2, U34.R5 (MGTYTXP3_225)
HDMI_CTL.SCL: U39.22 (SCL)
HDMI_CTL.SDA: U39.23 (SDA_SDO)
HDMI_FPGA.RX0_N: C306.2, U34.M1 (MGTYRXN0_226)
HDMI_FPGA.RX0_P: C307.2, U34.M2 (MGTYRXP0_226)
HDMI_FPGA.RX1_N: C304.2, U34.K1 (MGTYRXN1_226)
HDMI_FPGA.RX1_P: C305.2, U34.K2 (MGTYRXP1_226)
HDMI_FPGA.RX2_N: C302.2, U34.H1 (MGTYRXN2_226)
HDMI_FPGA.RX2_P: C303.2, U34.H2 (MGTYRXP2_226)
HDMI_FPGA.TX0_N: C276.2, U34.N4 (MGTYTXN0_226)
HDMI_FPGA.TX0_P: C275.2, U34.N5 (MGTYTXP0_226)
HDMI_FPGA.TX1_N: C290.2, U34.L4 (MGTYTXN1_226)
HDMI_FPGA.TX1_P: C279.2, U34.L5 (MGTYTXP1_226)
HDMI_FPGA.TX2_N: C293.2, U34.J4 (MGTYTXN2_226)
HDMI_FPGA.TX2_P: C292.2, U34.J5 (MGTYTXP2_226)
HDMI_FPGA.TX_CLK_N: C245.2, U34.G4 (MGTYTXN3_226)
HDMI_FPGA.TX_CLK_P: C244.2, U34.G5 (MGTYTXP3_226)
HDMI_IN.CLK_N: C291.2
HDMI_IN.CLK_P: C289.2
HDMI_IN.D0_N: C306.1
HDMI_IN.D0_P: C307.1
HDMI_IN.D1_N: C304.1
HDMI_IN.D1_P: C305.1
HDMI_IN.D2_N: C302.1
HDMI_IN.D2_P: C303.1
HDMI_IN_CLK_C_N: C291.1, U34.M6 (MGTREFCLK1N_226)
HDMI_IN_CLK_C_P: C289.1, U34.M7 (MGTREFCLK1P_226)
HDMI_OUT.CLK_N: C245.1
HDMI_OUT.CLK_P: C244.1
HDMI_OUT.D0_N: C276.1
HDMI_OUT.D0_P: C275.1
HDMI_OUT.D1_N: C290.1
HDMI_OUT.D1_P: C279.1
HDMI_OUT.D2_N: C293.1
HDMI_OUT.D2_P: C292.1
HDMI_REC_CLK_C_N: C316.2, U39.17 (CKIN-)
HDMI_REC_CLK_C_P: C315.2, U39.16 (CKIN+)
HDMI_REC_CLK_N: C316.1, R35.1
HDMI_REC_CLK_P: C315.1, R35.2
HDMI_SI5319_CLK_N: C308.2, U34.P6 (MGTREFCLK0N_226)
HDMI_SI5319_CLK_P: C309.2, U34.P7 (MGTREFCLK0P_226)
HDMI_SI5319_C_CLK_N: C308.1, U39.29 (CKOUT-)
HDMI_SI5319_C_CLK_P: C309.1, U39.28 (CKOUT+)
INT_CB: U39.3 (INT_CB)
LOL: U39.18 (LOL)
unnamed: R74.2, U39.21 (CS)
unnamed: TP5.1, U39.11 (RATE0)
unnamed: TP6.1, U39.15 (RATE1)
PCIE.CLK_N: C222.2
PCIE.CLK_P: C258.2
PCIE.TXD0_N: C232.1
PCIE.TXD0_P: C229.1
PCIE.TXD1_N: C233.2
PCIE.TXD1_P: C228.1
PCIE.TXD2_N: C231.1
PCIE.TXD2_P: C227.1
PCIE.TXD3_N: C230.1
PCIE.TXD3_P: C226.1
PCIE.TXD4_N: C257.1
PCIE.TXD4_P: C256.1
PCIE.TXD5_N: C250.2
PCIE.TXD5_P: C255.1
PCIE.TXD6_N: C254.1
PCIE.TXD6_P: C253.1
PCIE.TXD7_N: C252.1
PCIE.TXD7_P: C251.1
XA: U39.6 (XA), Y4.1
XB: U39.7 (XB), Y4.3
~SI_5319_RST: R70.1, U39.1 (~RST)

Notes on the sheet:
Place capacitors close to connector
Rate set to MM for third overtone 144.285 MHz crystal
I2C: 0x68
PCIe 3.0 x8
MGT Interface
HDMI
Clock multipler
