antmicro/rdimm-ddr5-tester/fpga-power.kicad_sch

## KiCad design fpga-power.kicad_sch (2026-05-21)

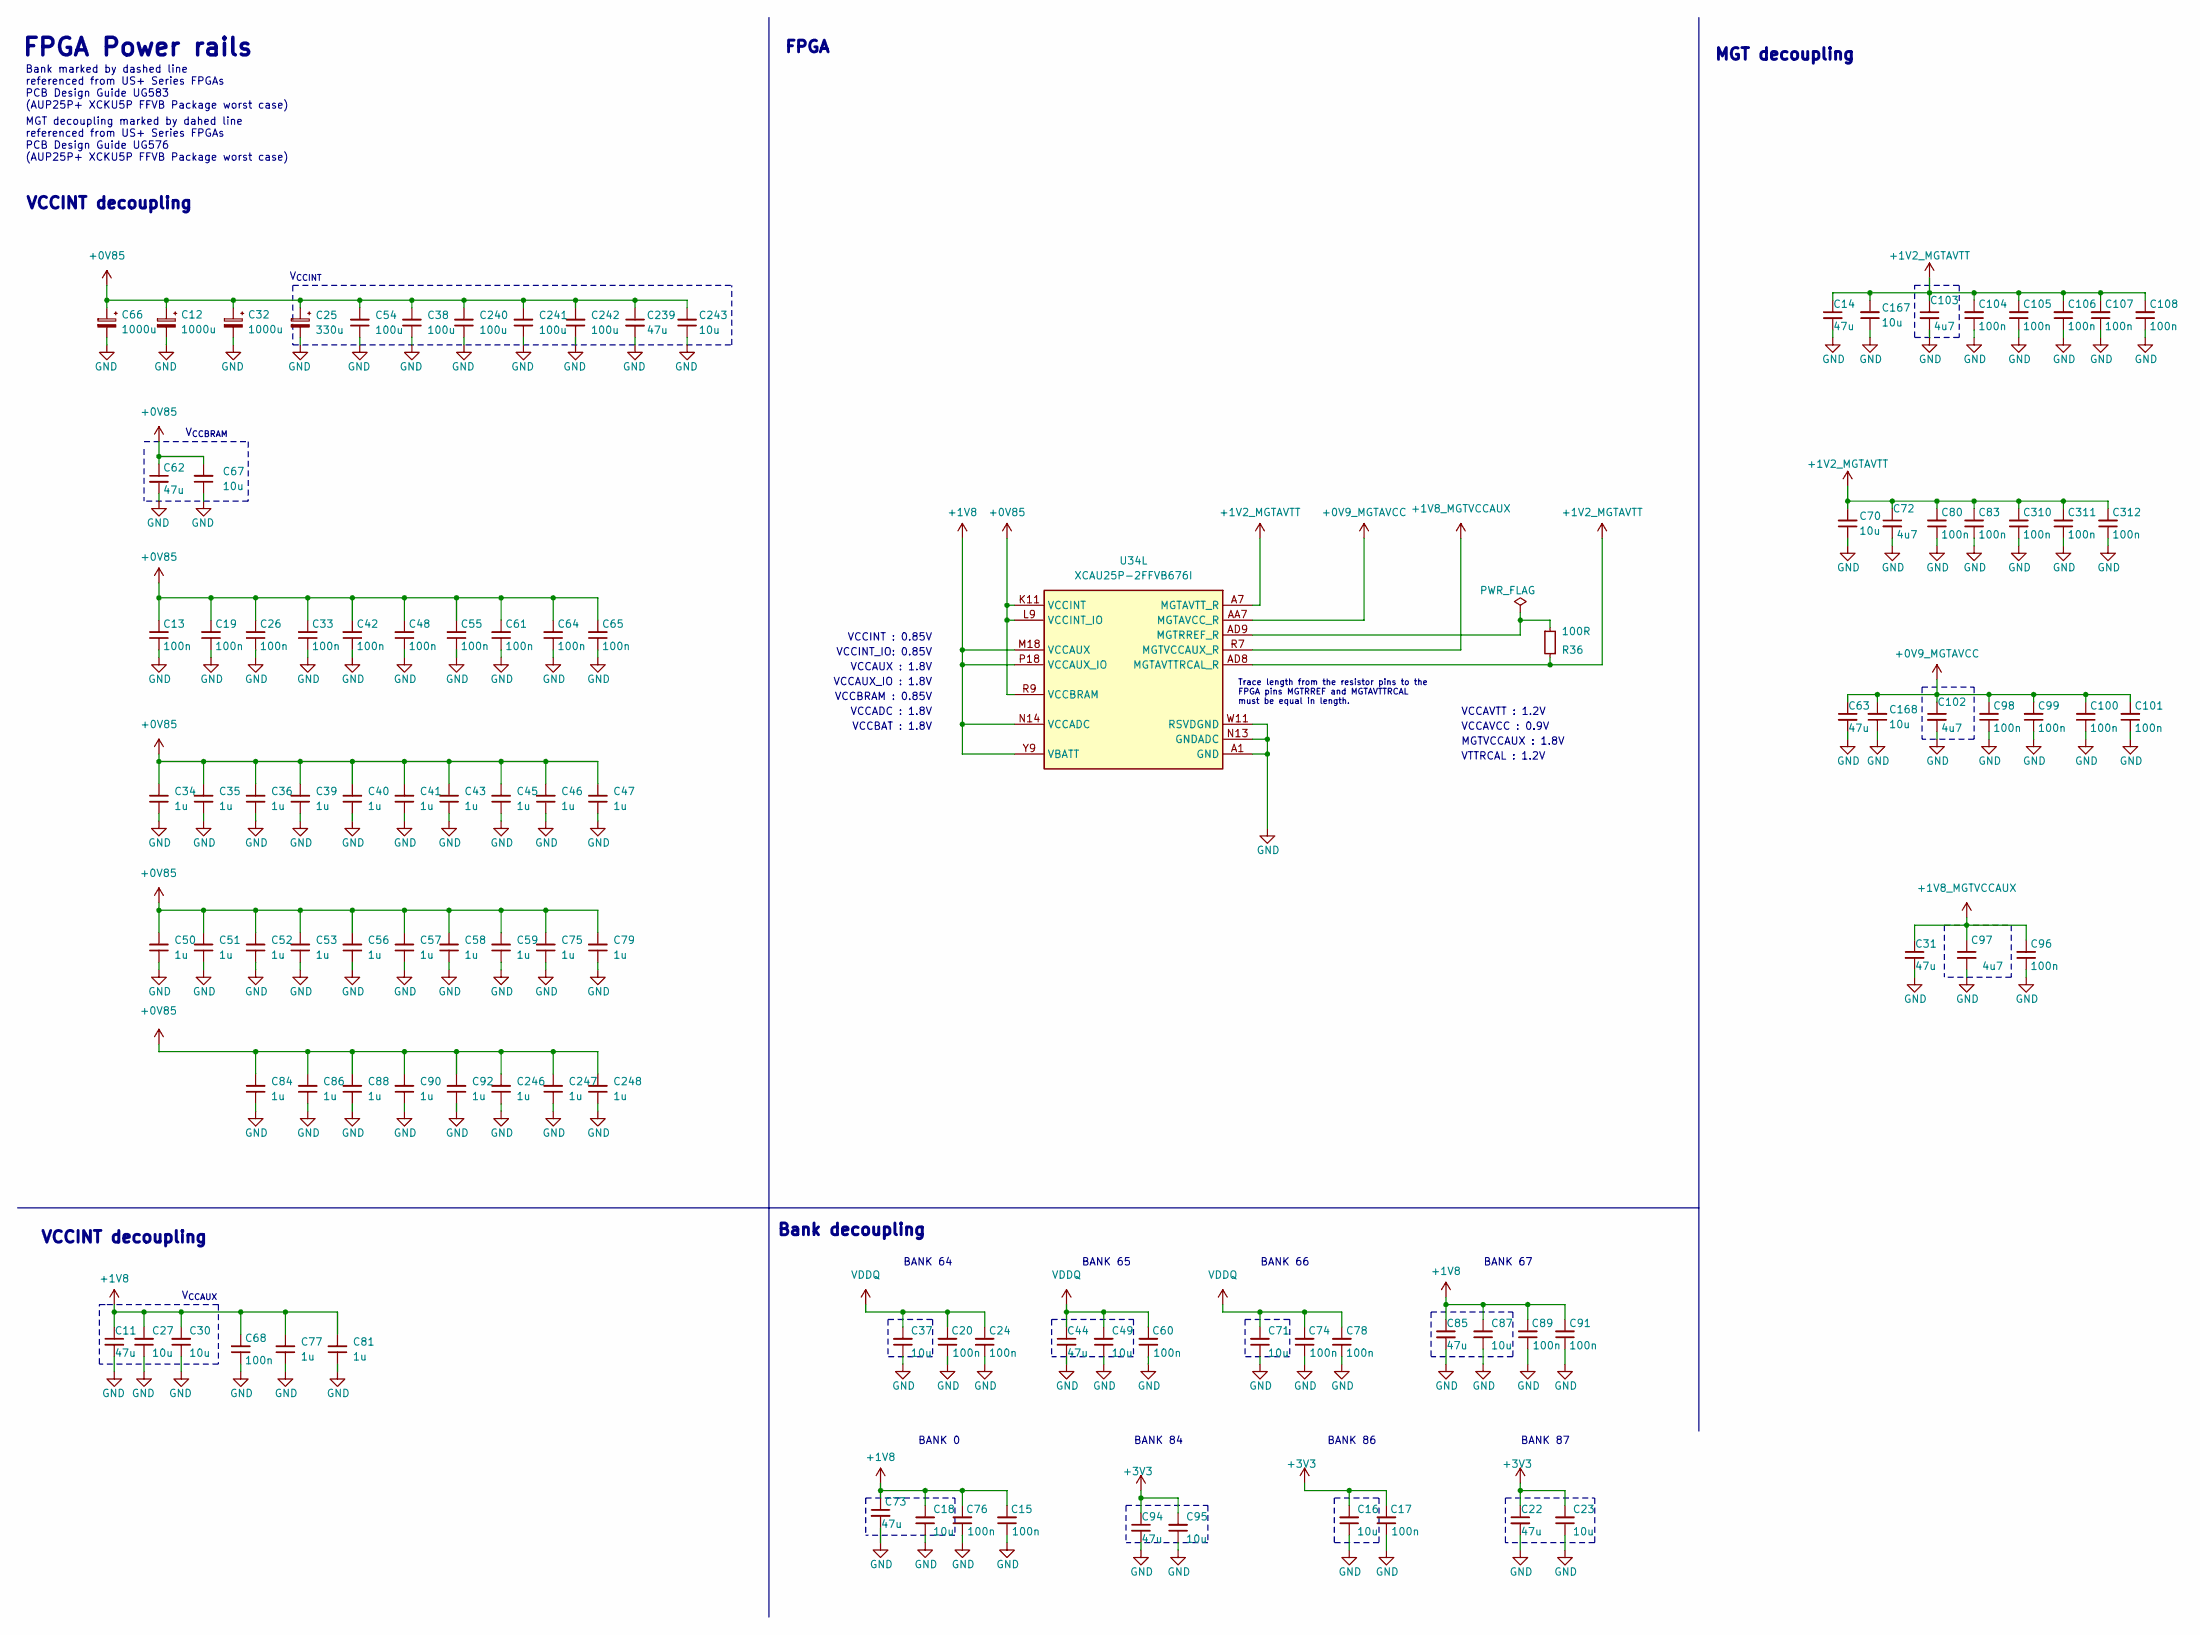
[picture p13: schematic fpga-power.kicad_sch]

Parts:
C11, C14, C22, C31, C44, C62, C63, C73, C85, C94, C239: C_47u_0603; C_0603_1608Metric; MPN GRM188R60J476ME15D
C12, C32, C66: C_Pol_1m_2.5V_KEMET-T520-D; C_Pol_EIA-D; Voltage 2.5V; MPN T520D108M2R5ATE030
C13, C15, C17, C19, C20, C24, C26, C33, C42, C48, C55, C60, C61, C64, C65, C68, C74, C76, C78, C80, C83, C89, C91, C96, C98, C99, C100, C101, C104, C105, C106, C107, C108, C310, C311, C312: C_100n_0402; C_0402_1005Metric_EIA; Voltage 50V; MPN GRM155R61H104KE14D
C16, C18, C23, C27, C30, C37, C49, C67, C70, C71, C87, C95, C167, C168, C243: C_10u_10V_0402; C_0402_1005Metric_EIA; Voltage 10V; MPN GRM155R61A106ME11D
C25: C_Pol_330u_6.3V_KEMET-T520-B; C_Pol_EIA-B; Voltage 6.3V; MPN T520B337M006ATE040
C34, C35, C36, C39, C40, C41, C43, C45, C46, C47, C50, C51, C52, C53, C56, C57, C58, C59, C75, C77, C79, C81, C84, C86, C88, C90, C92, C246, C247, C248: C_1u_25V_0402; C_0402_1005Metric_EIA; Voltage 25V; MPN GRM155R61E105KE11J
C38, C54, C240, C241, C242: C_100u_0805; C_0805_2012Metric; MPN GRM21BR60J107ME15L
C72, C97, C102, C103: C_4u7_0402; C_0402_1005Metric_EIA; MPN GRM155R61A475MEAAD
R36: R_100R_0402; R_0402_1005Metric_EIA; Tolerance 1%; MPN CR0402-FX-1000GLF
U34: XCAU25P-2FFVB676I; BGA-676_27x27mm_Layout26x26_P1x1mm_FFVB676; MPN XCAU25P-2FFVB676I

Connections:
+0V9_MGTAVCC: C63.1, C98.2, C99.2, C100.2, C101.2, C102.1, C168.2, U34.AA7 (MGTAVCC_R), U34.AC7 (MGTAVCC_R), U34.J7 (MGTAVCC_R), U34.L7 (MGTAVCC_R), U34.N7 (MGTAVCC_R), U34.W7 (MGTAVCC_R)
+0V85: C12.1, C13.2, C19.2, C25.1, C26.2, C32.1, C33.2, C34.2, C35.2, C36.2, C38.2, C39.2, C40.2, C41.2, C42.2, C43.2, C45.2, C46.2, C47.2, C48.2, C50.2, C51.2, C52.2, C53.2, C54.2, C55.2, C56.2, C57.2, C58.2, C59.2, C61.2, C62.1, C64.2, C65.2, C66.1, C67.2, C75.2, C79.2, C84.2, C86.2, C88.2, C90.2, C92.2, C239.1, C240.2, C241.2, C242.2, C243.2, C246.2, C247.2, C248.2, U34.K11 (VCCINT), U34.K13 (VCCINT), U34.K15 (VCCINT), U34.K17 (VCCINT), U34.L9 (VCCINT_IO), U34.L10 (VCCINT), U34.L12 (VCCINT), U34.L14 (VCCINT), U34.L16 (VCCINT), U34.M9 (VCCINT_IO), U34.M11 (VCCINT), U34.M13 (VCCINT), U34.M15 (VCCINT), U34.M17 (VCCINT), U34.N9 (VCCINT_IO), U34.N10 (VCCINT), U34.N12 (VCCINT), U34.N16 (VCCINT), U34.P9 (VCCINT_IO), U34.P11 (VCCINT), U34.P15 (VCCINT), U34.P17 (VCCINT), U34.R9 (VCCBRAM), U34.R10 (VCCINT), U34.R12 (VCCINT), U34.R16 (VCCINT), U34.T9 (VCCBRAM), U34.T11 (VCCINT), U34.T15 (VCCINT), U34.T17 (VCCINT), U34.U9 (VCCBRAM), U34.U10 (VCCINT), U34.U12 (VCCINT), U34.U14 (VCCINT), U34.U16 (VCCINT), U34.V9 (VCCBRAM), U34.V11 (VCCINT), U34.V13 (VCCINT), U34.V15 (VCCINT), U34.V17 (VCCINT)
+1V2_MGTAVTT: C14.1, C70.2, C72.1, C80.2, C83.2, C103.1, C104.2, C105.2, C106.2, C107.2, C108.2, C167.2, C310.2, C311.2, C312.2, R36.2, U34.A7 (MGTAVTT_R), U34.AB5 (MGTAVTT_R), U34.AD8 (MGTAVTTRCAL_R), U34.AE7 (MGTAVTT_R), U34.C7 (MGTAVTT_R), U34.E7 (MGTAVTT_R), U34.F5 (MGTAVTT_R), U34.G7 (MGTAVTT_R), U34.H5 (MGTAVTT_R), U34.K5 (MGTAVTT_R), U34.M5 (MGTAVTT_R), U34.P5 (MGTAVTT_R), U34.T5 (MGTAVTT_R), U34.V5 (MGTAVTT_R), U34.Y5 (MGTAVTT_R)
+1V8: C11.1, C15.2, C18.2, C27.2, C30.2, C68.2, C73.1, C76.2, C77.2, C81.2, C85.1, C87.2, C89.2, C91.2, U34.M18 (VCCAUX), U34.N14 (VCCADC), U34.N18 (VCCAUX), U34.P18 (VCCAUX_IO), U34.R18 (VCCAUX_IO), U34.T18 (VCCAUX_IO), U34.Y9 (VBATT)
+1V8_MGTVCCAUX: C31.1, C96.2, C97.1, U34.R7 (MGTVCCAUX_R), U34.U7 (MGTVCCAUX_R)
+3V3: C16.2, C17.2, C22.1, C23.2, C94.1, C95.2
GND: C11.2, C12.2, C13.1, C14.2, C15.1, C16.1, C17.1, C18.1, C19.1, C20.1, C22.2, C23.1, C24.1, C25.2, C26.1, C27.1, C30.1, C31.2, C32.2, C33.1, C34.1, C35.1, C36.1, C37.1, C38.1, C39.1, C40.1, C41.1, C42.1, C43.1, C44.2, C45.1, C46.1, C47.1, C48.1, C49.1, C50.1, C51.1, C52.1, C53.1, C54.1, C55.1, C56.1, C57.1, C58.1, C59.1, C60.1, C61.1, C62.2, C63.2, C64.1, C65.1, C66.2, C67.1, C68.1, C70.1, C71.1, C72.2, C73.2, C74.1, C75.1, C76.1, C77.1, C78.1, C79.1, C80.1, C81.1, C83.1, C84.1, C85.2, C86.1, C87.1, C88.1, C89.1, C90.1, C91.1, C92.1, C94.2, C95.1, C96.1, C97.2, C98.1, C99.1, C100.1, C101.1, C102.2, C103.2, C104.1, C105.1, C106.1, C107.1, C108.1, C167.1, C168.1, C239.2, C240.1, C241.1, C242.1, C243.1, C246.1, C247.1, C248.1, C310.1, C311.1, C312.1, U34.A1 (GND), U34.A2 (GND), U34.A5 (GND), U34.A6 (GND), U34.A8 (GND), U34.A11 (GND), U34.A16 (GND), U34.A21 (GND), U34.A26 (GND), U34.AA1 (GND), U34.AA2 (GND), U34.AA3 (GND), U34.AA6 (GND), U34.AA8 (GND), U34.AA16 (GND), U34.AA26 (GND), U34.AB3 (GND), U34.AB4 (GND), U34.AB8 (GND), U34.AB13 (GND), U34.AB23 (GND), U34.AC1 (GND), U34.AC2 (GND), U34.AC3 (GND), U34.AC6 (GND), U34.AC8 (GND), U34.AC9 (GND), U34.AC10 (GND), U34.AC20 (GND), U34.AC25 (GND), U34.AD3 (GND), U34.AD4 (GND), U34.AD5 (GND), U34.AD10 (GND), U34.AD17 (GND), U34.AE1 (GND), U34.AE2 (GND), U34.AE5 (GND), U34.AE6 (GND), U34.AE10 (GND), U34.AE14 (GND), U34.AE19 (GND), U34.AE24 (GND), U34.AF3 (GND), U34.AF4 (GND), U34.AF5 (GND), U34.AF8 (GND), U34.AF9 (GND), U34.AF10 (GND), U34.AF11 (GND), U34.AF16 (GND), U34.AF21 (GND), U34.AF26 (GND), U34.B3 (GND), U34.B4 (GND), U34.B5 (GND), U34.B8 (GND), U34.B13 (GND), U34.B18 (GND), U34.B23 (GND), U34.C1 (GND), U34.C2 (GND), U34.C5 (GND), U34.C6 (GND), U34.C8 (GND), U34.C10 (GND), U34.C15 (GND), U34.C25 (GND), U34.D3 (GND), U34.D4 (GND), U34.D5 (GND), U34.D8 (GND), U34.D12 (GND), U34.D22 (GND), U34.E1 (GND), U34.E2 (GND), U34.E3 (GND), U34.E6 (GND), U34.E8 (GND), U34.E19 (GND), U34.F3 (GND), U34.F4 (GND), U34.F8 (GND), U34.F11 (GND), U34.F16 (GND), U34.F21 (GND), U34.F26 (GND), U34.G1 (GND), U34.G2 (GND), U34.G3 (GND), U34.G6 (GND), U34.G8 (GND), U34.G13 (GND), U34.G23 (GND), U34.H3 (GND), U34.H4 (GND), U34.H8 (GND), U34.H20 (GND), U34.J1 (GND), U34.J2 (GND), U34.J3 (GND), U34.J6 (GND), U34.J8 (GND), U34.J17 (GND), U34.K3 (GND), U34.K4 (GND), U34.K8 (GND), U34.K12 (GND), U34.K14 (GND), U34.K16 (GND), U34.K19 (GND), U34.K24 (GND), U34.L1 (GND), U34.L2 (GND), U34.L3 (GND), U34.L6 (GND), U34.L8 (GND), U34.L11 (GND), U34.L13 (GND), U34.L15 (GND), U34.L17 (GND), U34.L21 (GND), U34.L26 (GND), U34.M3 (GND), U34.M4 (GND), U34.M8 (GND), U34.M10 (GND), U34.M12 (GND), U34.M14 (GND), U34.M16 (GND), U34.M23 (GND), U34.N1 (GND), U34.N2 (GND), U34.N3 (GND), U34.N6 (GND), U34.N8 (GND), U34.N11 (GND), U34.N13 (GNDADC), U34.N15 (GND), U34.N17 (GND), U34.N20 (GND), U34.N25 (GND), U34.P3 (GND), U34.P4 (GND), U34.P8 (GND), U34.P10 (GND), U34.P12 (GND), U34.P16 (GND), U34.R1 (GND), U34.R2 (GND), U34.R3 (GND), U34.R6 (GND), U34.R8 (GND), U34.R11 (GND), U34.R15 (GND), U34.R17 (GND), U34.R19 (GND), U34.R24 (GND), U34.T3 (GND), U34.T4 (GND), U34.T8 (GND), U34.T10 (GND), U34.T12 (GND), U34.T16 (GND), U34.T21 (GND), U34.T26 (GND), U34.U1 (GND), U34.U2 (GND), U34.U3 (GND), U34.U6 (GND), U34.U8 (GND), U34.U11 (GND), U34.U13 (GND), U34.U15 (GND), U34.U17 (GND), U34.U18 (GND), U34.V3 (GND), U34.V4 (GND), U34.V8 (GND), U34.V10 (GND), U34.V12 (GND), U34.V14 (GND), U34.V16 (GND), U34.V20 (GND), U34.V25 (GND), U34.W1 (GND), U34.W2 (GND), U34.W3 (GND), U34.W6 (GND), U34.W8 (GND), U34.W11 (RSVDGND), U34.W17 (GND), U34.W22 (GND), U34.Y3 (GND), U34.Y4 (GND), U34.Y8 (GND), U34.Y19 (GND)
unnamed: R36.1, U34.AD9 (MGTRREF_R)
VDDQ: C20.2, C24.2, C37.2, C44.1, C49.2, C60.2, C71.2, C74.2, C78.2

Notes on the sheet:
BANK 64
VCCBAT : 1.8V
FPGA Power rails
BANK 84
BANK 65
VCCADC : 1.8V
V_{CCAUX}
BANK 0
Bank decoupling
Trace length from the resistor pins to the FPGA pins MGTRREF and MGTAVTTRCAL must be equal in length.
FPGA
VCCINT_IO: 0.85V
VCCINT decoupling
VTTRCAL : 1.2V
VCCAVCC : 0.9V
MGTVCCAUX : 1.8V
BANK 87
VCCBRAM : 0.85V
VCCAVTT : 1.2V
BANK 67
V_{CCINT}
MGT decoupling
VCCINT : 0.85V
Bank marked by dashed line referenced from US+ Series FPGAs PCB Design Guide UG583 (AUP25P+ XCKU5P FFVB Package worst case)
V_{CCBRAM}
VCCAUX_IO : 1.8V
BANK 86
MGT decoupling marked by dahed line referenced from US+ Series FPGAs PCB Design Guide UG576 (AUP25P+ XCKU5P FFVB Package worst case)
VCCAUX : 1.8V
BANK 66
