antmicro/rdimm-ddr5-tester/hdmi-sd-card.kicad_sch

## KiCad design hdmi-sd-card.kicad_sch (2026-05-25)

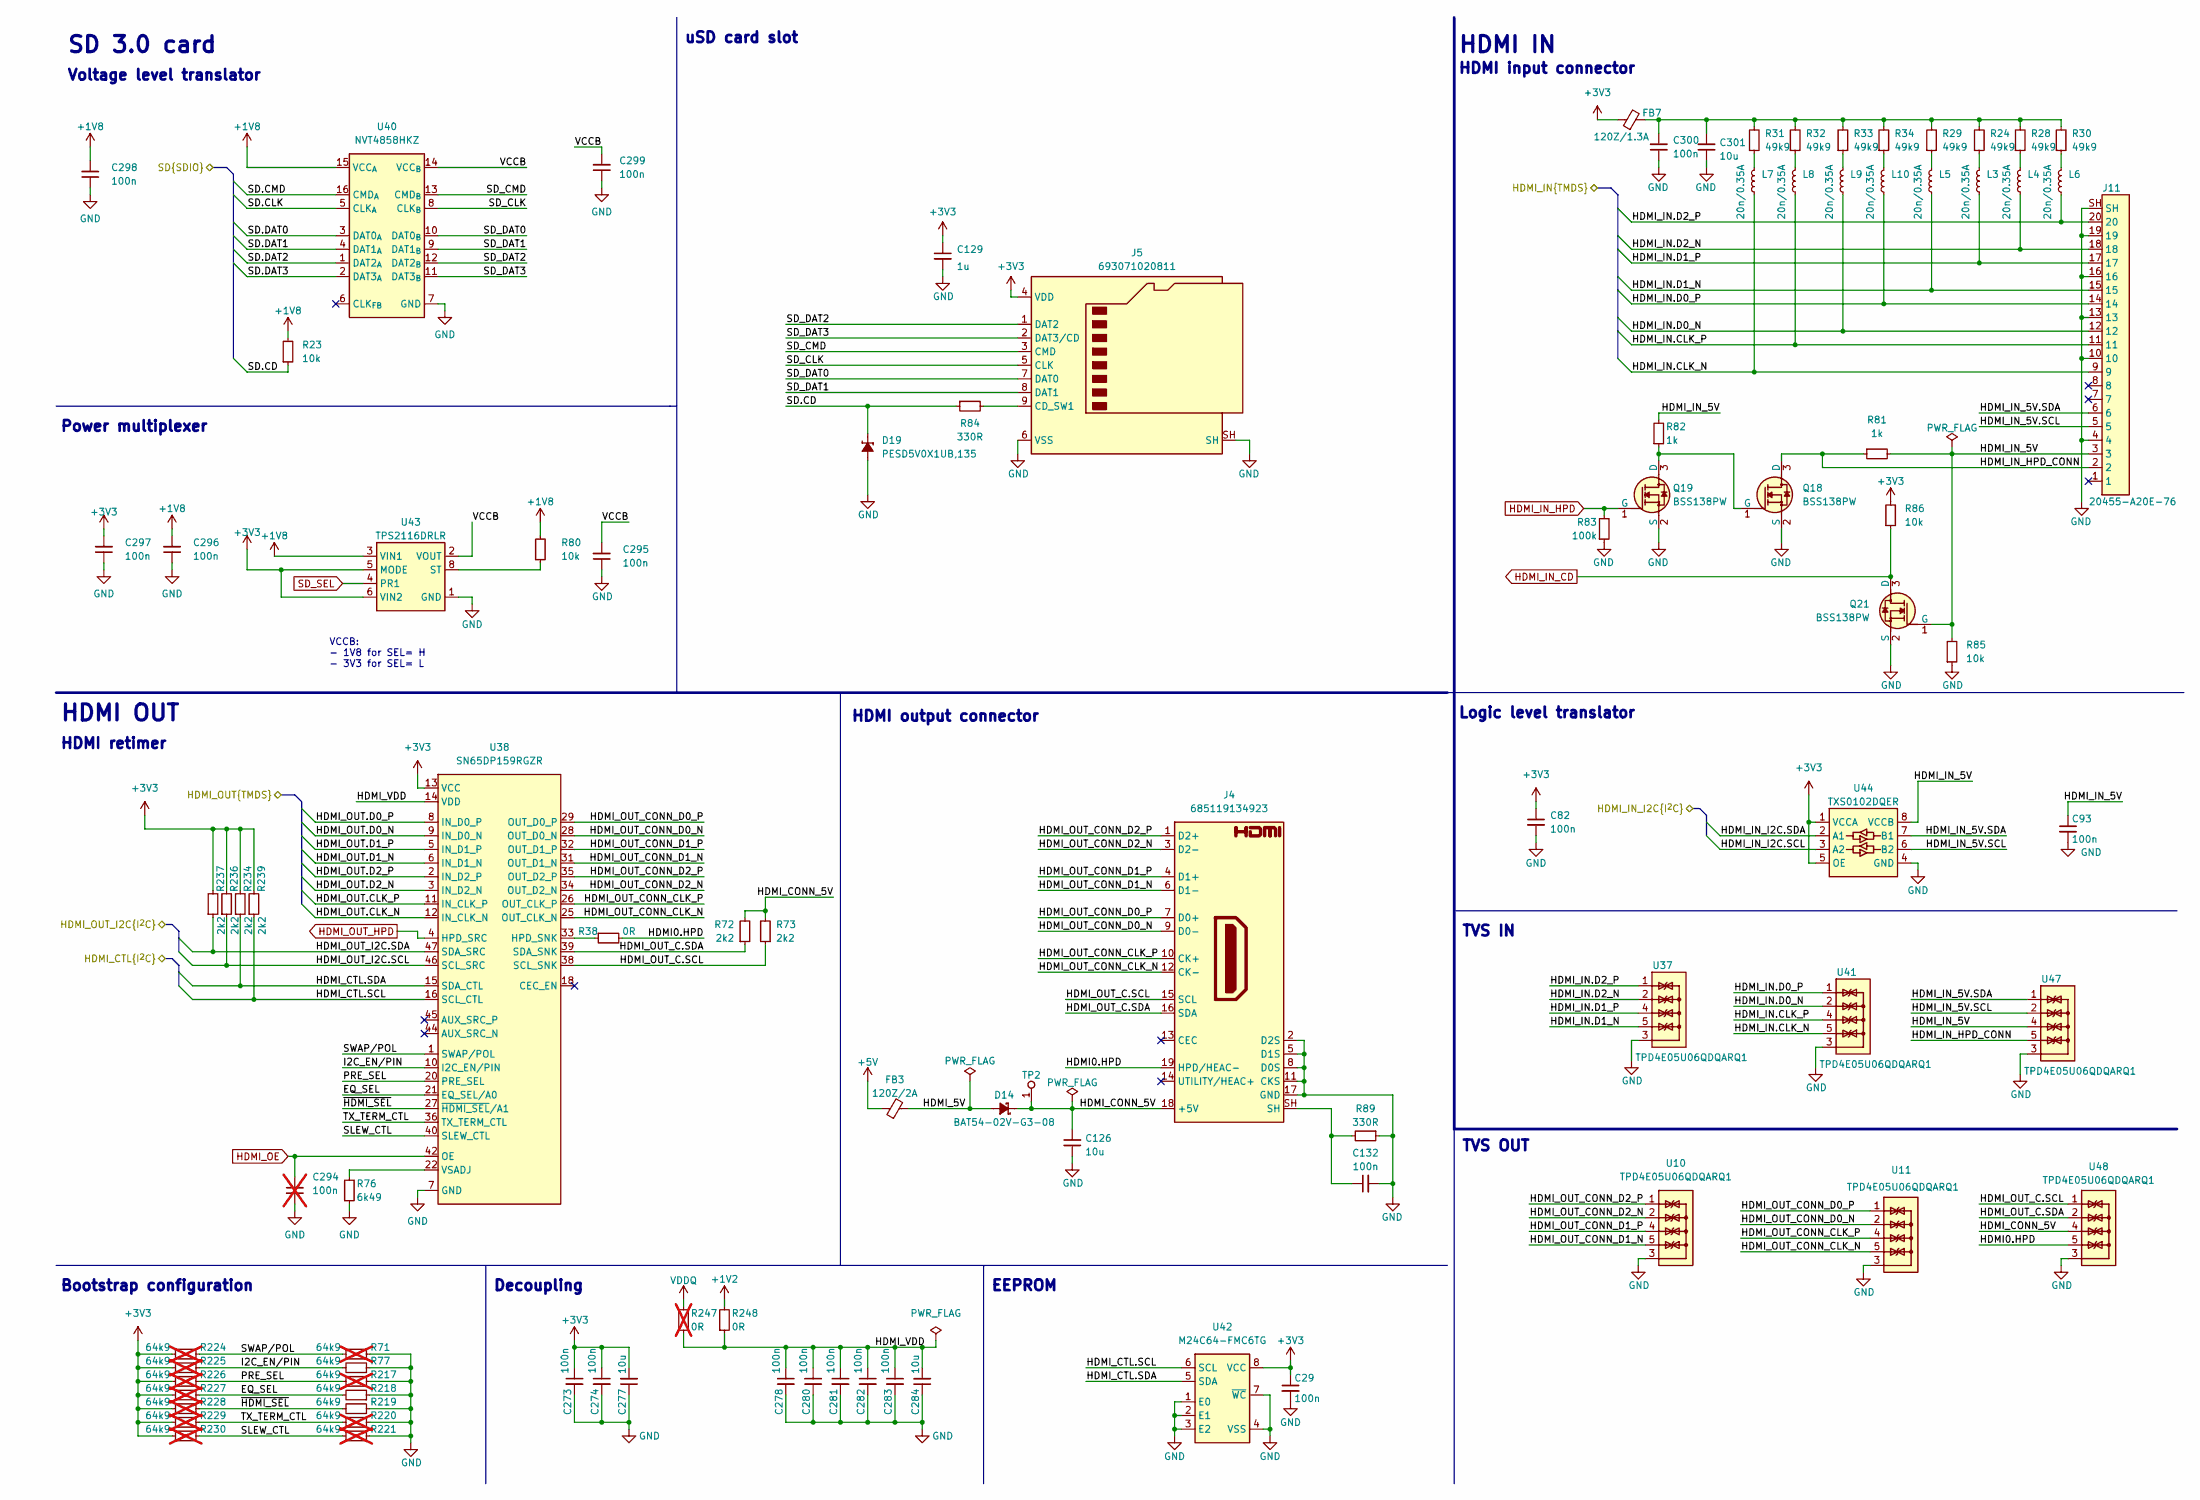
[picture p14: schematic hdmi-sd-card.kicad_sch]

Parts:
C29, C82, C93, C132, C273, C274, C278, C280, C281, C282, C283, C295, C296, C297, C298, C299, C300: C_100n_0402; C_0402_1005Metric; Voltage 50V; MPN GRM155R61H104KE14D
C126, C301: C_10u_6.3V_0402; C_0402_1005Metric; Voltage 6.3V; MPN GRM155R60J106ME15D
C129: C_1u_0402; C_0402_1005Metric; MPN C1005X6S1A105K050BC
C277, C284: C_10u_10V_0402; C_0402_1005Metric; Voltage 10V; MPN GRM155R61A106ME11D
C294: C_100n_0402; C_0402_1005Metric; Voltage 50V; MPN GRM155R61H104KE14D; not fitted
D14: BAT54-02V-G3-08; SOD-523; MPN BAT54-02V-G3-08
D19: PESD5V0X1UB; SOD-523; MPN PESD5V0X1UB,135
FB3: FB_120Z_2A_Murata-BLM18PG_0603; FB_0603_1608Metric; MPN BLM18PG121SN1D
FB7: FB_120Z_1.3A_Murata-BLM15PD_0402; FB_0402_1005Metric; MPN BLM15PD121SN1D
J4: HDMI-A_WE_685119134923; HDMI-A_Receptacle_WE_685119134923; MPN 685119134923
J5: MicroSD_693071020811; MicroSD_Wurth_693071020811; MPN 693071020811
J11: I-PEX_CABLINE-VS_1x20_20455-A20E-76; MPN 20455-A20E-76
L3, L4, L5, L6, L7, L8, L9, L10: L_20n_0.35A_0402; L_0402_1005Metric; MPN MLG1005S20NJTD25
Q18, Q19, Q21: BSS138PW; SC70-3; MPN BSS138PW
R23, R80, R85, R86: R_10k_0402; R_0402_1005Metric; Tolerance 1%; MPN CR0402-FX-1002GLF
R24, R28, R29, R30, R31, R32, R33, R34: R_49k9_0402; R_0402_1005Metric; Tolerance 1%; MPN CR0402-FX-4992GLF
R38, R248: R_0R_0402; R_0402_1005Metric; MPN ERJ2GE0R00X
R71, R217, R220, R221, R224, R225, R226, R227, R228, R229, R230: R_64k9_0402; R_0402_1005Metric; Tolerance 1%; MPN CR0402-FX-6492GLF; not fitted
R72, R73, R234, R236, R237, R239: R_2k2_0402; R_0402_1005Metric; Tolerance 1%; MPN CR0402-FX-2201GLF
R76: R_6k49_0402; R_0402_1005Metric; Tolerance 1%; MPN RMCF0402FT6K49
R77, R218, R219: R_64k9_0402; R_0402_1005Metric; Tolerance 1%; MPN CR0402-FX-6492GLF
R81, R82: R_1k_0402; R_0402_1005Metric; Tolerance 1%; MPN CR0402-FX-1001GLF
R83: R_100k_0402; R_0402_1005Metric; Tolerance 1%; MPN CR0402-FX-1003GLF
R84, R89: R_330R_0402; R_0402_1005Metric; Tolerance 1%; MPN CR0402-FX-3300GLF
R247: R_0R_0402; R_0402_1005Metric; MPN ERJ2GE0R00X; not fitted
TP2: TP_1mm_SMD; TP_SMD_1mm
U10, U11, U37, U41, U47, U48: TPD4E05U06QDQARQ1; USON-10_2.5x1mm_P0.5mm; MPN TPD4E05U06QDQARQ1
U38: SN65DP159RGZR; VQFN-48_7x7mm_P0.5mm_EP4.1x4.1mm; MPN SN65DP159RGZR
U40: NVT4858_XQFN; SOT1161-2; MPN NVT4858HKZ
U42: M24C64-F_DFN8; DFN-8-1EP_3x2mm_P0.5mm_EP1.36x1.46mm; MPN M24C64-FMC6TG
U43: TPS2116DRLR; SOT-583; MPN TPS2116DRLR
U44: TXS0102DQER; X2SON8_1.4x1x0.32mm_P0.35mm; MPN TXS0102DQER

Connections:
+1V2: R248.2
+1V8: C296.2, C298.2, R23.2, R80.2, U40.15 (VCC_{A}), U43.3 (VIN1)
+3V3: C29.1, C82.1, C129.1, C273.1, C274.1, C277.2, C297.2, FB7.1, J5.4 (VDD), R86.2, R224.2, R225.2, R226.2, R227.2, R228.2, R229.2, R230.2, R234.2, R236.2, R237.2, R239.2, U38.13 (VCC), U38.43 (VCC), U42.8 (VCC), U43.5 (MODE), U43.6 (VIN2), U44.1 (VCCA), U44.5 (OE)
+5V: FB3.1
EQ_SEL: R218.2, R227.1, U38.21 (EQ_SEL/A0)
GND: C29.2, C82.2, C93.2, C126.1, C129.2, C132.2, C273.2, C274.2, C277.1, C278.2, C280.2, C281.2, C282.2, C283.2, C284.1, C294.2, C295.1, C296.1, C297.1, C298.1, C299.1, C300.1, C301.1, D19.2 (A), J4.2 (D2S), J4.5 (D1S), J4.8 (D0S), J4.11 (CKS), J4.17 (GND), J5.6 (VSS), J5.SH, J11.4, J11.10, J11.13, J11.16, J11.19, J11.SH, Q18.2 (S), Q19.2 (S), Q21.2 (S), R71.1, R76.1, R77.1, R83.1, R85.1, R89.1, R217.1, R218.1, R219.1, R220.1, R221.1, U10.3, U10.8, U11.3, U11.8, U37.3, U37.8, U38.7 (GND), U38.19 (GND), U38.30 (GND), U38.41 (GND), U38.49 (GND), U40.7 (GND), U41.3, U41.8, U42.1 (E0), U42.2 (E1), U42.3 (E2), U42.4 (VSS), U42.7 (~WC), U42.9 (VSS), U43.1 (GND), U44.4 (GND), U47.3, U47.8, U48.3, U48.8
HDMI0.HPD: J4.19 (HPD/HEAC-), R38.2, U48.5, U48.6
HDMI_5V: D14.2 (A), FB3.2
HDMI_CONN_5V: C126.2, D14.1 (C), J4.18 (+5V), R72.2, R73.2, TP2.1, U48.4, U48.7
HDMI_CTL.SCL: R239.1, U38.16 (SCL_CTL), U42.6 (SCL)
HDMI_CTL.SDA: R234.1, U38.15 (SDA_CTL), U42.5 (SDA)
HDMI_IN.CLK_N: J11.9, L7.1, U41.5, U41.6
HDMI_IN.CLK_P: J11.11, L8.1, U41.4, U41.7
HDMI_IN.D0_N: J11.12, L9.1, U41.2, U41.9
HDMI_IN.D0_P: J11.14, L10.1, U41.1, U41.10
HDMI_IN.D1_N: J11.15, L5.1, U37.5, U37.6
HDMI_IN.D1_P: J11.17, L3.1, U37.4, U37.7
HDMI_IN.D2_N: J11.18, L4.1, U37.2, U37.9
HDMI_IN.D2_P: J11.20, L6.1, U37.1, U37.10
HDMI_IN_5V: C93.1, J11.3, Q21.1 (G), R81.2, R82.2, R85.2, U44.8 (VCCB), U47.4, U47.7
HDMI_IN_5V.SCL: J11.5, U44.6 (B2), U47.2, U47.9
HDMI_IN_5V.SDA: J11.6, U44.7 (B1), U47.1, U47.10
HDMI_IN_CD: Q21.3 (D), R86.1
HDMI_IN_HPD: Q19.1 (G), R83.2
HDMI_IN_HPD_CONN: J11.2, Q18.3 (D), R81.1, U47.5, U47.6
HDMI_IN_I2C.SCL: U44.3 (A2)
HDMI_IN_I2C.SDA: U44.2 (A1)
HDMI_OE: C294.1, U38.42 (OE)
HDMI_OUT.CLK_N: U38.12 (IN_CLK_N)
HDMI_OUT.CLK_P: U38.11 (IN_CLK_P)
HDMI_OUT.D0_N: U38.9 (IN_D0_N)
HDMI_OUT.D0_P: U38.8 (IN_D0_P)
HDMI_OUT.D1_N: U38.6 (IN_D1_N)
HDMI_OUT.D1_P: U38.5 (IN_D1_P)
HDMI_OUT.D2_N: U38.3 (IN_D2_N)
HDMI_OUT.D2_P: U38.2 (IN_D2_P)
HDMI_OUT_C.SCL: J4.15 (SCL), R73.1, U38.38 (SCL_SNK), U48.1, U48.10
HDMI_OUT_C.SDA: J4.16 (SDA), R72.1, U38.39 (SDA_SNK), U48.2, U48.9
HDMI_OUT_CONN_CLK_N: J4.12 (CK-), U11.5, U11.6, U38.25 (OUT_CLK_N)
HDMI_OUT_CONN_CLK_P: J4.10 (CK+), U11.4, U11.7, U38.26 (OUT_CLK_P)
HDMI_OUT_CONN_D0_N: J4.9 (D0-), U11.2, U11.9, U38.28 (OUT_D0_N)
HDMI_OUT_CONN_D0_P: J4.7 (D0+), U11.1, U11.10, U38.29 (OUT_D0_P)
HDMI_OUT_CONN_D1_N: J4.6 (D1-), U10.5, U10.6, U38.31 (OUT_D1_N)
HDMI_OUT_CONN_D1_P: J4.4 (D1+), U10.4, U10.7, U38.32 (OUT_D1_P)
HDMI_OUT_CONN_D2_N: J4.3 (D2-), U10.2, U10.9, U38.34 (OUT_D2_N)
HDMI_OUT_CONN_D2_P: J4.1 (D2+), U10.1, U10.10, U38.35 (OUT_D2_P)
HDMI_OUT_HPD: U38.4 (HPD_SRC)
HDMI_OUT_I2C.SCL: R236.1, U38.46 (SCL_SRC)
HDMI_OUT_I2C.SDA: R237.1, U38.47 (SDA_SRC)
HDMI_VDD: C278.1, C280.1, C281.1, C282.1, C283.1, C284.2, R247.1, R248.1, U38.14 (VDD), U38.23 (VDD), U38.24 (VDD), U38.37 (VDD), U38.48 (VDD)
I2C_EN/PIN: R77.2, R225.1, U38.10 (I2C_EN/PIN)
unnamed: C132.1, J4.SH, R89.2
unnamed: C300.2, C301.2, FB7.2, R24.2, R28.2, R29.2, R30.2, R31.2, R32.2, R33.2, R34.2
unnamed: J5.9 (CD_SW1), R84.2
unnamed: L3.2, R24.1
unnamed: L4.2, R28.1
unnamed: L5.2, R29.1
unnamed: L6.2, R30.1
unnamed: L7.2, R31.1
unnamed: L8.2, R32.1
unnamed: L9.2, R33.1
unnamed: L10.2, R34.1
unnamed: Q18.1 (G), Q19.3 (D), R82.1
unnamed: R38.1, U38.33 (HPD_SNK)
unnamed: R76.2, U38.22 (VSADJ)
unnamed: R80.1, U43.8 (ST)
PRE_SEL: R217.2, R226.1, U38.20 (PRE_SEL)
SD.CD: D19.1 (C), R23.1, R84.1
SD.CLK: U40.5 (CLK_{A})
SD.CMD: U40.16 (CMD_{A})
SD.DAT0: U40.3 (DAT0_{A})
SD.DAT1: U40.4 (DAT1_{A})
SD.DAT2: U40.1 (DAT2_{A})
SD.DAT3: U40.2 (DAT3_{A})
SD_CLK: J5.5 (CLK), U40.8 (CLK_{B})
SD_CMD: J5.3 (CMD), U40.13 (CMD_{B})
SD_DAT0: J5.7 (DAT0), U40.10 (DAT0_{B})
SD_DAT1: J5.8 (DAT1), U40.9 (DAT1_{B})
SD_DAT2: J5.1 (DAT2), U40.12 (DAT2_{B})
SD_DAT3: J5.2 (DAT3/CD), U40.11 (DAT3_{B})
SD_SEL: U43.4 (PR1)
SLEW_CTL: R221.2, R230.1, U38.40 (SLEW_CTL)
SWAP/POL: R71.2, R224.1, U38.1 (SWAP/POL)
TX_TERM_CTL: R220.2, R229.1, U38.36 (TX_TERM_CTL)
VCCB: C295.2, C299.2, U40.14 (VCC_{B}), U43.2 (VOUT), U43.7 (VOUT)
VDDQ: R247.2
~HDMI_SEL: R219.2, R228.1, U38.27 (~HDMI_SEL/A1)

Notes on the sheet:
Power multiplexer
HDMI OUT
TVS IN
TVS OUT
uSD card slot
EEPROM
VCCB: - 1V8 for SEL= H - 3V3 for SEL= L
Bootstrap configuration
HDMI IN
SD 3.0 card
HDMI retimer
Logic level translator
Voltage level translator
HDMI input connector
HDMI output connector
Decoupling
