antmicro/rdimm-ddr5-tester/hyperram-flash.kicad_sch

## KiCad design hyperram-flash.kicad_sch (2026-05-21)

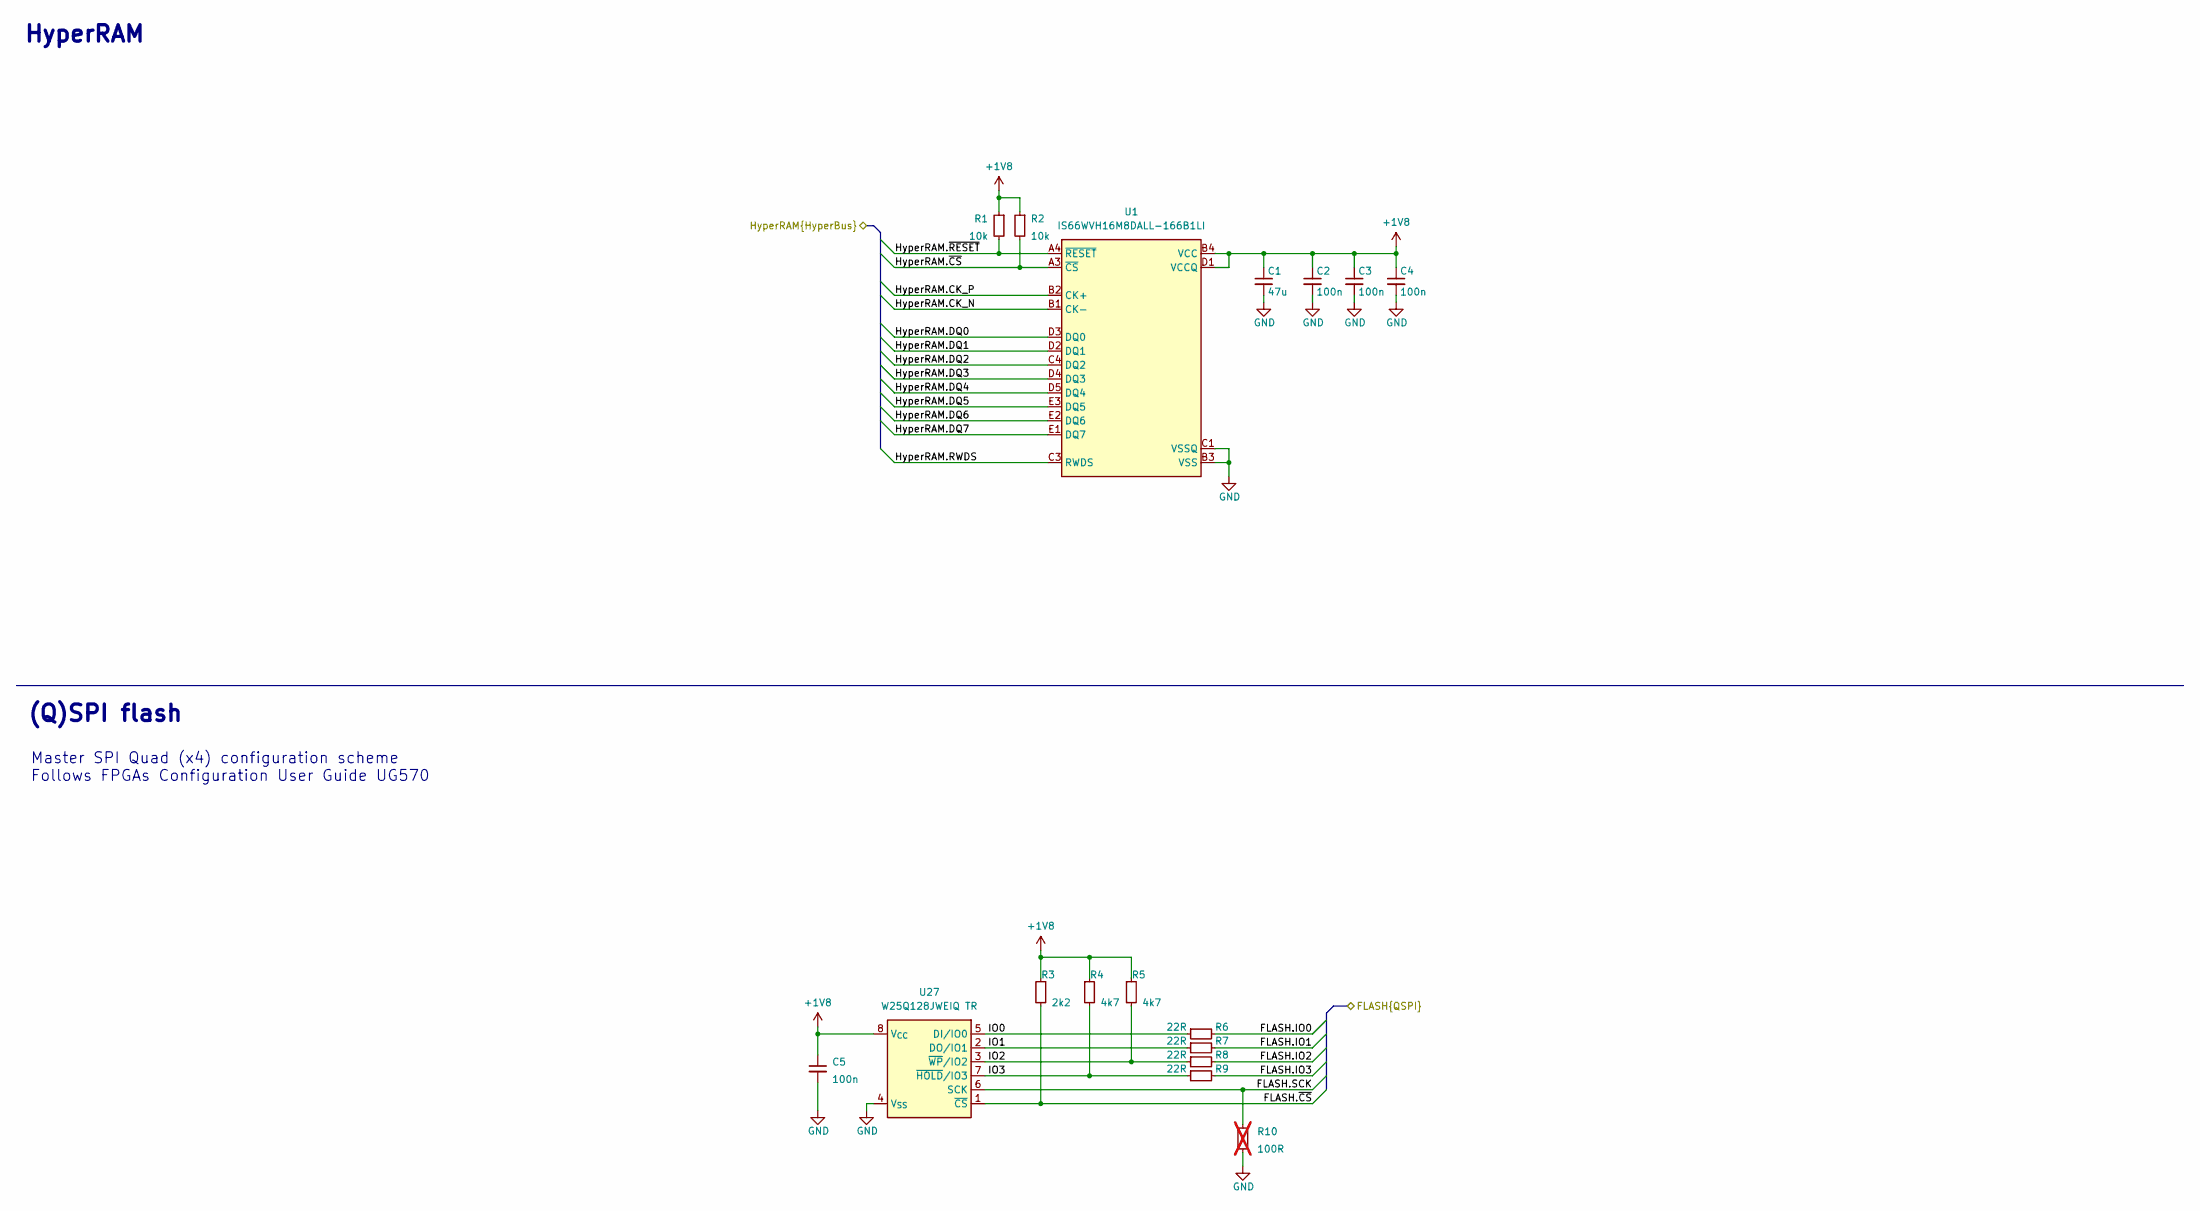
[picture p15: schematic hyperram-flash.kicad_sch]

Parts:
C1: C_47u_0603; C_0603_1608Metric; MPN GRM188R60J476ME15D
C2, C3, C4, C5: C_100n_0402; C_0402_1005Metric; Voltage 50V; MPN GRM155R61H104KE14D
R1, R2: R_10k_0402; R_0402_1005Metric; Tolerance 1%; MPN CR0402-FX-1002GLF
R3: R_2k2_0402; R_0402_1005Metric; Tolerance 1%; MPN CR0402-FX-2201GLF
R4, R5: R_4k7_0402; R_0402_1005Metric; Tolerance 1%; MPN CR0402-FX-4701GLF
R6, R7, R8, R9: R_22R_0402; R_0402_1005Metric; Tolerance 1%; MPN CR0402-FX-22R0GLF
R10: R_100R_0402; R_0402_1005Metric; Tolerance 1%; MPN CR0402-FX-1000GLF; not fitted
U1: IS66WVH16M8DALL-166B1LI; FBGA-25-24_6x8mm_Layout5x5_P1mm; MPN IS66WVH16M8DALL-166B1LI
U27: W25Q128JWEIQ; WSON-8_6x8x0.5mm_P1.27mm; MPN W25Q128JWEIQ TR

Connections:
+1V8: C1.1, C2.1, C3.1, C4.1, C5.1, R1.1, R2.1, R3.1, R4.1, R5.1, U1.B4 (VCC), U1.D1 (VCCQ), U1.E4 (VCCQ), U27.8 (V_{CC})
FLASH.IO0: R6.2
FLASH.IO1: R7.2
FLASH.IO2: R8.2
FLASH.IO3: R9.2
FLASH.SCK: R10.1, U27.6 (SCK)
FLASH.~CS: R3.2, U27.1 (~CS)
GND: C1.2, C2.2, C3.2, C4.2, C5.2, R10.2, U1.B3 (VSS), U1.C1 (VSSQ), U1.E5 (VSSQ), U27.4 (V_{SS})
HyperRAM.CK_N: U1.B1 (CK-)
HyperRAM.CK_P: U1.B2 (CK+)
HyperRAM.DQ0: U1.D3 (DQ0)
HyperRAM.DQ1: U1.D2 (DQ1)
HyperRAM.DQ2: U1.C4 (DQ2)
HyperRAM.DQ3: U1.D4 (DQ3)
HyperRAM.DQ4: U1.D5 (DQ4)
HyperRAM.DQ5: U1.E3 (DQ5)
HyperRAM.DQ6: U1.E2 (DQ6)
HyperRAM.DQ7: U1.E1 (DQ7)
HyperRAM.RWDS: U1.C3 (RWDS)
HyperRAM.~CS: R2.2, U1.A3 (~CS)
HyperRAM.~RESET: R1.2, U1.A4 (~RESET)
IO0: R6.1, U27.5 (DI/IO0)
IO1: R7.1, U27.2 (DO/IO1)
IO2: R5.2, R8.1, U27.3 (~WP/IO2)
IO3: R4.2, R9.1, U27.7 (~HOLD/IO3)

Notes on the sheet:
HyperRAM
(Q)SPI flash
Master SPI Quad (x4) configuration scheme Follows FPGAs Configuration User Guide UG570
