antmicro/rdimm-ddr5-tester/i2c.kicad_sch

## KiCad design i2c.kicad_sch (2026-05-25)

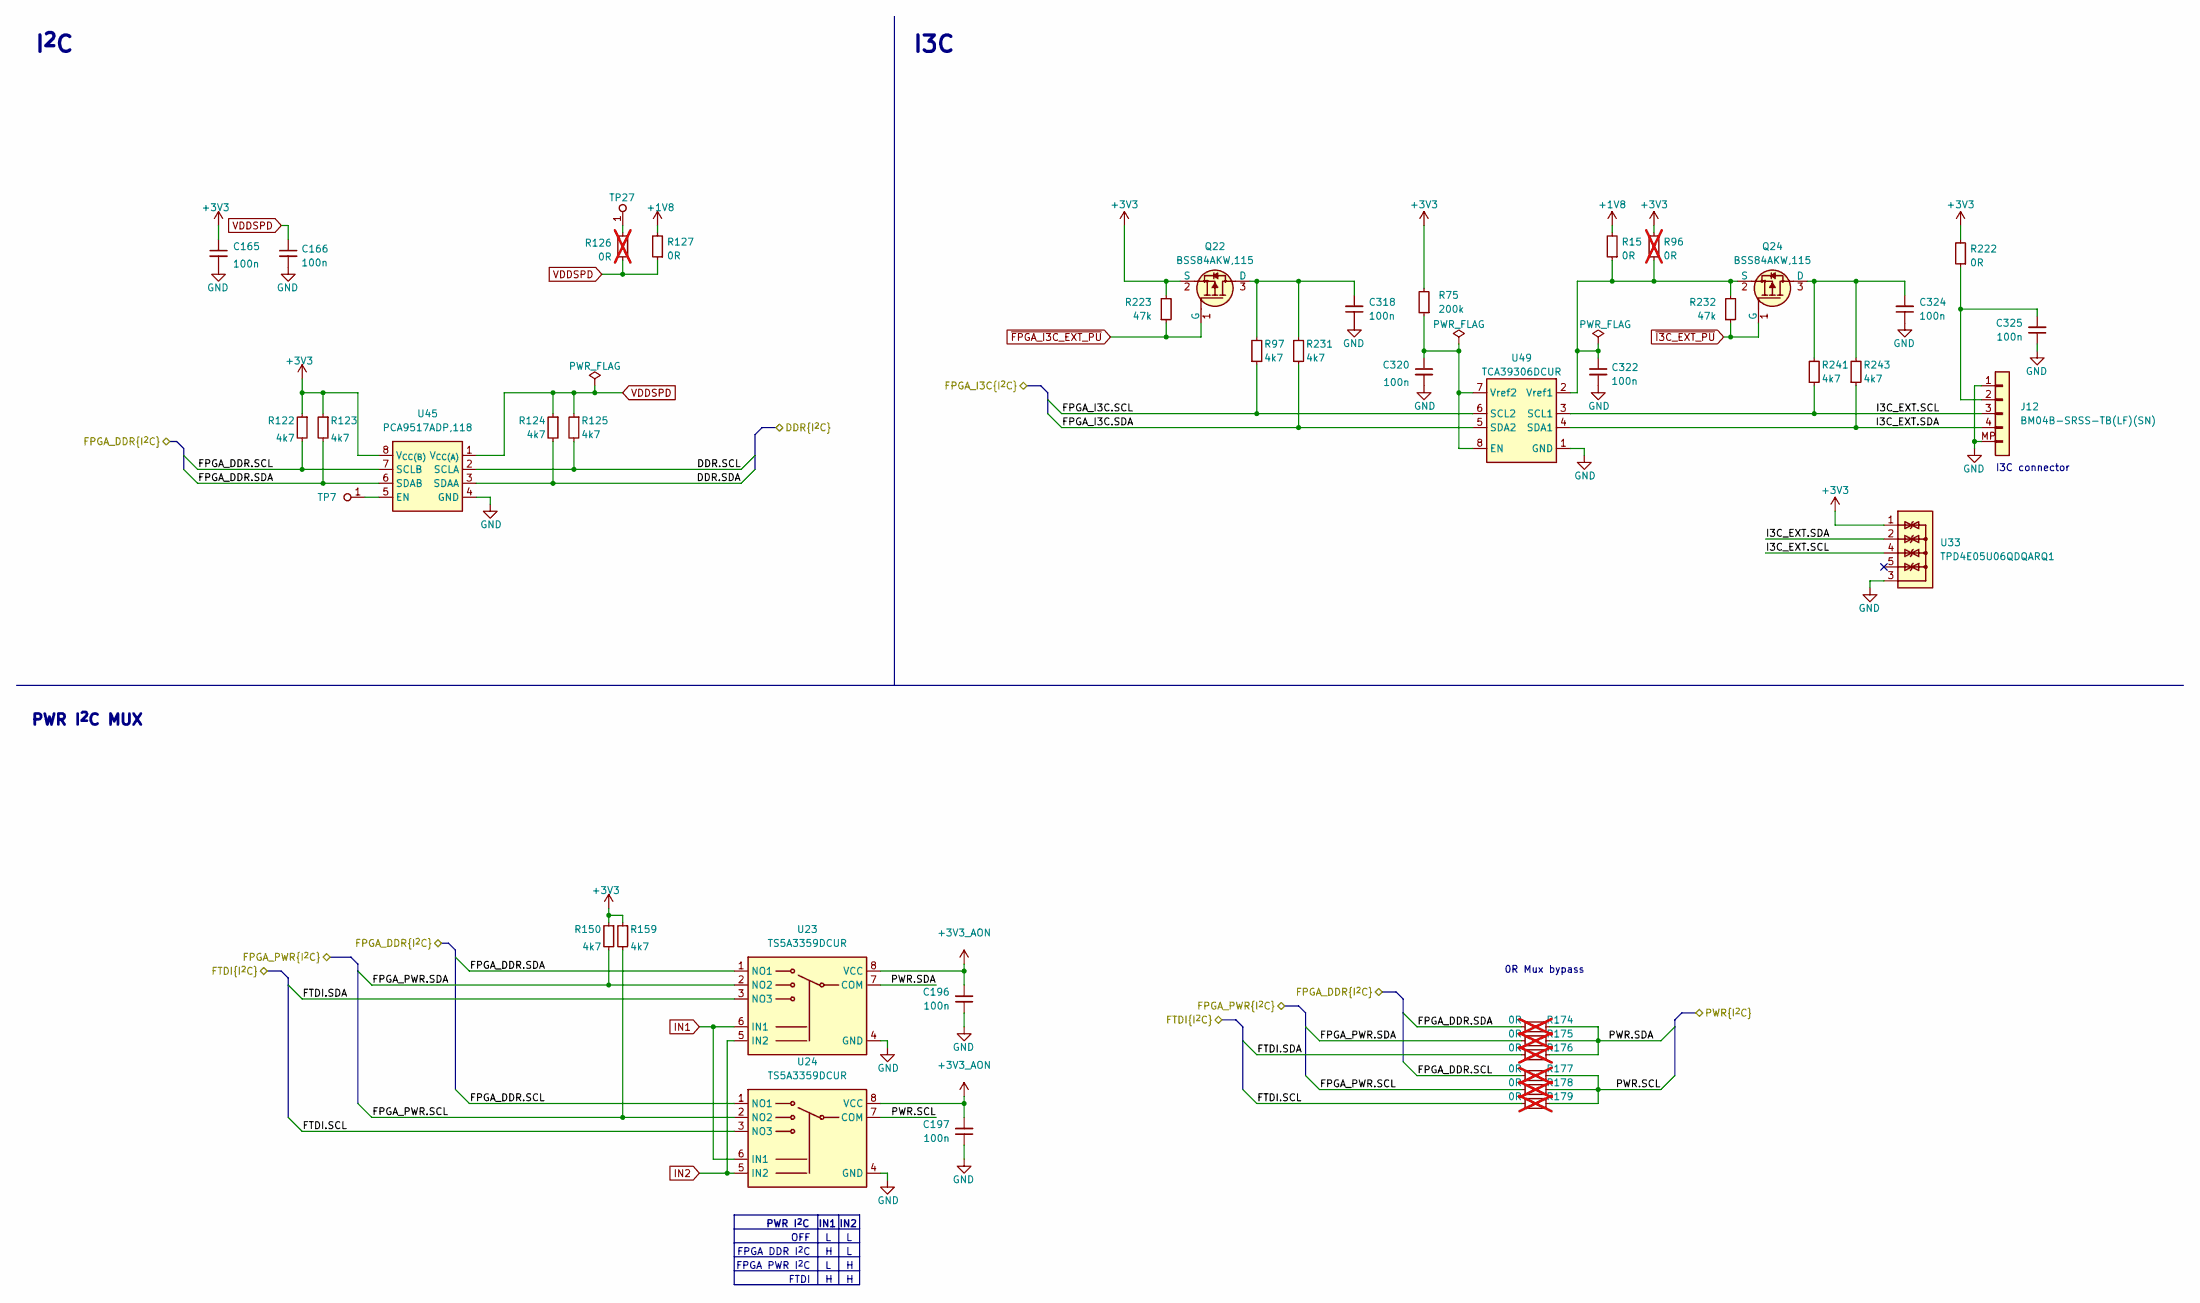
[picture p16: schematic i2c.kicad_sch]

Parts:
C165, C166, C196, C197, C318, C320, C322, C324, C325: C_100n_0402; C_0402_1005Metric; Voltage 50V; MPN GRM155R61H104KE14D
J12: JST_SH_1x4_BM04B-SRSS-TB-LF-SN; Conn_JST_SH_1x4_BM04B-SRSS-TB-LF-SN; MPN BM04B-SRSS-TB(LF)(SN)
Q22, Q24: BSS84AKW; SOT-323; MPN BSS84AKW,115
R15, R127, R222: R_0R_0402; R_0402_1005Metric; MPN ERJ2GE0R00X
R75: R_200k_0402; R_0402_1005Metric; Tolerance 1%; MPN CR0402-FX-2003GLF
R96, R126, R174, R175, R176, R177, R178, R179: R_0R_0402; R_0402_1005Metric; MPN ERJ2GE0R00X; not fitted
R97, R122, R123, R124, R125, R150, R159, R231, R241, R243: R_4k7_0402; R_0402_1005Metric; Tolerance 1%; MPN CR0402-FX-4701GLF
R223, R232: R_47k_0402; R_0402_1005Metric; Tolerance 1%; MPN CR0402-FX-4702GLF
TP7: TP_1mm_SMD; TP_SMD_1mm
TP27: TP_0.75mm_SMD; TP_SMD_0.75mm
U23, U24: TS5A3359_VSSOP; VSSOP-8_2.3x2mm_P0.5mm; MPN TS5A3359DCUR
U33: TPD4E05U06QDQARQ1; USON-10_2.5x1mm_P0.5mm; MPN TPD4E05U06QDQARQ1
U45: PCA9517ADP; TSSOP-8_3x3mm_P0.65mm; MPN PCA9517ADP,118
U49: TCA39306_VSSOP; VSSOP-8_2.3x2mm_P0.5mm; MPN TCA39306DCUR

Connections:
+1V8: R15.2, R127.2
+3V3: C165.1, Q22.2 (S), R75.2, R96.2, R122.1, R123.1, R150.1, R159.1, R222.2, R223.2, U33.1, U33.10, U45.8 (V_{CC(B)})
+3V3_AON: C196.2, C197.2, U23.8 (VCC), U24.8 (VCC)
DDR.SCL: R125.2, U45.2 (SCLA)
DDR.SDA: R124.2, U45.3 (SDAA)
FPGA_DDR.SCL: R122.2, R177.2, U24.1 (NO1), U45.7 (SCLB)
FPGA_DDR.SDA: R123.2, R174.2, U23.1 (NO1), U45.6 (SDAB)
FPGA_I3C.SCL: R97.1, U49.6 (SCL2)
FPGA_I3C.SDA: R231.1, U49.5 (SDA2)
FPGA_PWR.SCL: R159.2, R178.2, U24.2 (NO2)
FPGA_PWR.SDA: R150.2, R175.2, U23.2 (NO2)
FTDI.SCL: R179.2, U24.3 (NO3)
FTDI.SDA: R176.2, U23.3 (NO3)
GND: C165.2, C166.2, C196.1, C197.1, C318.1, C320.2, C322.2, C324.1, C325.1, J12.1, J12.MP, U23.4 (GND), U24.4 (GND), U33.3, U33.8, U45.4 (GND), U49.1 (GND)
I3C_EXT.SCL: J12.3, R241.1, U33.4, U33.7, U49.3 (SCL1)
I3C_EXT.SDA: J12.4, R243.1, U33.2, U33.9, U49.4 (SDA1)
IN1: U23.6 (IN1), U24.6 (IN1)
IN2: U23.5 (IN2), U24.5 (IN2)
unnamed: C318.2, Q22.3 (D), R97.2, R231.2
unnamed: C320.1, R75.1, U49.7 (Vref2), U49.8 (EN)
unnamed: C322.1, Q24.2 (S), R15.1, R96.1, R232.2, U49.2 (Vref1)
unnamed: C324.2, Q24.3 (D), R241.2, R243.2
unnamed: C325.2, J12.2, R222.1
unnamed: R126.1, TP27.1
unnamed: TP7.1, U45.5 (EN)
unnamed: U33.5, U33.6
PWR.SCL: R177.1, R178.1, R179.1, U24.7 (COM)
PWR.SDA: R174.1, R175.1, R176.1, U23.7 (COM)
VDDSPD: C166.1, R124.1, R125.1, R126.2, R127.1, U45.1 (V_{CC(A)})
~FPGA_I3C_EXT_PU: Q22.1 (G), R223.1
~I3C_EXT_PU: Q24.1 (G), R232.1

Notes on the sheet:
PWR I^{2}C MUX
FTDI
I3C
OFF
PWR I^{2}C
I^{2}C
0R Mux bypass
IN2
IN1
FPGA PWR I^{2}C
I3C connector
FPGA DDR I^{2}C
