antmicro/rdimm-ddr5-tester/pcie-connector.kicad_sch

## KiCad design pcie-connector.kicad_sch (2026-05-21)

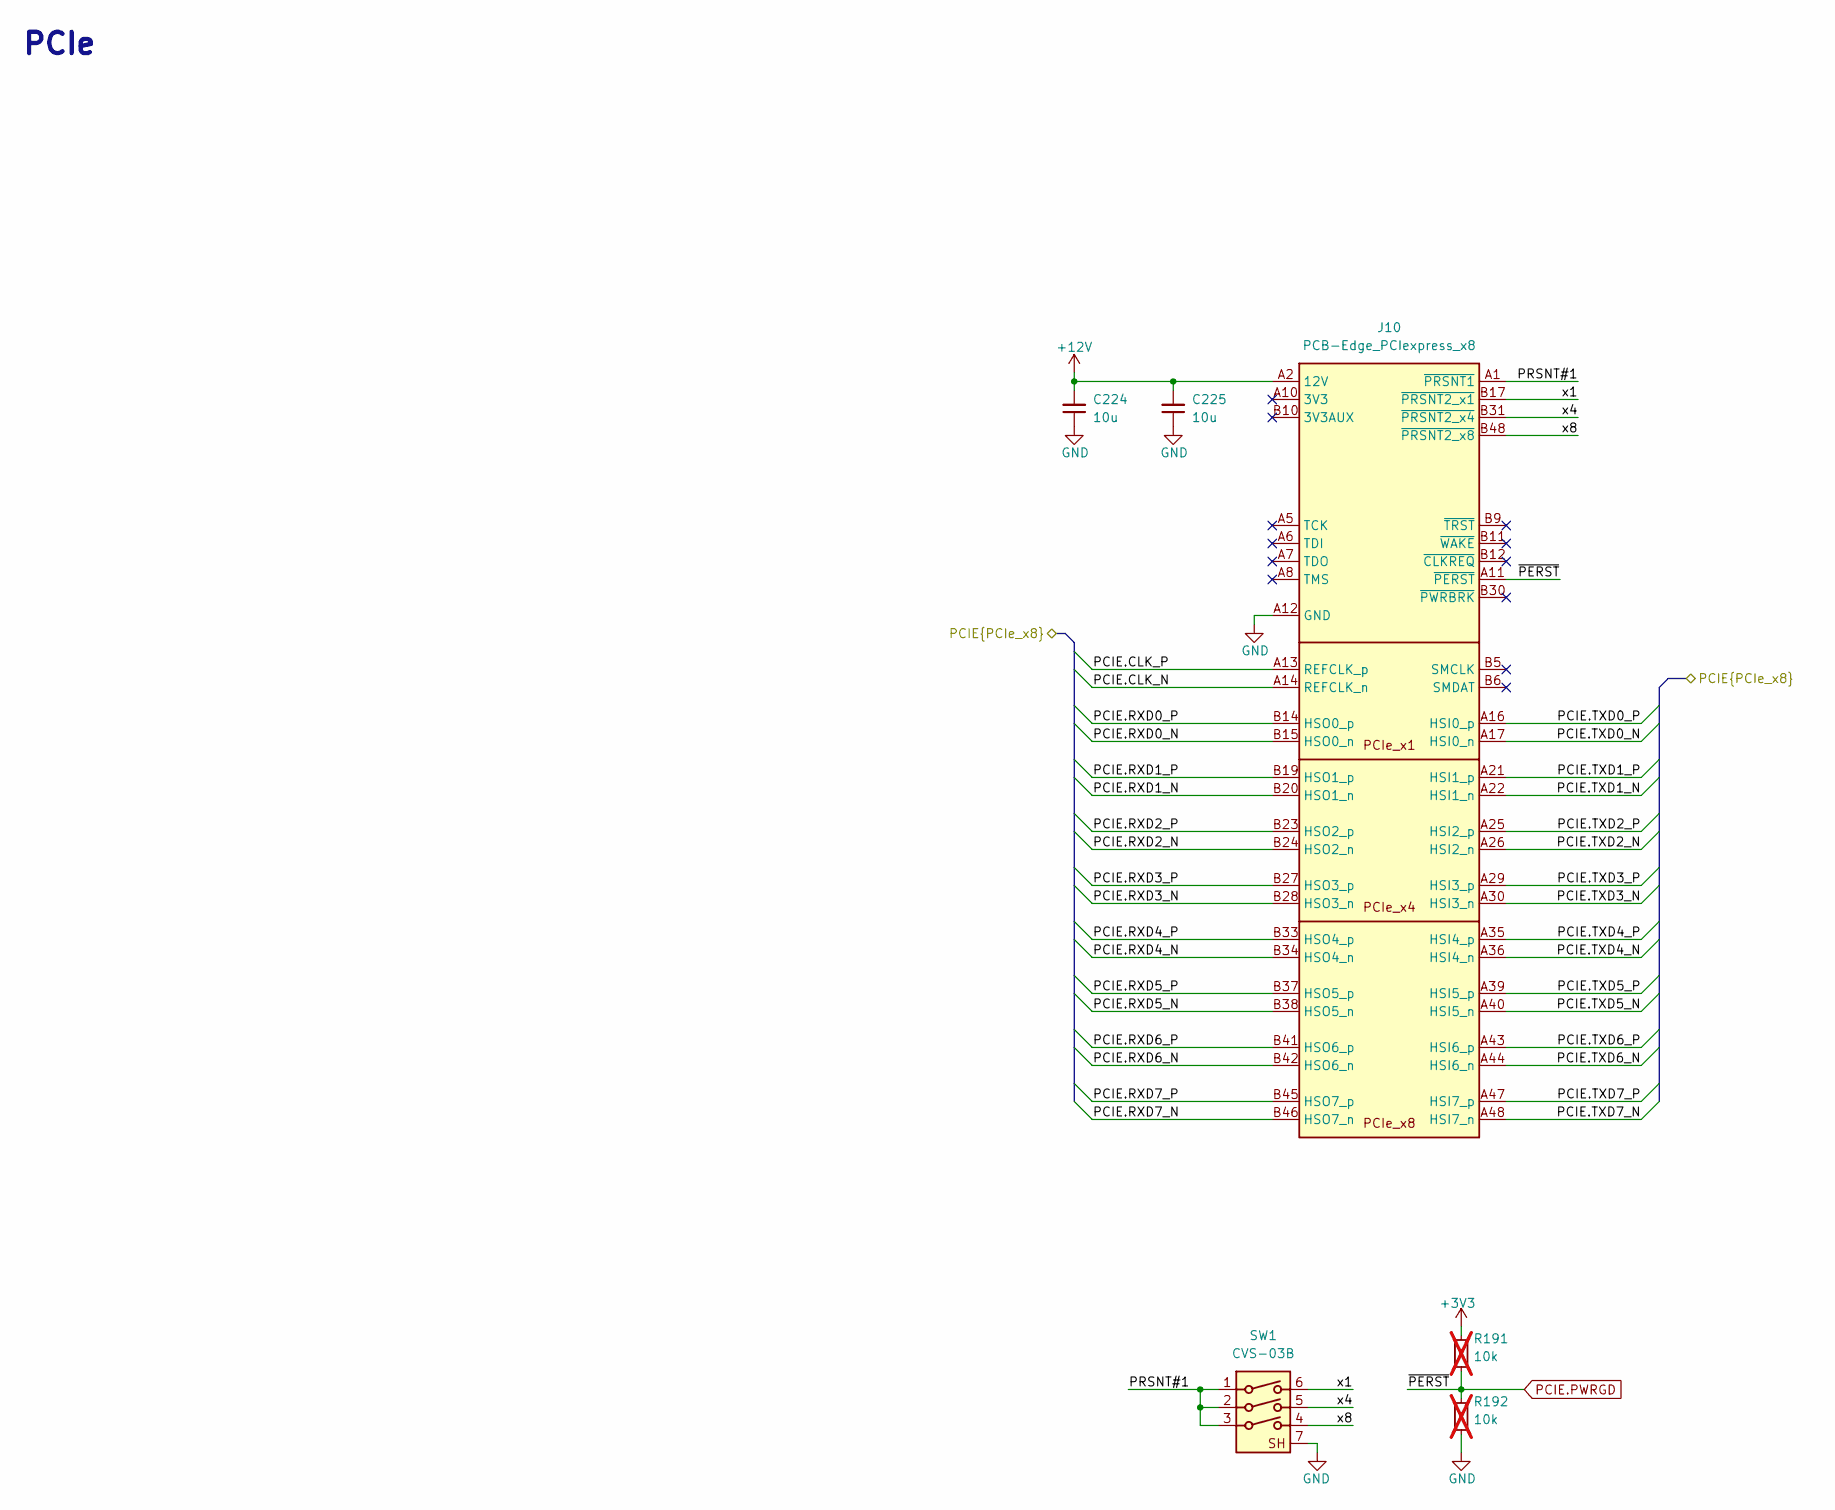
[picture p17: schematic pcie-connector.kicad_sch]

Parts:
C224, C225: C_10u_25V_0603; C_0603_1608Metric; Voltage 25V; MPN C1608X5R1E106M080AC
J10: PCB-Edge_PCIexpress_x8
R191, R192: R_10k_0402; R_0402_1005Metric; Tolerance 1%; MPN CR0402-FX-1002GLF; not fitted
SW1: CVS-03B; SW_DIP_SPSTx03_Slide_Copal_CVS-03xB_W5.9mm_P1mm; MPN CVS-03B

Connections:
+3V3: R191.2
+12V: C224.2, C225.2, J10.A2 (12V), J10.A3 (12V), J10.B1 (12V), J10.B2 (12V), J10.B3 (12V)
GND: C224.1, C225.1, J10.A4 (GND), J10.A12 (GND), J10.A15 (GND), J10.A18 (GND), J10.A20 (GND), J10.A23 (GND), J10.A24 (GND), J10.A27 (GND), J10.A28 (GND), J10.A31 (GND), J10.A34 (GND), J10.A37 (GND), J10.A38 (GND), J10.A41 (GND), J10.A42 (GND), J10.A45 (GND), J10.A46 (GND), J10.A49 (GND), J10.B4 (GND), J10.B7 (GND), J10.B13 (GND), J10.B16 (GND), J10.B18 (GND), J10.B21 (GND), J10.B22 (GND), J10.B25 (GND), J10.B26 (GND), J10.B29 (GND), J10.B32 (GND), J10.B35 (GND), J10.B36 (GND), J10.B39 (GND), J10.B40 (GND), J10.B43 (GND), J10.B44 (GND), J10.B47 (GND), J10.B49 (GND), R192.1, SW1.7
unnamed: J10.A9 (3V3), J10.A10 (3V3), J10.B8 (3V3)
PCIE.CLK_N: J10.A14 (REFCLK_n)
PCIE.CLK_P: J10.A13 (REFCLK_p)
PCIE.PWRGD: J10.A11 (~PERST), R191.1, R192.2
PCIE.RXD0_N: J10.B15 (HSO0_n)
PCIE.RXD0_P: J10.B14 (HSO0_p)
PCIE.RXD1_N: J10.B20 (HSO1_n)
PCIE.RXD1_P: J10.B19 (HSO1_p)
PCIE.RXD2_N: J10.B24 (HSO2_n)
PCIE.RXD2_P: J10.B23 (HSO2_p)
PCIE.RXD3_N: J10.B28 (HSO3_n)
PCIE.RXD3_P: J10.B27 (HSO3_p)
PCIE.RXD4_N: J10.B34 (HSO4_n)
PCIE.RXD4_P: J10.B33 (HSO4_p)
PCIE.RXD5_N: J10.B38 (HSO5_n)
PCIE.RXD5_P: J10.B37 (HSO5_p)
PCIE.RXD6_N: J10.B42 (HSO6_n)
PCIE.RXD6_P: J10.B41 (HSO6_p)
PCIE.RXD7_N: J10.B46 (HSO7_n)
PCIE.RXD7_P: J10.B45 (HSO7_p)
PCIE.TXD0_N: J10.A17 (HSI0_n)
PCIE.TXD0_P: J10.A16 (HSI0_p)
PCIE.TXD1_N: J10.A22 (HSI1_n)
PCIE.TXD1_P: J10.A21 (HSI1_p)
PCIE.TXD2_N: J10.A26 (HSI2_n)
PCIE.TXD2_P: J10.A25 (HSI2_p)
PCIE.TXD3_N: J10.A30 (HSI3_n)
PCIE.TXD3_P: J10.A29 (HSI3_p)
PCIE.TXD4_N: J10.A36 (HSI4_n)
PCIE.TXD4_P: J10.A35 (HSI4_p)
PCIE.TXD5_N: J10.A40 (HSI5_n)
PCIE.TXD5_P: J10.A39 (HSI5_p)
PCIE.TXD6_N: J10.A44 (HSI6_n)
PCIE.TXD6_P: J10.A43 (HSI6_p)
PCIE.TXD7_N: J10.A48 (HSI7_n)
PCIE.TXD7_P: J10.A47 (HSI7_p)
PRSNT#1: J10.A1 (~PRSNT1), SW1.1, SW1.2, SW1.3
x1: J10.B17 (~PRSNT2_x1), SW1.6
x4: J10.B31 (~PRSNT2_x4), SW1.5
x8: J10.B48 (~PRSNT2_x8), SW1.4

Notes on the sheet:
PCIe
