antmicro/rdimm-ddr5-tester/supply.kicad_sch

## KiCad design supply.kicad_sch (2026-05-25)

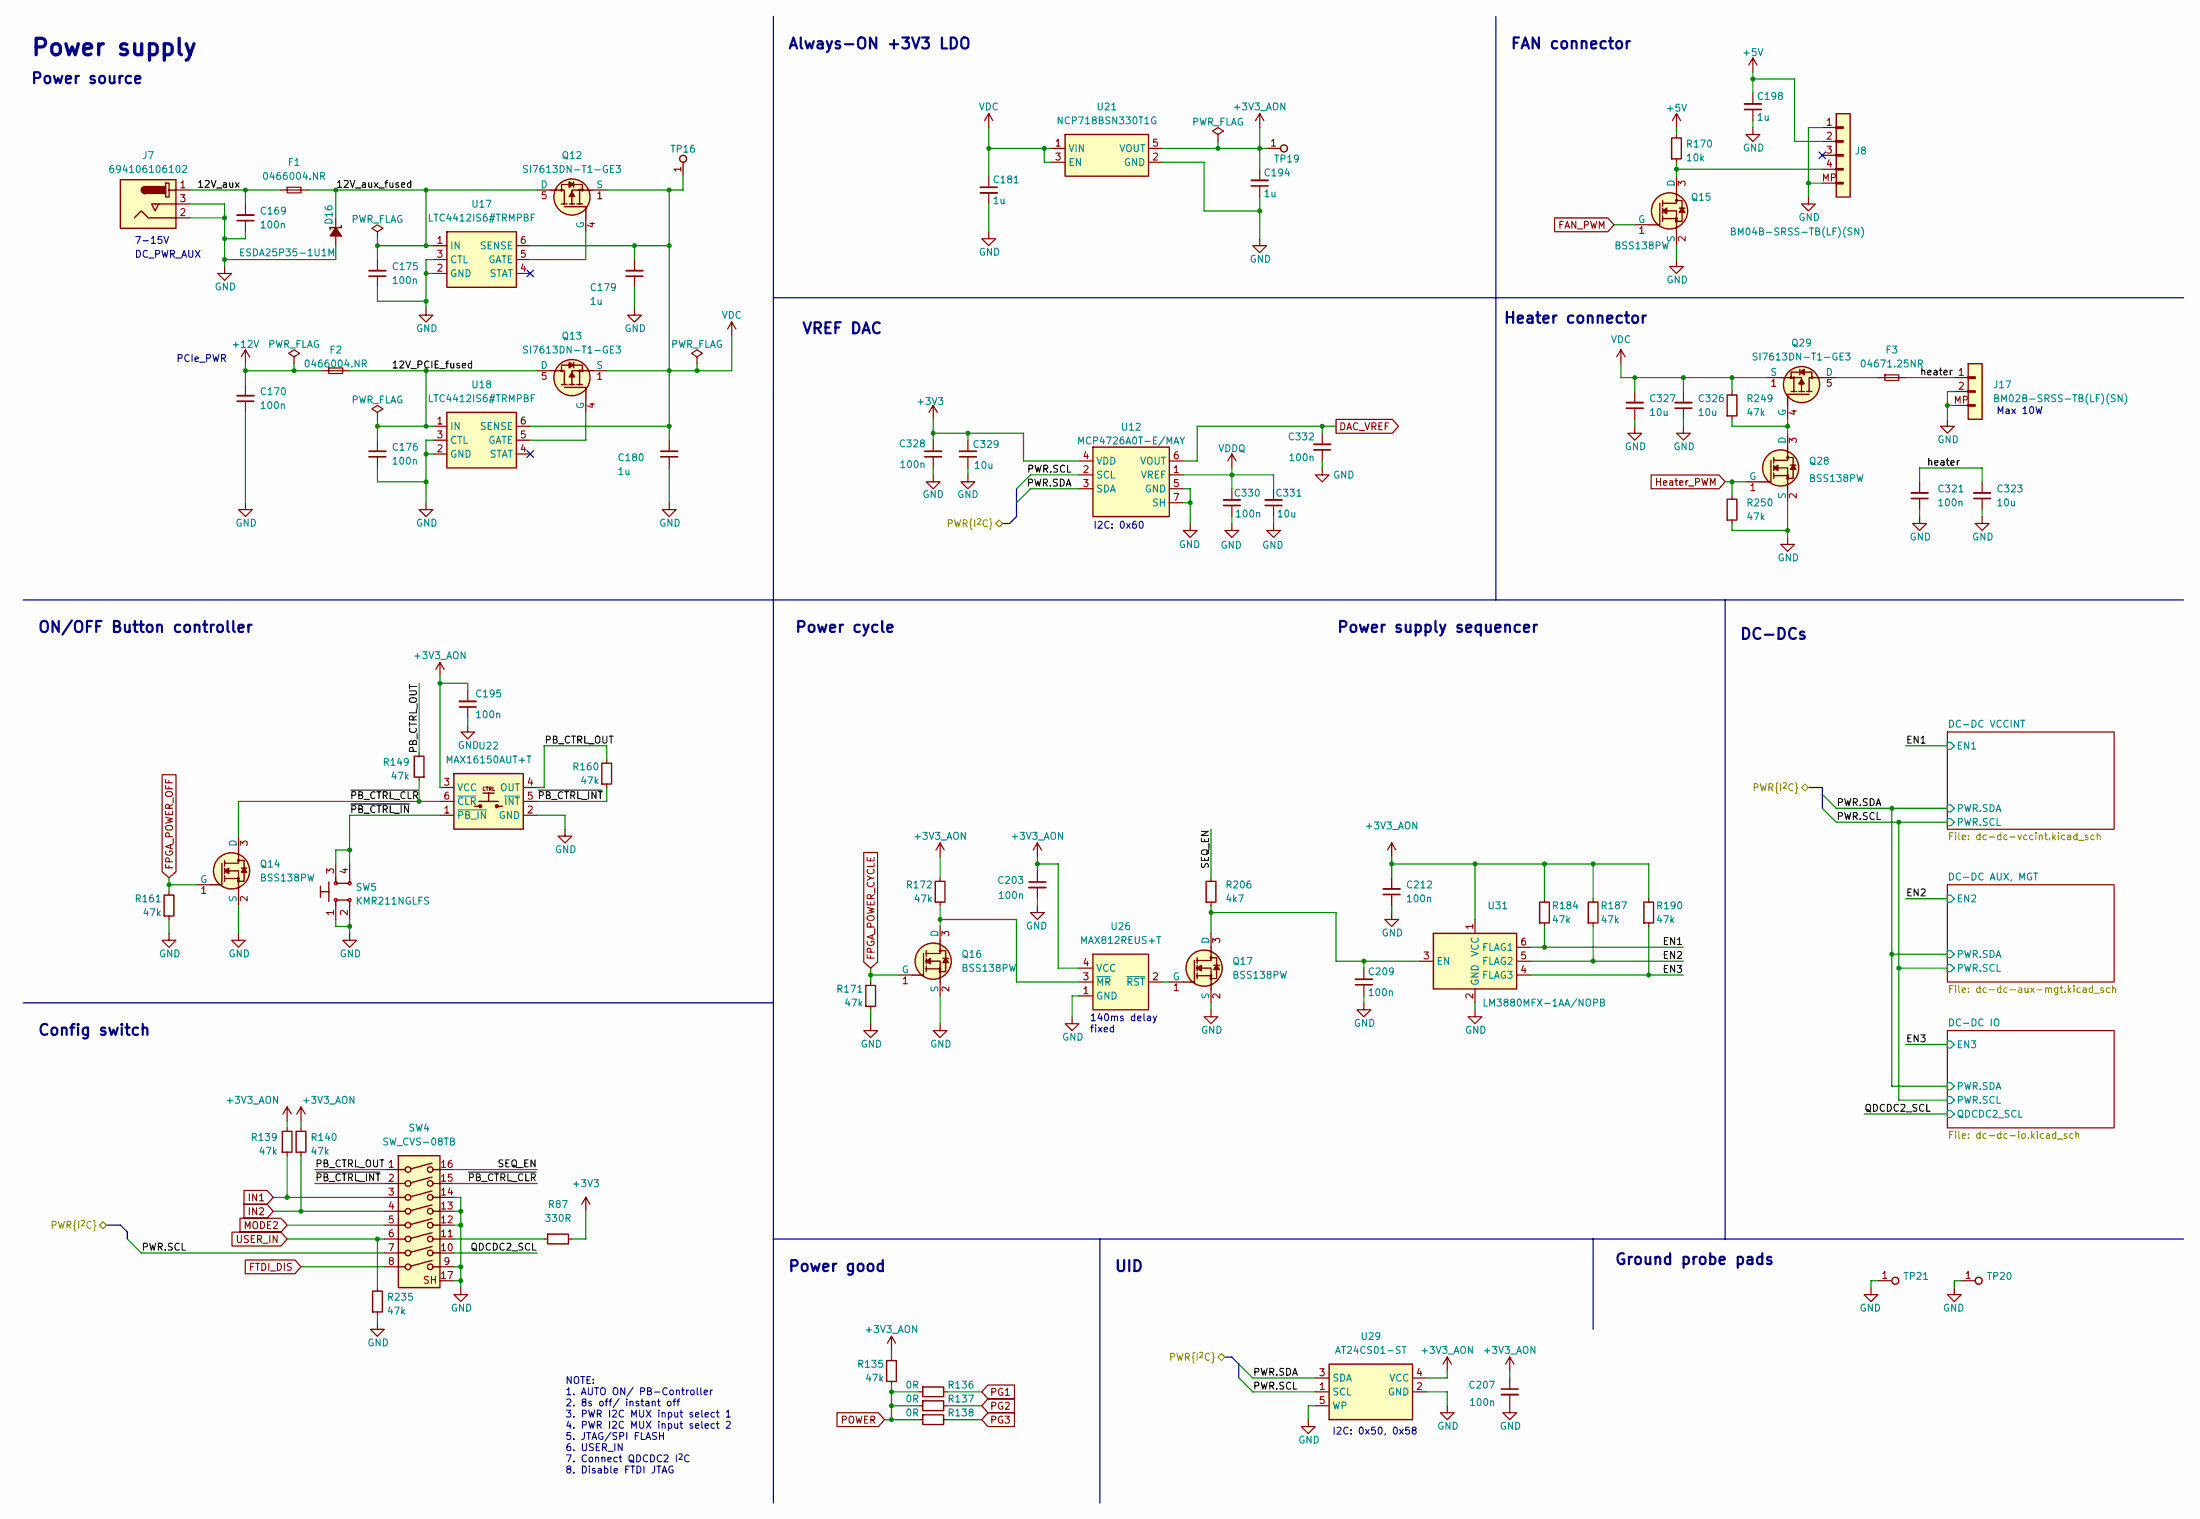
[picture p18: schematic supply.kicad_sch]

Parts:
C169, C170, C175, C176, C195, C203, C207, C209, C212, C321, C328, C330, C332: C_100n_0402; C_0402_1005Metric; Voltage 50V; MPN GRM155R61H104KE14D
C179, C180, C181: C_1u_25V_0603; C_0603_1608Metric; Voltage 25V; MPN CL10A105KA8NNNC
C194, C198: C_1u_0402; C_0402_1005Metric; MPN C1005X6S1A105K050BC
C323, C326, C327: C_10u_25V_0603; C_0603_1608Metric; Voltage 25V; MPN C1608X5R1E106M080AC
C329, C331: C_10u_6.3V_0402; C_0402_1005Metric; Voltage 6.3V; MPN GRM155R60J106ME15D
D16: ESDA25P35-1U1M; QFN-2L_1.6x1x0.55mm; MPN ESDA25P35-1U1M
F1, F2: F_4A_1206; F_1206_3216Metric; MPN 0466004.NR
F3: F_1.25A_0603; F_0603_1608Metric; MPN 04671.25NR
J7: BarrelJack_Pin2mm_694106106102; MPN 694106106102
J8: JST_SH_1x4_BM04B-SRSS-TB-LF-SN; Conn_JST_SH_1x4_BM04B-SRSS-TB-LF-SN; MPN BM04B-SRSS-TB(LF)(SN)
J17: JST_SH_1x2_BM02B-SRSS-TB-LF-SN; Conn_JST_SH_1x2_BM02B-SRSS-TB-LF-SN; MPN BM02B-SRSS-TB(LF)(SN)
Q12, Q13, Q29: SI7613DN-T1-GE3; Vishay_PowerPAK_1212-8_Single; MPN SI7613DN-T1-GE3
Q14, Q15, Q16, Q17, Q28: BSS138PW; SC70-3; MPN BSS138PW
R87: R_330R_0402; R_0402_1005Metric; Tolerance 1%; MPN CR0402-FX-3300GLF
R135, R139, R140, R149, R160, R161, R171, R172, R184, R187, R190, R235, R249, R250: R_47k_0402; R_0402_1005Metric; Tolerance 1%; MPN CR0402-FX-4702GLF
R136, R137, R138: R_0R_0402; R_0402_1005Metric; MPN ERJ2GE0R00X
R170: R_10k_0402; R_0402_1005Metric; Tolerance 1%; MPN CR0402-FX-1002GLF
R206: R_4k7_0402; R_0402_1005Metric; Tolerance 1%; MPN CR0402-FX-4701GLF
SW4: SW_CVS-08TB; SW_DIP_SPSTx08_Slide_Copal_CVS-08xB_W5.9mm_P1mm; MPN CVS-08TB
SW5: SW_KMR211NGLFS_SMD; MPN KMR211NGLFS
TP16, TP19: TP_1mm_SMD; TP_SMD_1mm
TP20, TP21: TP_1206_SMD_RCW-0C; MPN RCW-0C
U12: MCP4726A0T_DFN; DFN-6-1EP_2x2mm_P0.65mm_EP1x1.6mm; MPN MCP4726A0T-E/MAY
U17, U18: LTC4412IS6; SOT-23-6; MPN LTC4412IS6#TRMPBF
U21: NCP718BSN330T1G; SOT-23-5; MPN NCP718BSN330T1G
U22: MAX16150A_SOT; SOT-23-6; MPN MAX16150AUT+T
U26: MAX812REUS+T; SOT-143-4; MPN MAX812REUS+T
U29: AT24CS01_SOT23; SOT-23-5; MPN AT24CS01-ST
U31: LM3880; SOT-23-6; MPN LM3880MFX-1AA/NOPB

Connections:
12V_PCIE_fused: C176.2, F2.2, Q13.5 (D), U18.1 (IN)
12V_aux: C169.2, F1.1, J7.1
12V_aux_fused: C175.2, D16.1 (C), F1.2, Q12.5 (D), U17.1 (IN)
+3V3: C328.2, C329.2, R87.2, U12.4 (VDD)
+3V3_AON: C194.2, C195.2, C203.1, C207.1, C212.2, R135.2, R139.2, R140.2, R172.2, R184.2, R187.2, R190.2, TP19.1, U21.5 (VOUT), U22.3 (VCC), U26.4 (VCC), U29.4 (VCC), U31.1 (VCC)
+5V: C198.2, J8.2, R170.2
+12V: C170.2, F2.1
DAC_VREF: C332.2, U12.6 (VOUT)
EN1: R184.1, U31.6 (FLAG1)
EN2: R187.1, U31.5 (FLAG2)
EN3: R190.1, U31.4 (FLAG3)
FAN_PWM: Q15.1 (G)
FPGA_POWER_CYCLE: Q16.1 (G), R171.2
FPGA_POWER_OFF: Q14.1 (G), R161.2
FTDI_DIS: SW4.8
GND: C169.1, C170.1, C175.1, C176.1, C179.1, C180.1, C181.2, C194.1, C195.1, C198.1, C203.2, C207.2, C209.1, C212.1, C321.1, C323.1, C326.1, C327.1, C328.1, C329.1, C330.1, C331.1, C332.1, D16.2 (A), J7.2, J7.3, J8.1, J8.MP, J17.2, J17.MP, Q14.2 (S), Q15.2 (S), Q16.2 (S), Q17.2 (S), Q28.2 (S), R161.1, R171.1, R235.1, R250.1, SW4.9, SW4.12, SW4.13, SW4.14, SW4.17, SW5.1, SW5.2, TP20.1, TP21.1, U12.5 (GND), U12.7 (SH), U17.2 (GND), U17.3 (CTL), U18.2 (GND), U18.3 (CTL), U21.2 (GND), U22.2 (GND), U26.1 (GND), U29.2 (GND), U29.5 (WP), U31.2 (GND)
Heater_PWM: Q28.1 (G), R250.2
IN1: R139.1, SW4.3
IN2: R140.1, SW4.4
MODE2: SW4.5
unnamed: C209.2, Q17.3 (D), R206.1, U31.3 (EN)
unnamed: F3.1, Q29.5 (D)
unnamed: J8.4, Q15.3 (D), R170.1
unnamed: Q12.4 (G), U17.5 (GATE)
unnamed: Q13.4 (G), U18.5 (GATE)
unnamed: Q16.3 (D), R172.1, U26.3 (~MR)
unnamed: Q17.1 (G), U26.2 (~RST)
unnamed: Q28.3 (D), Q29.4 (G), R249.1
unnamed: R87.1, SW4.11
PB_CTRL_OUT: R149.2, R160.2, SW4.1, U22.4 (OUT)
PG1: R136.2
PG2: R137.2
PG3: R138.2
POWER: R135.1, R136.1, R137.1, R138.1
PWR.SCL: SW4.7, U12.2 (SCL), U29.1 (SCL)
PWR.SDA: U12.3 (SDA), U29.3 (SDA)
QDCDC2_SCL: SW4.10
SEQ_EN: R206.2, SW4.16
USER_IN: R235.2, SW4.6
VDC: C179.2, C180.2, C181.1, C326.2, C327.2, Q12.1 (S), Q12.2 (S), Q12.3 (S), Q13.1 (S), Q13.2 (S), Q13.3 (S), Q29.1 (S), Q29.2 (S), Q29.3 (S), R249.2, TP16.1, U17.6 (SENSE), U18.6 (SENSE), U21.1 (VIN), U21.3 (EN)
VDDQ: C330.2, C331.2, U12.1 (VREF)
heater: C321.2, C323.2, F3.2, J17.1
~PB_CTRL_CLR: Q14.3 (D), R149.1, SW4.15, U22.6 (~CLR)
~PB_CTRL_INT: R160.1, SW4.2, U22.5 (~INT)
~PB_CTRL_IN: SW5.3, SW5.4, U22.1 (~PB_IN)

Notes on the sheet:
Power source
I2C: 0x50, 0x58
VREF DAC
I2C: 0x60
Max 10W
7-15V
Power supply sequencer
Always-ON +3V3 LDO
Power cycle
Config switch
140ms delay fixed
FAN connector
UID
ON/OFF Button controller
PCIe_PWR
NOTE: 1. AUTO ON/ PB-Controller 2. 8s off/ instant off 3. PWR I2C MUX input select 1 4. PWR I2C MUX input select 2 5. JTAG/SPI FLASH 6. USER_IN 7. Connect QDCDC2 I^{2}C 8. Disable FTDI JTAG
DC_PWR_AUX
Ground probe pads
Power supply
DC-DCs
Heater connector
Power good
